oresat/oresat-c3-rf/eagle/ax5032-module-breakout/outputs/DVK2C-breakout.png

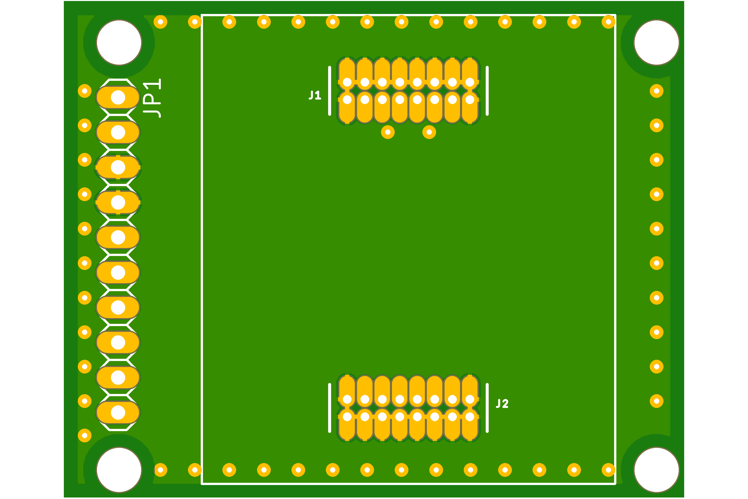
eagle/ax5032-module-breakout/outputs/DVK2C-breakout.png
