oresat/oresat-c3-rf/AxSem_Profiles/AX_C3_L_RX/TESTS/obj/Debug/TESTS/main.rst

                                      1 ;--------------------------------------------------------
                                      2 ; File Created by SDCC : free open source ANSI-C Compiler
                                      3 ; Version 3.6.0 #9615 (MINGW64)
                                      4 ;--------------------------------------------------------
                                      5 	.module main
                                      6 	.optsdcc -mmcs51 --model-small
                                      7 	
                                      8 ;--------------------------------------------------------
                                      9 ; Public variables in this module
                                     10 ;--------------------------------------------------------
                                     11 	.globl _non_fourfsk_tx1010_pattern
                                     12 	.globl _fourfsk_tx1010_pattern
                                     13 	.globl _onepattern
                                     14 	.globl _txpattern
                                     15 	.globl _main
                                     16 	.globl __sdcc_external_startup
                                     17 	.globl _set_receiveber
                                     18 	.globl _set_transmit
                                     19 	.globl _set_cw
                                     20 	.globl _lcd2_display_radio_error
                                     21 	.globl _delay_ms
                                     22 	.globl _axradio_commsleepexit
                                     23 	.globl _axradio_setup_pincfg2
                                     24 	.globl _axradio_setup_pincfg1
                                     25 	.globl _axradio_get_transmitter_pa_type
                                     26 	.globl _axradio_check_fourfsk_modulation
                                     27 	.globl _axradio_agc_thaw
                                     28 	.globl _axradio_agc_freeze
                                     29 	.globl _axradio_conv_freq_tohz
                                     30 	.globl _axradio_transmit
                                     31 	.globl _axradio_get_pllvcoi
                                     32 	.globl _axradio_get_pllrange
                                     33 	.globl _axradio_set_mode
                                     34 	.globl _axradio_cansleep
                                     35 	.globl _axradio_init
                                     36 	.globl _lcd2_writenum32
                                     37 	.globl _lcd2_writehex16
                                     38 	.globl _lcd2_writenum16
                                     39 	.globl _lcd2_writestr
                                     40 	.globl _lcd2_clear
                                     41 	.globl _lcd2_setpos
                                     42 	.globl _lcd2_portinit
                                     43 	.globl _lcd2_init
                                     44 	.globl _lcd2_txidle
                                     45 	.globl _pn15_output
                                     46 	.globl _pn15_advance
                                     47 	.globl _pn9_advance
                                     48 	.globl _wtimer_runcallbacks
                                     49 	.globl _wtimer_idle
                                     50 	.globl _wtimer_init
                                     51 	.globl _wtimer1_setconfig
                                     52 	.globl _wtimer0_setconfig
                                     53 	.globl _flash_apply_calibration
                                     54 	.globl _enter_sleep
                                     55 	.globl _hweight8
                                     56 	.globl _PORTC_7
                                     57 	.globl _PORTC_6
                                     58 	.globl _PORTC_5
                                     59 	.globl _PORTC_4
                                     60 	.globl _PORTC_3
                                     61 	.globl _PORTC_2
                                     62 	.globl _PORTC_1
                                     63 	.globl _PORTC_0
                                     64 	.globl _PORTB_7
                                     65 	.globl _PORTB_6
                                     66 	.globl _PORTB_5
                                     67 	.globl _PORTB_4
                                     68 	.globl _PORTB_3
                                     69 	.globl _PORTB_2
                                     70 	.globl _PORTB_1
                                     71 	.globl _PORTB_0
                                     72 	.globl _PORTA_7
                                     73 	.globl _PORTA_6
                                     74 	.globl _PORTA_5
                                     75 	.globl _PORTA_4
                                     76 	.globl _PORTA_3
                                     77 	.globl _PORTA_2
                                     78 	.globl _PORTA_1
                                     79 	.globl _PORTA_0
                                     80 	.globl _PINC_7
                                     81 	.globl _PINC_6
                                     82 	.globl _PINC_5
                                     83 	.globl _PINC_4
                                     84 	.globl _PINC_3
                                     85 	.globl _PINC_2
                                     86 	.globl _PINC_1
                                     87 	.globl _PINC_0
                                     88 	.globl _PINB_7
                                     89 	.globl _PINB_6
                                     90 	.globl _PINB_5
                                     91 	.globl _PINB_4
                                     92 	.globl _PINB_3
                                     93 	.globl _PINB_2
                                     94 	.globl _PINB_1
                                     95 	.globl _PINB_0
                                     96 	.globl _PINA_7
                                     97 	.globl _PINA_6
                                     98 	.globl _PINA_5
                                     99 	.globl _PINA_4
                                    100 	.globl _PINA_3
                                    101 	.globl _PINA_2
                                    102 	.globl _PINA_1
                                    103 	.globl _PINA_0
                                    104 	.globl _CY
                                    105 	.globl _AC
                                    106 	.globl _F0
                                    107 	.globl _RS1
                                    108 	.globl _RS0
                                    109 	.globl _OV
                                    110 	.globl _F1
                                    111 	.globl _P
                                    112 	.globl _IP_7
                                    113 	.globl _IP_6
                                    114 	.globl _IP_5
                                    115 	.globl _IP_4
                                    116 	.globl _IP_3
                                    117 	.globl _IP_2
                                    118 	.globl _IP_1
                                    119 	.globl _IP_0
                                    120 	.globl _EA
                                    121 	.globl _IE_7
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
                                    198 	.globl _WTCFGB
                                    199 	.globl _WTCFGA
                                    200 	.globl _WDTRESET
                                    201 	.globl _WDTCFG
                                    202 	.globl _U1STATUS
                                    203 	.globl _U1SHREG
                                    204 	.globl _U1MODE
                                    205 	.globl _U1CTRL
                                    206 	.globl _U0STATUS
                                    207 	.globl _U0SHREG
                                    208 	.globl _U0MODE
                                    209 	.globl _U0CTRL
                                    210 	.globl _T2STATUS
                                    211 	.globl _T2PERIOD
                                    212 	.globl _T2PERIOD1
                                    213 	.globl _T2PERIOD0
                                    214 	.globl _T2MODE
                                    215 	.globl _T2CNT
                                    216 	.globl _T2CNT1
                                    217 	.globl _T2CNT0
                                    218 	.globl _T2CLKSRC
                                    219 	.globl _T1STATUS
                                    220 	.globl _T1PERIOD
                                    221 	.globl _T1PERIOD1
                                    222 	.globl _T1PERIOD0
                                    223 	.globl _T1MODE
                                    224 	.globl _T1CNT
                                    225 	.globl _T1CNT1
                                    226 	.globl _T1CNT0
                                    227 	.globl _T1CLKSRC
                                    228 	.globl _T0STATUS
                                    229 	.globl _T0PERIOD
                                    230 	.globl _T0PERIOD1
                                    231 	.globl _T0PERIOD0
                                    232 	.globl _T0MODE
                                    233 	.globl _T0CNT
                                    234 	.globl _T0CNT1
                                    235 	.globl _T0CNT0
                                    236 	.globl _T0CLKSRC
                                    237 	.globl _SPSTATUS
                                    238 	.globl _SPSHREG
                                    239 	.globl _SPMODE
                                    240 	.globl _SPCLKSRC
                                    241 	.globl _RADIOSTAT
                                    242 	.globl _RADIOSTAT1
                                    243 	.globl _RADIOSTAT0
                                    244 	.globl _RADIODATA
                                    245 	.globl _RADIODATA3
                                    246 	.globl _RADIODATA2
                                    247 	.globl _RADIODATA1
                                    248 	.globl _RADIODATA0
                                    249 	.globl _RADIOADDR
                                    250 	.globl _RADIOADDR1
                                    251 	.globl _RADIOADDR0
                                    252 	.globl _RADIOACC
                                    253 	.globl _OC1STATUS
                                    254 	.globl _OC1PIN
                                    255 	.globl _OC1MODE
                                    256 	.globl _OC1COMP
                                    257 	.globl _OC1COMP1
                                    258 	.globl _OC1COMP0
                                    259 	.globl _OC0STATUS
                                    260 	.globl _OC0PIN
                                    261 	.globl _OC0MODE
                                    262 	.globl _OC0COMP
                                    263 	.globl _OC0COMP1
                                    264 	.globl _OC0COMP0
                                    265 	.globl _NVSTATUS
                                    266 	.globl _NVKEY
                                    267 	.globl _NVDATA
                                    268 	.globl _NVDATA1
                                    269 	.globl _NVDATA0
                                    270 	.globl _NVADDR
                                    271 	.globl _NVADDR1
                                    272 	.globl _NVADDR0
                                    273 	.globl _IC1STATUS
                                    274 	.globl _IC1MODE
                                    275 	.globl _IC1CAPT
                                    276 	.globl _IC1CAPT1
                                    277 	.globl _IC1CAPT0
                                    278 	.globl _IC0STATUS
                                    279 	.globl _IC0MODE
                                    280 	.globl _IC0CAPT
                                    281 	.globl _IC0CAPT1
                                    282 	.globl _IC0CAPT0
                                    283 	.globl _PORTR
                                    284 	.globl _PORTC
                                    285 	.globl _PORTB
                                    286 	.globl _PORTA
                                    287 	.globl _PINR
                                    288 	.globl _PINC
                                    289 	.globl _PINB
                                    290 	.globl _PINA
                                    291 	.globl _DIRR
                                    292 	.globl _DIRC
                                    293 	.globl _DIRB
                                    294 	.globl _DIRA
                                    295 	.globl _DBGLNKSTAT
                                    296 	.globl _DBGLNKBUF
                                    297 	.globl _CODECONFIG
                                    298 	.globl _CLKSTAT
                                    299 	.globl _CLKCON
                                    300 	.globl _ANALOGCOMP
                                    301 	.globl _ADCCONV
                                    302 	.globl _ADCCLKSRC
                                    303 	.globl _ADCCH3CONFIG
                                    304 	.globl _ADCCH2CONFIG
                                    305 	.globl _ADCCH1CONFIG
                                    306 	.globl _ADCCH0CONFIG
                                    307 	.globl __XPAGE
                                    308 	.globl _XPAGE
                                    309 	.globl _SP
                                    310 	.globl _PSW
                                    311 	.globl _PCON
                                    312 	.globl _IP
                                    313 	.globl _IE
                                    314 	.globl _EIP
                                    315 	.globl _EIE
                                    316 	.globl _E2IP
                                    317 	.globl _E2IE
                                    318 	.globl _DPS
                                    319 	.globl _DPTR1
                                    320 	.globl _DPTR0
                                    321 	.globl _DPL1
                                    322 	.globl _DPL
                                    323 	.globl _DPH1
                                    324 	.globl _DPH
                                    325 	.globl _B
                                    326 	.globl _ACC
                                    327 	.globl _txdata
                                    328 	.globl _XTALREADY
                                    329 	.globl _XTALOSC
                                    330 	.globl _XTALAMPL
                                    331 	.globl _SILICONREV
                                    332 	.globl _SCRATCH3
                                    333 	.globl _SCRATCH2
                                    334 	.globl _SCRATCH1
                                    335 	.globl _SCRATCH0
                                    336 	.globl _RADIOMUX
                                    337 	.globl _RADIOFSTATADDR
                                    338 	.globl _RADIOFSTATADDR1
                                    339 	.globl _RADIOFSTATADDR0
                                    340 	.globl _RADIOFDATAADDR
                                    341 	.globl _RADIOFDATAADDR1
                                    342 	.globl _RADIOFDATAADDR0
                                    343 	.globl _OSCRUN
                                    344 	.globl _OSCREADY
                                    345 	.globl _OSCFORCERUN
                                    346 	.globl _OSCCALIB
                                    347 	.globl _MISCCTRL
                                    348 	.globl _LPXOSCGM
                                    349 	.globl _LPOSCREF
                                    350 	.globl _LPOSCREF1
                                    351 	.globl _LPOSCREF0
                                    352 	.globl _LPOSCPER
                                    353 	.globl _LPOSCPER1
                                    354 	.globl _LPOSCPER0
                                    355 	.globl _LPOSCKFILT
                                    356 	.globl _LPOSCKFILT1
                                    357 	.globl _LPOSCKFILT0
                                    358 	.globl _LPOSCFREQ
                                    359 	.globl _LPOSCFREQ1
                                    360 	.globl _LPOSCFREQ0
                                    361 	.globl _LPOSCCONFIG
                                    362 	.globl _PINSEL
                                    363 	.globl _PINCHGC
                                    364 	.globl _PINCHGB
                                    365 	.globl _PINCHGA
                                    366 	.globl _PALTRADIO
                                    367 	.globl _PALTC
                                    368 	.globl _PALTB
                                    369 	.globl _PALTA
                                    370 	.globl _INTCHGC
                                    371 	.globl _INTCHGB
                                    372 	.globl _INTCHGA
                                    373 	.globl _EXTIRQ
                                    374 	.globl _GPIOENABLE
                                    375 	.globl _ANALOGA
                                    376 	.globl _FRCOSCREF
                                    377 	.globl _FRCOSCREF1
                                    378 	.globl _FRCOSCREF0
                                    379 	.globl _FRCOSCPER
                                    380 	.globl _FRCOSCPER1
                                    381 	.globl _FRCOSCPER0
                                    382 	.globl _FRCOSCKFILT
                                    383 	.globl _FRCOSCKFILT1
                                    384 	.globl _FRCOSCKFILT0
                                    385 	.globl _FRCOSCFREQ
                                    386 	.globl _FRCOSCFREQ1
                                    387 	.globl _FRCOSCFREQ0
                                    388 	.globl _FRCOSCCTRL
                                    389 	.globl _FRCOSCCONFIG
                                    390 	.globl _DMA1CONFIG
                                    391 	.globl _DMA1ADDR
                                    392 	.globl _DMA1ADDR1
                                    393 	.globl _DMA1ADDR0
                                    394 	.globl _DMA0CONFIG
                                    395 	.globl _DMA0ADDR
                                    396 	.globl _DMA0ADDR1
                                    397 	.globl _DMA0ADDR0
                                    398 	.globl _ADCTUNE2
                                    399 	.globl _ADCTUNE1
                                    400 	.globl _ADCTUNE0
                                    401 	.globl _ADCCH3VAL
                                    402 	.globl _ADCCH3VAL1
                                    403 	.globl _ADCCH3VAL0
                                    404 	.globl _ADCCH2VAL
                                    405 	.globl _ADCCH2VAL1
                                    406 	.globl _ADCCH2VAL0
                                    407 	.globl _ADCCH1VAL
                                    408 	.globl _ADCCH1VAL1
                                    409 	.globl _ADCCH1VAL0
                                    410 	.globl _ADCCH0VAL
                                    411 	.globl _ADCCH0VAL1
                                    412 	.globl _ADCCH0VAL0
                                    413 	.globl _acquire_agc
                                    414 	.globl _errors2
                                    415 	.globl _errors
                                    416 	.globl _bytes
                                    417 	.globl _scr
                                    418 	.globl _BER_TEST
                                    419 	.globl _coldstart
                                    420 	.globl _axradio_statuschange
                                    421 	.globl _enable_radio_interrupt_in_mcu_pin
                                    422 	.globl _disable_radio_interrupt_in_mcu_pin
                                    423 ;--------------------------------------------------------
                                    424 ; special function registers
                                    425 ;--------------------------------------------------------
                                    426 	.area RSEG    (ABS,DATA)
      000000                        427 	.org 0x0000
                           0000E0   428 G$ACC$0$0 == 0x00e0
                           0000E0   429 _ACC	=	0x00e0
                           0000F0   430 G$B$0$0 == 0x00f0
                           0000F0   431 _B	=	0x00f0
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
      000028                        994 _bytes::
      000028                        995 	.ds 4
                           00000A   996 G$errors$0$0==.
      00002C                        997 _errors::
      00002C                        998 	.ds 4
                           00000E   999 G$errors2$0$0==.
      000030                       1000 _errors2::
      000030                       1001 	.ds 4
                           000012  1002 G$acquire_agc$0$0==.
      000034                       1003 _acquire_agc::
      000034                       1004 	.ds 1
                           000013  1005 Lmain.process_ber$i$2$344==.
      000035                       1006 _process_ber_i_2_344:
      000035                       1007 	.ds 1
                           000014  1008 Lmain.process_ber$sloc0$1$0==.
      000036                       1009 _process_ber_sloc0_1_0:
      000036                       1010 	.ds 1
                           000015  1011 Lmain.process_ber$sloc1$1$0==.
      000037                       1012 _process_ber_sloc1_1_0:
      000037                       1013 	.ds 1
                           000016  1014 Lmain.si_write_reg$data$1$403==.
      000038                       1015 _si_write_reg_PARM_2:
      000038                       1016 	.ds 4
                                   1017 ;--------------------------------------------------------
                                   1018 ; overlayable items in internal ram 
                                   1019 ;--------------------------------------------------------
                                   1020 	.area	OSEG    (OVR,DATA)
                                   1021 ;--------------------------------------------------------
                                   1022 ; Stack segment in internal ram 
                                   1023 ;--------------------------------------------------------
                                   1024 	.area	SSEG
      000050                       1025 __start__stack:
      000050                       1026 	.ds	1
                                   1027 
                                   1028 ;--------------------------------------------------------
                                   1029 ; indirectly addressable internal ram data
                                   1030 ;--------------------------------------------------------
                                   1031 	.area ISEG    (DATA)
                                   1032 ;--------------------------------------------------------
                                   1033 ; absolute internal ram data
                                   1034 ;--------------------------------------------------------
                                   1035 	.area IABS    (ABS,DATA)
                                   1036 	.area IABS    (ABS,DATA)
                                   1037 ;--------------------------------------------------------
                                   1038 ; bit data
                                   1039 ;--------------------------------------------------------
                                   1040 	.area BSEG    (BIT)
                           000000  1041 Lmain._sdcc_external_startup$sloc0$1$0==.
      000001                       1042 __sdcc_external_startup_sloc0_1_0:
      000001                       1043 	.ds 1
                                   1044 ;--------------------------------------------------------
                                   1045 ; paged external ram data
                                   1046 ;--------------------------------------------------------
                                   1047 	.area PSEG    (PAG,XDATA)
                                   1048 ;--------------------------------------------------------
                                   1049 ; external ram data
                                   1050 ;--------------------------------------------------------
                                   1051 	.area XSEG    (XDATA)
                           007020  1052 G$ADCCH0VAL0$0$0 == 0x7020
                           007020  1053 _ADCCH0VAL0	=	0x7020
                           007021  1054 G$ADCCH0VAL1$0$0 == 0x7021
                           007021  1055 _ADCCH0VAL1	=	0x7021
                           007020  1056 G$ADCCH0VAL$0$0 == 0x7020
                           007020  1057 _ADCCH0VAL	=	0x7020
                           007022  1058 G$ADCCH1VAL0$0$0 == 0x7022
                           007022  1059 _ADCCH1VAL0	=	0x7022
                           007023  1060 G$ADCCH1VAL1$0$0 == 0x7023
                           007023  1061 _ADCCH1VAL1	=	0x7023
                           007022  1062 G$ADCCH1VAL$0$0 == 0x7022
                           007022  1063 _ADCCH1VAL	=	0x7022
                           007024  1064 G$ADCCH2VAL0$0$0 == 0x7024
                           007024  1065 _ADCCH2VAL0	=	0x7024
                           007025  1066 G$ADCCH2VAL1$0$0 == 0x7025
                           007025  1067 _ADCCH2VAL1	=	0x7025
                           007024  1068 G$ADCCH2VAL$0$0 == 0x7024
                           007024  1069 _ADCCH2VAL	=	0x7024
                           007026  1070 G$ADCCH3VAL0$0$0 == 0x7026
                           007026  1071 _ADCCH3VAL0	=	0x7026
                           007027  1072 G$ADCCH3VAL1$0$0 == 0x7027
                           007027  1073 _ADCCH3VAL1	=	0x7027
                           007026  1074 G$ADCCH3VAL$0$0 == 0x7026
                           007026  1075 _ADCCH3VAL	=	0x7026
                           007028  1076 G$ADCTUNE0$0$0 == 0x7028
                           007028  1077 _ADCTUNE0	=	0x7028
                           007029  1078 G$ADCTUNE1$0$0 == 0x7029
                           007029  1079 _ADCTUNE1	=	0x7029
                           00702A  1080 G$ADCTUNE2$0$0 == 0x702a
                           00702A  1081 _ADCTUNE2	=	0x702a
                           007010  1082 G$DMA0ADDR0$0$0 == 0x7010
                           007010  1083 _DMA0ADDR0	=	0x7010
                           007011  1084 G$DMA0ADDR1$0$0 == 0x7011
                           007011  1085 _DMA0ADDR1	=	0x7011
                           007010  1086 G$DMA0ADDR$0$0 == 0x7010
                           007010  1087 _DMA0ADDR	=	0x7010
                           007014  1088 G$DMA0CONFIG$0$0 == 0x7014
                           007014  1089 _DMA0CONFIG	=	0x7014
                           007012  1090 G$DMA1ADDR0$0$0 == 0x7012
                           007012  1091 _DMA1ADDR0	=	0x7012
                           007013  1092 G$DMA1ADDR1$0$0 == 0x7013
                           007013  1093 _DMA1ADDR1	=	0x7013
                           007012  1094 G$DMA1ADDR$0$0 == 0x7012
                           007012  1095 _DMA1ADDR	=	0x7012
                           007015  1096 G$DMA1CONFIG$0$0 == 0x7015
                           007015  1097 _DMA1CONFIG	=	0x7015
                           007070  1098 G$FRCOSCCONFIG$0$0 == 0x7070
                           007070  1099 _FRCOSCCONFIG	=	0x7070
                           007071  1100 G$FRCOSCCTRL$0$0 == 0x7071
                           007071  1101 _FRCOSCCTRL	=	0x7071
                           007076  1102 G$FRCOSCFREQ0$0$0 == 0x7076
                           007076  1103 _FRCOSCFREQ0	=	0x7076
                           007077  1104 G$FRCOSCFREQ1$0$0 == 0x7077
                           007077  1105 _FRCOSCFREQ1	=	0x7077
                           007076  1106 G$FRCOSCFREQ$0$0 == 0x7076
                           007076  1107 _FRCOSCFREQ	=	0x7076
                           007072  1108 G$FRCOSCKFILT0$0$0 == 0x7072
                           007072  1109 _FRCOSCKFILT0	=	0x7072
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
                           00FC00  1224 Fmain$flash_calsector$0$0 == 0xfc00
                           00FC00  1225 _flash_calsector	=	0xfc00
                           000000  1226 G$txdata$0$0==.
      00029E                       1227 _txdata::
      00029E                       1228 	.ds 8
                                   1229 ;--------------------------------------------------------
                                   1230 ; absolute external ram data
                                   1231 ;--------------------------------------------------------
                                   1232 	.area XABS    (ABS,XDATA)
                                   1233 ;--------------------------------------------------------
                                   1234 ; external initialized ram data
                                   1235 ;--------------------------------------------------------
                                   1236 	.area XISEG   (XDATA)
                                   1237 	.area HOME    (CODE)
                                   1238 	.area GSINIT0 (CODE)
                                   1239 	.area GSINIT1 (CODE)
                                   1240 	.area GSINIT2 (CODE)
                                   1241 	.area GSINIT3 (CODE)
                                   1242 	.area GSINIT4 (CODE)
                                   1243 	.area GSINIT5 (CODE)
                                   1244 	.area GSINIT  (CODE)
                                   1245 	.area GSFINAL (CODE)
                                   1246 	.area CSEG    (CODE)
                                   1247 ;--------------------------------------------------------
                                   1248 ; interrupt vector 
                                   1249 ;--------------------------------------------------------
                                   1250 	.area HOME    (CODE)
      000000                       1251 __interrupt_vect:
      000000 02 03 11         [24] 1252 	ljmp	__sdcc_gsinit_startup
      000003 32               [24] 1253 	reti
      000004                       1254 	.ds	7
      00000B 02 00 B1         [24] 1255 	ljmp	_wtimer_irq
      00000E                       1256 	.ds	5
      000013 32               [24] 1257 	reti
      000014                       1258 	.ds	7
      00001B 32               [24] 1259 	reti
      00001C                       1260 	.ds	7
      000023 02 11 BF         [24] 1261 	ljmp	_axradio_isr
      000026                       1262 	.ds	5
      00002B 32               [24] 1263 	reti
      00002C                       1264 	.ds	7
      000033 02 3C 46         [24] 1265 	ljmp	_pwrmgmt_irq
      000036                       1266 	.ds	5
      00003B 32               [24] 1267 	reti
      00003C                       1268 	.ds	7
      000043 32               [24] 1269 	reti
      000044                       1270 	.ds	7
      00004B 32               [24] 1271 	reti
      00004C                       1272 	.ds	7
      000053 02 50 1F         [24] 1273 	ljmp	_lcd2_irq
      000056                       1274 	.ds	5
      00005B 02 02 A3         [24] 1275 	ljmp	_uart0_irq
      00005E                       1276 	.ds	5
      000063 02 02 DA         [24] 1277 	ljmp	_uart1_irq
      000066                       1278 	.ds	5
      00006B 32               [24] 1279 	reti
      00006C                       1280 	.ds	7
      000073 32               [24] 1281 	reti
      000074                       1282 	.ds	7
      00007B 32               [24] 1283 	reti
      00007C                       1284 	.ds	7
      000083 32               [24] 1285 	reti
      000084                       1286 	.ds	7
      00008B 32               [24] 1287 	reti
      00008C                       1288 	.ds	7
      000093 32               [24] 1289 	reti
      000094                       1290 	.ds	7
      00009B 32               [24] 1291 	reti
      00009C                       1292 	.ds	7
      0000A3 32               [24] 1293 	reti
      0000A4                       1294 	.ds	7
      0000AB 02 02 6C         [24] 1295 	ljmp	_dbglink_irq
                                   1296 ;--------------------------------------------------------
                                   1297 ; global & static initialisations
                                   1298 ;--------------------------------------------------------
                                   1299 	.area HOME    (CODE)
                                   1300 	.area GSINIT  (CODE)
                                   1301 	.area GSFINAL (CODE)
                                   1302 	.area GSINIT  (CODE)
                                   1303 	.globl __sdcc_gsinit_startup
                                   1304 	.globl __sdcc_program_startup
                                   1305 	.globl __start__stack
                                   1306 	.globl __mcs51_genXINIT
                                   1307 	.globl __mcs51_genXRAMCLEAR
                                   1308 	.globl __mcs51_genRAMCLEAR
                           000000  1309 	C$main.c$66$1$435 ==.
                                   1310 ;	main.c:66: uint8_t __data coldstart = 1; /* caution: initialization with 1 is necessary! Variables are initialized upon _sdcc_external_startup returning 0 -> the coldstart value returned from _sdcc_external startup does not survive in the coldstart case */
      00038A 75 22 01         [24] 1311 	mov	_coldstart,#0x01
                                   1312 	.area GSFINAL (CODE)
      00038D 02 00 AE         [24] 1313 	ljmp	__sdcc_program_startup
                                   1314 ;--------------------------------------------------------
                                   1315 ; Home
                                   1316 ;--------------------------------------------------------
                                   1317 	.area HOME    (CODE)
                                   1318 	.area HOME    (CODE)
      0000AE                       1319 __sdcc_program_startup:
      0000AE 02 42 B9         [24] 1320 	ljmp	_main
                                   1321 ;	return from main will return to caller
                                   1322 ;--------------------------------------------------------
                                   1323 ; code
                                   1324 ;--------------------------------------------------------
                                   1325 	.area CSEG    (CODE)
                                   1326 ;------------------------------------------------------------
                                   1327 ;Allocation info for local variables in function 'pwrmgmt_irq'
                                   1328 ;------------------------------------------------------------
                                   1329 ;pc                        Allocated to registers r7 
                                   1330 ;------------------------------------------------------------
                           000000  1331 	Fmain$pwrmgmt_irq$0$0 ==.
                           000000  1332 	C$main.c$159$0$0 ==.
                                   1333 ;	main.c:159: static void pwrmgmt_irq(void) __interrupt(INT_POWERMGMT)
                                   1334 ;	-----------------------------------------
                                   1335 ;	 function pwrmgmt_irq
                                   1336 ;	-----------------------------------------
      003C46                       1337 _pwrmgmt_irq:
                           000007  1338 	ar7 = 0x07
                           000006  1339 	ar6 = 0x06
                           000005  1340 	ar5 = 0x05
                           000004  1341 	ar4 = 0x04
                           000003  1342 	ar3 = 0x03
                           000002  1343 	ar2 = 0x02
                           000001  1344 	ar1 = 0x01
                           000000  1345 	ar0 = 0x00
      003C46 C0 E0            [24] 1346 	push	acc
      003C48 C0 82            [24] 1347 	push	dpl
      003C4A C0 83            [24] 1348 	push	dph
      003C4C C0 07            [24] 1349 	push	ar7
      003C4E C0 D0            [24] 1350 	push	psw
      003C50 75 D0 00         [24] 1351 	mov	psw,#0x00
                           00000D  1352 	C$main.c$161$1$0 ==.
                                   1353 ;	main.c:161: uint8_t pc = PCON;
                           00000D  1354 	C$main.c$163$1$337 ==.
                                   1355 ;	main.c:163: if (!(pc & 0x80))
      003C53 E5 87            [12] 1356 	mov	a,_PCON
      003C55 FF               [12] 1357 	mov	r7,a
      003C56 20 E7 02         [24] 1358 	jb	acc.7,00102$
                           000013  1359 	C$main.c$164$1$337 ==.
                                   1360 ;	main.c:164: return;
      003C59 80 10            [24] 1361 	sjmp	00106$
      003C5B                       1362 00102$:
                           000015  1363 	C$main.c$166$1$337 ==.
                                   1364 ;	main.c:166: GPIOENABLE = 0;
      003C5B 90 70 0C         [24] 1365 	mov	dptr,#_GPIOENABLE
      003C5E E4               [12] 1366 	clr	a
      003C5F F0               [24] 1367 	movx	@dptr,a
                           00001A  1368 	C$main.c$167$1$337 ==.
                                   1369 ;	main.c:167: IE = EIE = E2IE = 0;
                                   1370 ;	1-genFromRTrack replaced	mov	_E2IE,#0x00
      003C60 F5 A0            [12] 1371 	mov	_E2IE,a
                                   1372 ;	1-genFromRTrack replaced	mov	_EIE,#0x00
      003C62 F5 98            [12] 1373 	mov	_EIE,a
                                   1374 ;	1-genFromRTrack replaced	mov	_IE,#0x00
      003C64 F5 A8            [12] 1375 	mov	_IE,a
      003C66                       1376 00104$:
                           000020  1377 	C$main.c$170$1$337 ==.
                                   1378 ;	main.c:170: PCON |= 0x01;
      003C66 43 87 01         [24] 1379 	orl	_PCON,#0x01
      003C69 80 FB            [24] 1380 	sjmp	00104$
      003C6B                       1381 00106$:
      003C6B D0 D0            [24] 1382 	pop	psw
      003C6D D0 07            [24] 1383 	pop	ar7
      003C6F D0 83            [24] 1384 	pop	dph
      003C71 D0 82            [24] 1385 	pop	dpl
      003C73 D0 E0            [24] 1386 	pop	acc
                           00002F  1387 	C$main.c$171$1$337 ==.
                           00002F  1388 	XFmain$pwrmgmt_irq$0$0 ==.
      003C75 32               [24] 1389 	reti
                                   1390 ;	eliminated unneeded push/pop b
                                   1391 ;------------------------------------------------------------
                                   1392 ;Allocation info for local variables in function 'correct_ber'
                                   1393 ;------------------------------------------------------------
                                   1394 ;x                         Allocated to registers r0 r1 r2 r3 
                                   1395 ;------------------------------------------------------------
                           000030  1396 	Fmain$correct_ber$0$0 ==.
                           000030  1397 	C$main.c$174$1$337 ==.
                                   1398 ;	main.c:174: static void correct_ber(void)
                                   1399 ;	-----------------------------------------
                                   1400 ;	 function correct_ber
                                   1401 ;	-----------------------------------------
      003C76                       1402 _correct_ber:
                           000030  1403 	C$main.c$183$1$339 ==.
                                   1404 ;	main.c:183: x *= errors;
      003C76 85 2C 82         [24] 1405 	mov	dpl,_errors
      003C79 85 2D 83         [24] 1406 	mov	dph,(_errors + 1)
      003C7C 85 2E F0         [24] 1407 	mov	b,(_errors + 2)
      003C7F E5 2F            [12] 1408 	mov	a,(_errors + 3)
      003C81 12 4C C4         [24] 1409 	lcall	___ulong2fs
      003C84 AC 82            [24] 1410 	mov	r4,dpl
      003C86 AD 83            [24] 1411 	mov	r5,dph
      003C88 AE F0            [24] 1412 	mov	r6,b
      003C8A FF               [12] 1413 	mov	r7,a
      003C8B C0 07            [24] 1414 	push	ar7
      003C8D C0 06            [24] 1415 	push	ar6
      003C8F C0 05            [24] 1416 	push	ar5
      003C91 C0 04            [24] 1417 	push	ar4
      003C93 C0 04            [24] 1418 	push	ar4
      003C95 C0 05            [24] 1419 	push	ar5
      003C97 C0 06            [24] 1420 	push	ar6
      003C99 C0 07            [24] 1421 	push	ar7
      003C9B 90 7F C3         [24] 1422 	mov	dptr,#0x7fc3
      003C9E 75 F0 3D         [24] 1423 	mov	b,#0x3d
      003CA1 74 39            [12] 1424 	mov	a,#0x39
      003CA3 12 44 DB         [24] 1425 	lcall	___fsmul
      003CA6 A8 82            [24] 1426 	mov	r0,dpl
      003CA8 A9 83            [24] 1427 	mov	r1,dph
      003CAA AA F0            [24] 1428 	mov	r2,b
      003CAC FB               [12] 1429 	mov	r3,a
      003CAD E5 81            [12] 1430 	mov	a,sp
      003CAF 24 FC            [12] 1431 	add	a,#0xfc
      003CB1 F5 81            [12] 1432 	mov	sp,a
                           00006D  1433 	C$main.c$184$1$339 ==.
                                   1434 ;	main.c:184: x *= x;
      003CB3 C0 00            [24] 1435 	push	ar0
      003CB5 C0 01            [24] 1436 	push	ar1
      003CB7 C0 02            [24] 1437 	push	ar2
      003CB9 C0 03            [24] 1438 	push	ar3
      003CBB 88 82            [24] 1439 	mov	dpl,r0
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
      003D4F F5 2F            [12] 1520 	mov	(_errors + 3),a
                           00010B  1521 	C$main.c$193$1$339 ==.
                                   1522 ;	main.c:193: }
                           00010B  1523 	C$main.c$194$1$339 ==.
                           00010B  1524 	XFmain$correct_ber$0$0 ==.
      003D51 22               [24] 1525 	ret
                                   1526 ;------------------------------------------------------------
                                   1527 ;Allocation info for local variables in function 'process_ber'
                                   1528 ;------------------------------------------------------------
                                   1529 ;st                        Allocated to registers r6 r7 
                                   1530 ;fourfsk                   Allocated to registers 
                                   1531 ;i                         Allocated with name '_process_ber_i_2_344'
                                   1532 ;p                         Allocated to registers 
                                   1533 ;databyte                  Allocated to registers 
                                   1534 ;databyte                  Allocated to registers 
                                   1535 ;databyte                  Allocated to registers 
                                   1536 ;databyte                  Allocated to registers 
                                   1537 ;databyte                  Allocated to registers 
                                   1538 ;sloc0                     Allocated with name '_process_ber_sloc0_1_0'
                                   1539 ;sloc1                     Allocated with name '_process_ber_sloc1_1_0'
                                   1540 ;------------------------------------------------------------
                           00010C  1541 	Fmain$process_ber$0$0 ==.
                           00010C  1542 	C$main.c$196$1$339 ==.
                                   1543 ;	main.c:196: static void process_ber(struct axradio_status __xdata *st)
                                   1544 ;	-----------------------------------------
                                   1545 ;	 function process_ber
                                   1546 ;	-----------------------------------------
      003D52                       1547 _process_ber:
      003D52 AE 82            [24] 1548 	mov	r6,dpl
      003D54 AF 83            [24] 1549 	mov	r7,dph
                           000110  1550 	C$main.c$198$1$343 ==.
                                   1551 ;	main.c:198: uint8_t fourfsk = axradio_check_fourfsk_modulation();
      003D56 C0 07            [24] 1552 	push	ar7
      003D58 C0 06            [24] 1553 	push	ar6
      003D5A 12 3A 50         [24] 1554 	lcall	_axradio_check_fourfsk_modulation
      003D5D D0 06            [24] 1555 	pop	ar6
      003D5F D0 07            [24] 1556 	pop	ar7
                           00011B  1557 	C$main.c$200$2$344 ==.
                                   1558 ;	main.c:200: uint8_t i = st->u.rx.pktlen;
      003D61 74 06            [12] 1559 	mov	a,#0x06
      003D63 2E               [12] 1560 	add	a,r6
      003D64 FE               [12] 1561 	mov	r6,a
      003D65 E4               [12] 1562 	clr	a
      003D66 3F               [12] 1563 	addc	a,r7
      003D67 FF               [12] 1564 	mov	r7,a
      003D68 74 18            [12] 1565 	mov	a,#0x18
      003D6A 2E               [12] 1566 	add	a,r6
      003D6B F5 82            [12] 1567 	mov	dpl,a
      003D6D E4               [12] 1568 	clr	a
      003D6E 3F               [12] 1569 	addc	a,r7
      003D6F F5 83            [12] 1570 	mov	dph,a
      003D71 E0               [24] 1571 	movx	a,@dptr
      003D72 FC               [12] 1572 	mov	r4,a
      003D73 A3               [24] 1573 	inc	dptr
      003D74 E0               [24] 1574 	movx	a,@dptr
      003D75 8C 35            [24] 1575 	mov	_process_ber_i_2_344,r4
                           000131  1576 	C$main.c$201$2$344 ==.
                                   1577 ;	main.c:201: bytes -= i;
      003D77 AA 35            [24] 1578 	mov	r2,_process_ber_i_2_344
      003D79 E4               [12] 1579 	clr	a
      003D7A FB               [12] 1580 	mov	r3,a
      003D7B FC               [12] 1581 	mov	r4,a
      003D7C FD               [12] 1582 	mov	r5,a
      003D7D E5 28            [12] 1583 	mov	a,_bytes
      003D7F C3               [12] 1584 	clr	c
      003D80 9A               [12] 1585 	subb	a,r2
      003D81 F5 28            [12] 1586 	mov	_bytes,a
      003D83 E5 29            [12] 1587 	mov	a,(_bytes + 1)
      003D85 9B               [12] 1588 	subb	a,r3
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
      003E5F F5 2D            [12] 1765 	mov	(_errors + 1),a
      003E61 E4               [12] 1766 	clr	a
      003E62 95 2E            [12] 1767 	subb	a,(_errors + 2)
      003E64 F5 2E            [12] 1768 	mov	(_errors + 2),a
      003E66 E4               [12] 1769 	clr	a
      003E67 95 2F            [12] 1770 	subb	a,(_errors + 3)
      003E69 F5 2F            [12] 1771 	mov	(_errors + 3),a
                           000225  1772 	C$main.c$304$1$343 ==.
                                   1773 ;	main.c:304: errors = errors2;
      003E6B                       1774 00136$:
                           000225  1775 	C$main.c$307$1$343 ==.
                                   1776 ;	main.c:307: correct_ber();
      003E6B 12 3C 76         [24] 1777 	lcall	_correct_ber
      003E6E                       1778 00138$:
                           000228  1779 	C$main.c$308$1$343 ==.
                           000228  1780 	XFmain$process_ber$0$0 ==.
      003E6E 22               [24] 1781 	ret
                                   1782 ;------------------------------------------------------------
                                   1783 ;Allocation info for local variables in function 'dump_pkt'
                                   1784 ;------------------------------------------------------------
                                   1785 ;st                        Allocated to registers 
                                   1786 ;------------------------------------------------------------
                           000229  1787 	Fmain$dump_pkt$0$0 ==.
                           000229  1788 	C$main.c$310$1$343 ==.
                                   1789 ;	main.c:310: static void dump_pkt(struct axradio_status __xdata *st)
                                   1790 ;	-----------------------------------------
                                   1791 ;	 function dump_pkt
                                   1792 ;	-----------------------------------------
      003E6F                       1793 _dump_pkt:
                           000229  1794 	C$main.c$336$1$343 ==.
                                   1795 ;	main.c:336: }
                           000229  1796 	C$main.c$336$1$343 ==.
                           000229  1797 	XFmain$dump_pkt$0$0 ==.
      003E6F 22               [24] 1798 	ret
                                   1799 ;------------------------------------------------------------
                                   1800 ;Allocation info for local variables in function 'display_ber'
                                   1801 ;------------------------------------------------------------
                                   1802 ;st                        Allocated to registers r6 r7 
                                   1803 ;freqoffs                  Allocated to registers r2 r3 r4 r5 
                                   1804 ;------------------------------------------------------------
                           00022A  1805 	Fmain$display_ber$0$0 ==.
                           00022A  1806 	C$main.c$338$1$343 ==.
                                   1807 ;	main.c:338: static void display_ber(struct axradio_status __xdata *st)
                                   1808 ;	-----------------------------------------
                                   1809 ;	 function display_ber
                                   1810 ;	-----------------------------------------
      003E70                       1811 _display_ber:
      003E70 AE 82            [24] 1812 	mov	r6,dpl
      003E72 AF 83            [24] 1813 	mov	r7,dph
                           00022E  1814 	C$main.c$340$1$358 ==.
                                   1815 ;	main.c:340: int32_t freqoffs = axradio_conv_freq_tohz(st->u.rx.phy.offset);
      003E74 74 06            [12] 1816 	mov	a,#0x06
      003E76 2E               [12] 1817 	add	a,r6
      003E77 FE               [12] 1818 	mov	r6,a
      003E78 E4               [12] 1819 	clr	a
      003E79 3F               [12] 1820 	addc	a,r7
      003E7A FF               [12] 1821 	mov	r7,a
      003E7B 8E 82            [24] 1822 	mov	dpl,r6
      003E7D 8F 83            [24] 1823 	mov	dph,r7
      003E7F A3               [24] 1824 	inc	dptr
      003E80 A3               [24] 1825 	inc	dptr
      003E81 E0               [24] 1826 	movx	a,@dptr
      003E82 FA               [12] 1827 	mov	r2,a
      003E83 A3               [24] 1828 	inc	dptr
      003E84 E0               [24] 1829 	movx	a,@dptr
      003E85 FB               [12] 1830 	mov	r3,a
      003E86 A3               [24] 1831 	inc	dptr
      003E87 E0               [24] 1832 	movx	a,@dptr
      003E88 FC               [12] 1833 	mov	r4,a
      003E89 A3               [24] 1834 	inc	dptr
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
      003F0A E0               [24] 1908 	movx	a,@dptr
      003F0B FE               [12] 1909 	mov	r6,a
      003F0C A3               [24] 1910 	inc	dptr
      003F0D E0               [24] 1911 	movx	a,@dptr
      003F0E FF               [12] 1912 	mov	r7,a
      003F0F 74 01            [12] 1913 	mov	a,#0x01
      003F11 C0 E0            [24] 1914 	push	acc
      003F13 74 04            [12] 1915 	mov	a,#0x04
      003F15 C0 E0            [24] 1916 	push	acc
      003F17 8E 82            [24] 1917 	mov	dpl,r6
      003F19 8F 83            [24] 1918 	mov	dph,r7
      003F1B 12 45 7E         [24] 1919 	lcall	_lcd2_writenum16
      003F1E 15 81            [12] 1920 	dec	sp
      003F20 15 81            [12] 1921 	dec	sp
                           0002DC  1922 	C$main.c$362$1$358 ==.
                           0002DC  1923 	XFmain$display_ber$0$0 ==.
      003F22 22               [24] 1924 	ret
                                   1925 ;------------------------------------------------------------
                                   1926 ;Allocation info for local variables in function 'axradio_statuschange'
                                   1927 ;------------------------------------------------------------
                                   1928 ;st                        Allocated to registers r6 r7 
                                   1929 ;fourfsk                   Allocated to registers 
                                   1930 ;i                         Allocated to registers 
                                   1931 ;i                         Allocated to registers 
                                   1932 ;i                         Allocated to registers r2 
                                   1933 ;p                         Allocated to registers r4 r5 
                                   1934 ;------------------------------------------------------------
                           0002DD  1935 	G$axradio_statuschange$0$0 ==.
                           0002DD  1936 	C$main.c$364$1$358 ==.
                                   1937 ;	main.c:364: void axradio_statuschange(struct axradio_status __xdata *st)
                                   1938 ;	-----------------------------------------
                                   1939 ;	 function axradio_statuschange
                                   1940 ;	-----------------------------------------
      003F23                       1941 _axradio_statuschange:
      003F23 AE 82            [24] 1942 	mov	r6,dpl
      003F25 AF 83            [24] 1943 	mov	r7,dph
                           0002E1  1944 	C$main.c$366$1$360 ==.
                                   1945 ;	main.c:366: uint8_t fourfsk = axradio_check_fourfsk_modulation();
      003F27 C0 07            [24] 1946 	push	ar7
      003F29 C0 06            [24] 1947 	push	ar6
      003F2B 12 3A 50         [24] 1948 	lcall	_axradio_check_fourfsk_modulation
      003F2E D0 06            [24] 1949 	pop	ar6
      003F30 D0 07            [24] 1950 	pop	ar7
                           0002EC  1951 	C$main.c$367$1$360 ==.
                                   1952 ;	main.c:367: switch (st->status)
      003F32 8E 82            [24] 1953 	mov	dpl,r6
      003F34 8F 83            [24] 1954 	mov	dph,r7
      003F36 E0               [24] 1955 	movx	a,@dptr
      003F37 FD               [12] 1956 	mov	r5,a
      003F38 60 17            [24] 1957 	jz	00130$
      003F3A BD 03 02         [24] 1958 	cjne	r5,#0x03,00187$
      003F3D 80 08            [24] 1959 	sjmp	00105$
      003F3F                       1960 00187$:
      003F3F BD 04 02         [24] 1961 	cjne	r5,#0x04,00188$
      003F42 80 08            [24] 1962 	sjmp	00112$
      003F44                       1963 00188$:
      003F44 02 3F F2         [24] 1964 	ljmp	00161$
                           000301  1965 	C$main.c$370$2$361 ==.
                                   1966 ;	main.c:370: led0_on();
      003F47                       1967 00105$:
      003F47 D2 93            [12] 1968 	setb	_PORTC_3
                           000303  1969 	C$main.c$371$2$361 ==.
                                   1970 ;	main.c:371: break;
      003F49 02 3F F2         [24] 1971 	ljmp	00161$
                           000306  1972 	C$main.c$374$2$361 ==.
                                   1973 ;	main.c:374: led0_off();
      003F4C                       1974 00112$:
      003F4C C2 93            [12] 1975 	clr	_PORTC_3
                           000308  1976 	C$main.c$375$2$361 ==.
                                   1977 ;	main.c:375: break;
      003F4E 02 3F F2         [24] 1978 	ljmp	00161$
                           00030B  1979 	C$main.c$441$2$361 ==.
                                   1980 ;	main.c:441: case AXRADIO_STAT_RECEIVE:
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
      003FD7 75 28 E2         [24] 2106 	mov	_bytes,#0xe2
      003FDA 75 29 04         [24] 2107 	mov	(_bytes + 1),#0x04
      003FDD E4               [12] 2108 	clr	a
      003FDE F5 2A            [12] 2109 	mov	(_bytes + 2),a
      003FE0 F5 2B            [12] 2110 	mov	(_bytes + 3),a
                           00039C  2111 	C$main.c$497$3$373 ==.
                                   2112 ;	main.c:497: errors = 0;
      003FE2 F5 2C            [12] 2113 	mov	_errors,a
      003FE4 F5 2D            [12] 2114 	mov	(_errors + 1),a
      003FE6 F5 2E            [12] 2115 	mov	(_errors + 2),a
      003FE8 F5 2F            [12] 2116 	mov	(_errors + 3),a
                           0003A4  2117 	C$main.c$498$3$373 ==.
                                   2118 ;	main.c:498: errors2 = 0;
      003FEA F5 30            [12] 2119 	mov	_errors2,a
      003FEC F5 31            [12] 2120 	mov	(_errors2 + 1),a
      003FEE F5 32            [12] 2121 	mov	(_errors2 + 2),a
      003FF0 F5 33            [12] 2122 	mov	(_errors2 + 3),a
                           0003AC  2123 	C$main.c$504$1$360 ==.
                                   2124 ;	main.c:504: }
      003FF2                       2125 00161$:
                           0003AC  2126 	C$main.c$505$1$360 ==.
                           0003AC  2127 	XG$axradio_statuschange$0$0 ==.
      003FF2 22               [24] 2128 	ret
                                   2129 ;------------------------------------------------------------
                                   2130 ;Allocation info for local variables in function 'set_cw'
                                   2131 ;------------------------------------------------------------
                                   2132 ;i                         Allocated to registers r6 
                                   2133 ;------------------------------------------------------------
                           0003AD  2134 	G$set_cw$0$0 ==.
                           0003AD  2135 	C$main.c$507$1$360 ==.
                                   2136 ;	main.c:507: void set_cw(void)
                                   2137 ;	-----------------------------------------
                                   2138 ;	 function set_cw
                                   2139 ;	-----------------------------------------
      003FF3                       2140 _set_cw:
                           0003AD  2141 	C$main.c$509$1$384 ==.
                                   2142 ;	main.c:509: uint8_t i = axradio_set_mode(AXRADIO_MODE_CW_TRANSMIT);
      003FF3 75 82 03         [24] 2143 	mov	dpl,#0x03
      003FF6 12 2E 99         [24] 2144 	lcall	_axradio_set_mode
                           0003B3  2145 	C$main.c$511$1$384 ==.
                                   2146 ;	main.c:511: if (i != AXRADIO_ERR_NOERROR)
      003FF9 E5 82            [12] 2147 	mov	a,dpl
      003FFB FF               [12] 2148 	mov	r7,a
      003FFC FE               [12] 2149 	mov	r6,a
      003FFD 60 0A            [24] 2150 	jz	00103$
                           0003B9  2151 	C$main.c$513$2$385 ==.
                                   2152 ;	main.c:513: display_radio_error(i);
      003FFF 8E 82            [24] 2153 	mov	dpl,r6
      004001 12 3A 6F         [24] 2154 	lcall	_lcd2_display_radio_error
      004004                       2155 00109$:
                           0003BE  2156 	C$main.c$519$2$385 ==.
                                   2157 ;	main.c:519: enter_sleep();
      004004 12 58 00         [24] 2158 	lcall	_enter_sleep
      004007 80 FB            [24] 2159 	sjmp	00109$
      004009                       2160 00103$:
                           0003C3  2161 	C$main.c$522$1$384 ==.
                                   2162 ;	main.c:522: display_clear(0x00, 16);
      004009 74 10            [12] 2163 	mov	a,#0x10
      00400B C0 E0            [24] 2164 	push	acc
      00400D 75 82 00         [24] 2165 	mov	dpl,#0x00
      004010 12 55 56         [24] 2166 	lcall	_lcd2_clear
      004013 15 81            [12] 2167 	dec	sp
                           0003CF  2168 	C$main.c$523$1$384 ==.
                                   2169 ;	main.c:523: display_clear(0x40, 16);
      004015 74 10            [12] 2170 	mov	a,#0x10
      004017 C0 E0            [24] 2171 	push	acc
      004019 75 82 40         [24] 2172 	mov	dpl,#0x40
      00401C 12 55 56         [24] 2173 	lcall	_lcd2_clear
      00401F 15 81            [12] 2174 	dec	sp
                           0003DB  2175 	C$main.c$524$1$384 ==.
                                   2176 ;	main.c:524: display_setpos(0x00);
      004021 75 82 00         [24] 2177 	mov	dpl,#0x00
      004024 12 43 A8         [24] 2178 	lcall	_lcd2_setpos
                           0003E1  2179 	C$main.c$525$1$384 ==.
                                   2180 ;	main.c:525: display_writestr("TX CW, PA ");
      004027 90 5C DD         [24] 2181 	mov	dptr,#___str_2
      00402A 75 F0 80         [24] 2182 	mov	b,#0x80
      00402D 12 54 D0         [24] 2183 	lcall	_lcd2_writestr
                           0003EA  2184 	C$main.c$527$1$384 ==.
                                   2185 ;	main.c:527: if(axradio_get_transmitter_pa_type() == AXRADIO_DIFFERENTIAL_PA)
      004030 12 3A 64         [24] 2186 	lcall	_axradio_get_transmitter_pa_type
      004033 AF 82            [24] 2187 	mov	r7,dpl
      004035 BF 01 0B         [24] 2188 	cjne	r7,#0x01,00107$
                           0003F2  2189 	C$main.c$528$1$384 ==.
                                   2190 ;	main.c:528: display_writestr( "DI ");
      004038 90 5C E8         [24] 2191 	mov	dptr,#___str_3
      00403B 75 F0 80         [24] 2192 	mov	b,#0x80
      00403E 12 54 D0         [24] 2193 	lcall	_lcd2_writestr
      004041 80 11            [24] 2194 	sjmp	00111$
      004043                       2195 00107$:
                           0003FD  2196 	C$main.c$529$1$384 ==.
                                   2197 ;	main.c:529: else if(axradio_get_transmitter_pa_type() == AXRADIO_SINGLE_ENDED_PA)
      004043 12 3A 64         [24] 2198 	lcall	_axradio_get_transmitter_pa_type
      004046 AF 82            [24] 2199 	mov	r7,dpl
      004048 BF 02 09         [24] 2200 	cjne	r7,#0x02,00111$
                           000405  2201 	C$main.c$530$1$384 ==.
                                   2202 ;	main.c:530: display_writestr( "SE ");
      00404B 90 5C EC         [24] 2203 	mov	dptr,#___str_4
      00404E 75 F0 80         [24] 2204 	mov	b,#0x80
      004051 12 54 D0         [24] 2205 	lcall	_lcd2_writestr
      004054                       2206 00111$:
                           00040E  2207 	C$main.c$531$1$384 ==.
                           00040E  2208 	XG$set_cw$0$0 ==.
      004054 22               [24] 2209 	ret
                                   2210 ;------------------------------------------------------------
                                   2211 ;Allocation info for local variables in function 'set_transmit'
                                   2212 ;------------------------------------------------------------
                                   2213 ;i                         Allocated to registers r6 
                                   2214 ;------------------------------------------------------------
                           00040F  2215 	G$set_transmit$0$0 ==.
                           00040F  2216 	C$main.c$533$1$384 ==.
                                   2217 ;	main.c:533: void set_transmit(void)
                                   2218 ;	-----------------------------------------
                                   2219 ;	 function set_transmit
                                   2220 ;	-----------------------------------------
      004055                       2221 _set_transmit:
                           00040F  2222 	C$main.c$579$1$387 ==.
                                   2223 ;	main.c:579: i = axradio_set_mode(i);
      004055 75 82 18         [24] 2224 	mov	dpl,#0x18
      004058 12 2E 99         [24] 2225 	lcall	_axradio_set_mode
                           000415  2226 	C$main.c$581$1$387 ==.
                                   2227 ;	main.c:581: if (i != AXRADIO_ERR_NOERROR)
      00405B E5 82            [12] 2228 	mov	a,dpl
      00405D FF               [12] 2229 	mov	r7,a
      00405E FE               [12] 2230 	mov	r6,a
      00405F 60 0A            [24] 2231 	jz	00109$
                           00041B  2232 	C$main.c$583$2$389 ==.
                                   2233 ;	main.c:583: display_radio_error(i);
      004061 8E 82            [24] 2234 	mov	dpl,r6
      004063 12 3A 6F         [24] 2235 	lcall	_lcd2_display_radio_error
      004066                       2236 00121$:
                           000420  2237 	C$main.c$589$2$389 ==.
                                   2238 ;	main.c:589: enter_sleep();
      004066 12 58 00         [24] 2239 	lcall	_enter_sleep
      004069 80 FB            [24] 2240 	sjmp	00121$
      00406B                       2241 00109$:
                           000425  2242 	C$main.c$592$1$387 ==.
                                   2243 ;	main.c:592: scr.w = ~0U;
      00406B 75 24 FF         [24] 2244 	mov	(_scr + 0),#0xff
      00406E 75 25 FF         [24] 2245 	mov	(_scr + 1),#0xff
                           00042B  2246 	C$main.c$593$1$387 ==.
                                   2247 ;	main.c:593: display_clear(0x00, 16);
      004071 74 10            [12] 2248 	mov	a,#0x10
      004073 C0 E0            [24] 2249 	push	acc
      004075 75 82 00         [24] 2250 	mov	dpl,#0x00
      004078 12 55 56         [24] 2251 	lcall	_lcd2_clear
      00407B 15 81            [12] 2252 	dec	sp
                           000437  2253 	C$main.c$594$1$387 ==.
                                   2254 ;	main.c:594: display_clear(0x40, 16);
      00407D 74 10            [12] 2255 	mov	a,#0x10
      00407F C0 E0            [24] 2256 	push	acc
      004081 75 82 40         [24] 2257 	mov	dpl,#0x40
      004084 12 55 56         [24] 2258 	lcall	_lcd2_clear
      004087 15 81            [12] 2259 	dec	sp
                           000443  2260 	C$main.c$595$1$387 ==.
                                   2261 ;	main.c:595: display_setpos(0x00);
      004089 75 82 00         [24] 2262 	mov	dpl,#0x00
      00408C 12 43 A8         [24] 2263 	lcall	_lcd2_setpos
                           000449  2264 	C$main.c$616$2$390 ==.
                                   2265 ;	main.c:616: display_writestr("TX PAT, PA ");
      00408F 90 5D 22         [24] 2266 	mov	dptr,#___str_9
      004092 75 F0 80         [24] 2267 	mov	b,#0x80
      004095 12 54 D0         [24] 2268 	lcall	_lcd2_writestr
                           000452  2269 	C$main.c$620$1$387 ==.
                                   2270 ;	main.c:620: if(axradio_get_transmitter_pa_type() == AXRADIO_DIFFERENTIAL_PA)
      004098 12 3A 64         [24] 2271 	lcall	_axradio_get_transmitter_pa_type
      00409B AF 82            [24] 2272 	mov	r7,dpl
      00409D BF 01 0B         [24] 2273 	cjne	r7,#0x01,00119$
                           00045A  2274 	C$main.c$621$1$387 ==.
                                   2275 ;	main.c:621: display_writestr( "DI ");
      0040A0 90 5C E8         [24] 2276 	mov	dptr,#___str_3
      0040A3 75 F0 80         [24] 2277 	mov	b,#0x80
      0040A6 12 54 D0         [24] 2278 	lcall	_lcd2_writestr
      0040A9 80 11            [24] 2279 	sjmp	00123$
      0040AB                       2280 00119$:
                           000465  2281 	C$main.c$622$1$387 ==.
                                   2282 ;	main.c:622: else if(axradio_get_transmitter_pa_type() == AXRADIO_SINGLE_ENDED_PA)
      0040AB 12 3A 64         [24] 2283 	lcall	_axradio_get_transmitter_pa_type
      0040AE AF 82            [24] 2284 	mov	r7,dpl
      0040B0 BF 02 09         [24] 2285 	cjne	r7,#0x02,00123$
                           00046D  2286 	C$main.c$623$1$387 ==.
                                   2287 ;	main.c:623: display_writestr( "SE ");
      0040B3 90 5C EC         [24] 2288 	mov	dptr,#___str_4
      0040B6 75 F0 80         [24] 2289 	mov	b,#0x80
      0040B9 12 54 D0         [24] 2290 	lcall	_lcd2_writestr
      0040BC                       2291 00123$:
                           000476  2292 	C$main.c$624$1$387 ==.
                           000476  2293 	XG$set_transmit$0$0 ==.
      0040BC 22               [24] 2294 	ret
                                   2295 ;------------------------------------------------------------
                                   2296 ;Allocation info for local variables in function 'set_receiveber'
                                   2297 ;------------------------------------------------------------
                                   2298 ;i                         Allocated to registers r6 
                                   2299 ;------------------------------------------------------------
                           000477  2300 	G$set_receiveber$0$0 ==.
                           000477  2301 	C$main.c$626$1$387 ==.
                                   2302 ;	main.c:626: void set_receiveber(void)
                                   2303 ;	-----------------------------------------
                                   2304 ;	 function set_receiveber
                                   2305 ;	-----------------------------------------
      0040BD                       2306 _set_receiveber:
                           000477  2307 	C$main.c$669$1$392 ==.
                                   2308 ;	main.c:669: i = axradio_set_mode(i);
      0040BD 75 82 2A         [24] 2309 	mov	dpl,#0x2a
      0040C0 12 2E 99         [24] 2310 	lcall	_axradio_set_mode
                           00047D  2311 	C$main.c$671$1$392 ==.
                                   2312 ;	main.c:671: if (i != AXRADIO_ERR_NOERROR)
      0040C3 E5 82            [12] 2313 	mov	a,dpl
      0040C5 FF               [12] 2314 	mov	r7,a
      0040C6 FE               [12] 2315 	mov	r6,a
      0040C7 60 0A            [24] 2316 	jz	00109$
                           000483  2317 	C$main.c$673$2$394 ==.
                                   2318 ;	main.c:673: display_radio_error(i);
      0040C9 8E 82            [24] 2319 	mov	dpl,r6
      0040CB 12 3A 6F         [24] 2320 	lcall	_lcd2_display_radio_error
      0040CE                       2321 00110$:
                           000488  2322 	C$main.c$679$2$394 ==.
                                   2323 ;	main.c:679: enter_sleep();
      0040CE 12 58 00         [24] 2324 	lcall	_enter_sleep
      0040D1 80 FB            [24] 2325 	sjmp	00110$
      0040D3                       2326 00109$:
                           00048D  2327 	C$main.c$682$1$392 ==.
                                   2328 ;	main.c:682: display_clear(0x00, 16);
      0040D3 74 10            [12] 2329 	mov	a,#0x10
      0040D5 C0 E0            [24] 2330 	push	acc
      0040D7 75 82 00         [24] 2331 	mov	dpl,#0x00
      0040DA 12 55 56         [24] 2332 	lcall	_lcd2_clear
      0040DD 15 81            [12] 2333 	dec	sp
                           000499  2334 	C$main.c$683$1$392 ==.
                                   2335 ;	main.c:683: display_clear(0x40, 16);
      0040DF 74 10            [12] 2336 	mov	a,#0x10
      0040E1 C0 E0            [24] 2337 	push	acc
      0040E3 75 82 40         [24] 2338 	mov	dpl,#0x40
      0040E6 12 55 56         [24] 2339 	lcall	_lcd2_clear
      0040E9 15 81            [12] 2340 	dec	sp
                           0004A5  2341 	C$main.c$684$1$392 ==.
                                   2342 ;	main.c:684: display_setpos(0x00);
      0040EB 75 82 00         [24] 2343 	mov	dpl,#0x00
      0040EE 12 43 A8         [24] 2344 	lcall	_lcd2_setpos
                           0004AB  2345 	C$main.c$685$1$392 ==.
                                   2346 ;	main.c:685: display_writestr("RX");
      0040F1 90 5D 2E         [24] 2347 	mov	dptr,#___str_10
      0040F4 75 F0 80         [24] 2348 	mov	b,#0x80
      0040F7 12 54 D0         [24] 2349 	lcall	_lcd2_writestr
                           0004B4  2350 	C$main.c$687$1$392 ==.
                                   2351 ;	main.c:687: display_setpos(0x40);
      0040FA 75 82 40         [24] 2352 	mov	dpl,#0x40
      0040FD 12 43 A8         [24] 2353 	lcall	_lcd2_setpos
                           0004BA  2354 	C$main.c$688$1$392 ==.
                                   2355 ;	main.c:688: display_writestr("BER=?");
      004100 90 5D 31         [24] 2356 	mov	dptr,#___str_11
      004103 75 F0 80         [24] 2357 	mov	b,#0x80
      004106 12 54 D0         [24] 2358 	lcall	_lcd2_writestr
                           0004C3  2359 	C$main.c$690$1$392 ==.
                                   2360 ;	main.c:690: display_setpos(0x0A);
      004109 75 82 0A         [24] 2361 	mov	dpl,#0x0a
      00410C 12 43 A8         [24] 2362 	lcall	_lcd2_setpos
                           0004C9  2363 	C$main.c$691$1$392 ==.
                                   2364 ;	main.c:691: display_writestr("R:");
      00410F 90 5D 37         [24] 2365 	mov	dptr,#___str_12
      004112 75 F0 80         [24] 2366 	mov	b,#0x80
      004115 12 54 D0         [24] 2367 	lcall	_lcd2_writestr
                           0004D2  2368 	C$main.c$693$1$392 ==.
                                   2369 ;	main.c:693: bytes = NUMBYTES;
      004118 75 28 E2         [24] 2370 	mov	_bytes,#0xe2
      00411B 75 29 04         [24] 2371 	mov	(_bytes + 1),#0x04
      00411E E4               [12] 2372 	clr	a
      00411F F5 2A            [12] 2373 	mov	(_bytes + 2),a
      004121 F5 2B            [12] 2374 	mov	(_bytes + 3),a
                           0004DD  2375 	C$main.c$694$1$392 ==.
                                   2376 ;	main.c:694: errors = 0;
      004123 F5 2C            [12] 2377 	mov	_errors,a
      004125 F5 2D            [12] 2378 	mov	(_errors + 1),a
      004127 F5 2E            [12] 2379 	mov	(_errors + 2),a
      004129 F5 2F            [12] 2380 	mov	(_errors + 3),a
                           0004E5  2381 	C$main.c$695$1$392 ==.
                                   2382 ;	main.c:695: errors2 = 0;
      00412B F5 30            [12] 2383 	mov	_errors2,a
      00412D F5 31            [12] 2384 	mov	(_errors2 + 1),a
      00412F F5 32            [12] 2385 	mov	(_errors2 + 2),a
      004131 F5 33            [12] 2386 	mov	(_errors2 + 3),a
                           0004ED  2387 	C$main.c$696$1$392 ==.
                                   2388 ;	main.c:696: acquire_agc = 1;
      004133 75 34 01         [24] 2389 	mov	_acquire_agc,#0x01
                           0004F0  2390 	C$main.c$697$1$392 ==.
                           0004F0  2391 	XG$set_receiveber$0$0 ==.
      004136 22               [24] 2392 	ret
                                   2393 ;------------------------------------------------------------
                                   2394 ;Allocation info for local variables in function 'enable_radio_interrupt_in_mcu_pin'
                                   2395 ;------------------------------------------------------------
                           0004F1  2396 	G$enable_radio_interrupt_in_mcu_pin$0$0 ==.
                           0004F1  2397 	C$main.c$699$1$392 ==.
                                   2398 ;	main.c:699: void enable_radio_interrupt_in_mcu_pin(void)
                                   2399 ;	-----------------------------------------
                                   2400 ;	 function enable_radio_interrupt_in_mcu_pin
                                   2401 ;	-----------------------------------------
      004137                       2402 _enable_radio_interrupt_in_mcu_pin:
                           0004F1  2403 	C$main.c$701$1$396 ==.
                                   2404 ;	main.c:701: IE_4 = 1;
      004137 D2 AC            [12] 2405 	setb	_IE_4
                           0004F3  2406 	C$main.c$702$1$396 ==.
                           0004F3  2407 	XG$enable_radio_interrupt_in_mcu_pin$0$0 ==.
      004139 22               [24] 2408 	ret
                                   2409 ;------------------------------------------------------------
                                   2410 ;Allocation info for local variables in function 'disable_radio_interrupt_in_mcu_pin'
                                   2411 ;------------------------------------------------------------
                           0004F4  2412 	G$disable_radio_interrupt_in_mcu_pin$0$0 ==.
                           0004F4  2413 	C$main.c$704$1$396 ==.
                                   2414 ;	main.c:704: void disable_radio_interrupt_in_mcu_pin(void)
                                   2415 ;	-----------------------------------------
                                   2416 ;	 function disable_radio_interrupt_in_mcu_pin
                                   2417 ;	-----------------------------------------
      00413A                       2418 _disable_radio_interrupt_in_mcu_pin:
                           0004F4  2419 	C$main.c$706$1$398 ==.
                                   2420 ;	main.c:706: IE_4 = 0;
      00413A C2 AC            [12] 2421 	clr	_IE_4
                           0004F6  2422 	C$main.c$707$1$398 ==.
                           0004F6  2423 	XG$disable_radio_interrupt_in_mcu_pin$0$0 ==.
      00413C 22               [24] 2424 	ret
                                   2425 ;------------------------------------------------------------
                                   2426 ;Allocation info for local variables in function '_sdcc_external_startup'
                                   2427 ;------------------------------------------------------------
                                   2428 ;c                         Allocated to registers 
                                   2429 ;p                         Allocated to registers 
                                   2430 ;c                         Allocated to registers 
                                   2431 ;p                         Allocated to registers 
                                   2432 ;------------------------------------------------------------
                           0004F7  2433 	G$_sdcc_external_startup$0$0 ==.
                           0004F7  2434 	C$main.c$710$1$398 ==.
                                   2435 ;	main.c:710: uint8_t _sdcc_external_startup(void)
                                   2436 ;	-----------------------------------------
                                   2437 ;	 function _sdcc_external_startup
                                   2438 ;	-----------------------------------------
      00413D                       2439 __sdcc_external_startup:
                           0004F7  2440 	C$main.c$712$2$401 ==.
                                   2441 ;	main.c:712: wtimer0_setclksrc(WTIMER0_CLKSRC, WTIMER0_PRESCALER);
      00413D 75 82 09         [24] 2442 	mov	dpl,#0x09
      004140 12 48 73         [24] 2443 	lcall	_wtimer0_setconfig
                           0004FD  2444 	C$main.c$713$2$402 ==.
                                   2445 ;	main.c:713: wtimer1_setclksrc(CLKSRC_FRCOSC, 7);
      004143 75 82 38         [24] 2446 	mov	dpl,#0x38
      004146 12 48 C0         [24] 2447 	lcall	_wtimer1_setconfig
                           000503  2448 	C$main.c$715$1$400 ==.
                                   2449 ;	main.c:715: coldstart = !(PCON & 0x40);
      004149 E5 87            [12] 2450 	mov	a,_PCON
      00414B A2 E6            [12] 2451 	mov	c,acc[6]
      00414D B3               [12] 2452 	cpl	c
      00414E 92 01            [24] 2453 	mov	__sdcc_external_startup_sloc0_1_0,c
      004150 E4               [12] 2454 	clr	a
      004151 33               [12] 2455 	rlc	a
      004152 F5 22            [12] 2456 	mov	_coldstart,a
                           00050E  2457 	C$main.c$716$1$400 ==.
                                   2458 ;	main.c:716: ANALOGA = 0x18; /* PA[3,4] LPXOSC, other PA are used as digital pins */
      004154 90 70 07         [24] 2459 	mov	dptr,#_ANALOGA
      004157 74 18            [12] 2460 	mov	a,#0x18
      004159 F0               [24] 2461 	movx	@dptr,a
                           000514  2462 	C$main.c$717$1$400 ==.
                                   2463 ;	main.c:717: PORTA = 0xC0 | (PINA & 0x25); 	/* pull-up for PA[6,7] which are not bonded, no pull up for PA[3,4] (LPXOSC). Output 0 in PA[0,1,2,5] to prevent current consumption in all DIP switch states */
      00415A 74 25            [12] 2464 	mov	a,#0x25
      00415C 55 C8            [12] 2465 	anl	a,_PINA
      00415E 44 C0            [12] 2466 	orl	a,#0xc0
      004160 F5 80            [12] 2467 	mov	_PORTA,a
                           00051C  2468 	C$main.c$719$1$400 ==.
                                   2469 ;	main.c:719: PORTB = 0xFE; /*PB[0,1]  (LCD RS, LCD RST) are overwritten by lcd2_portinit(), enable pull-ups for PB[2..7]  (PB[2,3] for buttons, PB[4..7] unused) */
      004162 75 88 FE         [24] 2470 	mov	_PORTB,#0xfe
                           00051F  2471 	C$main.c$720$1$400 ==.
                                   2472 ;	main.c:720: PORTC = 0xF3 | (PINC & 0x08); 	/* set PC0 = 1 (LCD SEL), PC1 = 1 (LCD SCK), PC2 = 0 (LCD MOSI), PC3 =0 (LED), enable pull-ups for PC[4..7] which are not bonded Mind: PORTC[0:1] is set to 0x3 by lcd2_portinit() */
      004165 74 08            [12] 2473 	mov	a,#0x08
      004167 55 F8            [12] 2474 	anl	a,_PINC
      004169 44 F3            [12] 2475 	orl	a,#0xf3
      00416B F5 90            [12] 2476 	mov	_PORTC,a
                           000527  2477 	C$main.c$722$1$400 ==.
                                   2478 ;	main.c:722: PORTR = 0xCB; /* overwritten by ax5044_45_reset, ax5044_45_comminit() */
      00416D 75 8C CB         [24] 2479 	mov	_PORTR,#0xcb
                           00052A  2480 	C$main.c$724$1$400 ==.
                                   2481 ;	main.c:724: DIRA = 0x27; /* output 0 on PA[0,1,2,5] to prevent current consumption in all DIP switch states. Other PA are inputs, PA[3,4] (LPXOSC) must have disabled digital output drivers */
      004170 75 89 27         [24] 2482 	mov	_DIRA,#0x27
                           00052D  2483 	C$main.c$725$1$400 ==.
                                   2484 ;	main.c:725: DIRB = 0x03; /* PB[0,1] are outputs (LCD RS, LCD RST), PB[2..7] are inputs (PB[2,3] for buttons,  PB[4..7]  unused) */
      004173 75 8A 03         [24] 2485 	mov	_DIRB,#0x03
                           000530  2486 	C$main.c$726$1$400 ==.
                                   2487 ;	main.c:726: DIRC = 0x0F; /* PC[0..3] are outputs (LCD SEL, LCD,SCK, LCD MOSI, LED), PC[4..7] are inputs (not bonded). */
      004176 75 8B 0F         [24] 2488 	mov	_DIRC,#0x0f
                           000533  2489 	C$main.c$727$1$400 ==.
                                   2490 ;	main.c:727: DIRR = 0x15; /* overwritten by ax5044_45_reset, ax5044_45_comminit() */
      004179 75 8E 15         [24] 2491 	mov	_DIRR,#0x15
                           000536  2492 	C$main.c$729$1$400 ==.
                                   2493 ;	main.c:729: axradio_setup_pincfg1();
      00417C 12 06 BC         [24] 2494 	lcall	_axradio_setup_pincfg1
                           000539  2495 	C$main.c$730$1$400 ==.
                                   2496 ;	main.c:730: DPS = 0;
      00417F 75 86 00         [24] 2497 	mov	_DPS,#0x00
                           00053C  2498 	C$main.c$731$1$400 ==.
                                   2499 ;	main.c:731: IE = 0x40;
      004182 75 A8 40         [24] 2500 	mov	_IE,#0x40
                           00053F  2501 	C$main.c$732$1$400 ==.
                                   2502 ;	main.c:732: EIE = 0x00;
      004185 75 98 00         [24] 2503 	mov	_EIE,#0x00
                           000542  2504 	C$main.c$733$1$400 ==.
                                   2505 ;	main.c:733: E2IE = 0x00;
      004188 75 A0 00         [24] 2506 	mov	_E2IE,#0x00
                           000545  2507 	C$main.c$734$1$400 ==.
                                   2508 ;	main.c:734: display_portinit();
      00418B 12 51 07         [24] 2509 	lcall	_lcd2_portinit
                           000548  2510 	C$main.c$735$1$400 ==.
                                   2511 ;	main.c:735: GPIOENABLE = 1; /* unfreeze GPIO */
      00418E 90 70 0C         [24] 2512 	mov	dptr,#_GPIOENABLE
      004191 74 01            [12] 2513 	mov	a,#0x01
      004193 F0               [24] 2514 	movx	@dptr,a
                           00054E  2515 	C$main.c$736$1$400 ==.
                                   2516 ;	main.c:736: return !coldstart; /* coldstart -> return 0 -> var initialization; start from sleep -> return 1 -> no var initialization */
      004194 E5 22            [12] 2517 	mov	a,_coldstart
      004196 B4 01 00         [24] 2518 	cjne	a,#0x01,00109$
      004199                       2519 00109$:
      004199 92 01            [24] 2520 	mov  __sdcc_external_startup_sloc0_1_0,c
      00419B E4               [12] 2521 	clr	a
      00419C 33               [12] 2522 	rlc	a
      00419D F5 82            [12] 2523 	mov	dpl,a
                           000559  2524 	C$main.c$737$1$400 ==.
                           000559  2525 	XG$_sdcc_external_startup$0$0 ==.
      00419F 22               [24] 2526 	ret
                                   2527 ;------------------------------------------------------------
                                   2528 ;Allocation info for local variables in function 'si_write_reg'
                                   2529 ;------------------------------------------------------------
                                   2530 ;data                      Allocated with name '_si_write_reg_PARM_2'
                                   2531 ;address                   Allocated to registers r7 
                                   2532 ;i                         Allocated to registers r6 r7 
                                   2533 ;sdata                     Allocated to registers 
                                   2534 ;mask                      Allocated to registers 
                                   2535 ;------------------------------------------------------------
                           00055A  2536 	Fmain$si_write_reg$0$0 ==.
                           00055A  2537 	C$main.c$741$1$400 ==.
                                   2538 ;	main.c:741: static void si_write_reg(uint8_t address, uint32_t data)
                                   2539 ;	-----------------------------------------
                                   2540 ;	 function si_write_reg
                                   2541 ;	-----------------------------------------
      0041A0                       2542 _si_write_reg:
      0041A0 AF 82            [24] 2543 	mov	r7,dpl
                           00055C  2544 	C$main.c$747$1$404 ==.
                                   2545 ;	main.c:747: data = (data << 14) | (address << 10);
      0041A2 AD 39            [24] 2546 	mov	r5,(_si_write_reg_PARM_2 + 1)
      0041A4 E5 3A            [12] 2547 	mov	a,(_si_write_reg_PARM_2 + 2)
      0041A6 54 03            [12] 2548 	anl	a,#0x03
      0041A8 A2 E0            [12] 2549 	mov	c,acc.0
      0041AA CD               [12] 2550 	xch	a,r5
      0041AB 13               [12] 2551 	rrc	a
      0041AC CD               [12] 2552 	xch	a,r5
      0041AD 13               [12] 2553 	rrc	a
      0041AE A2 E0            [12] 2554 	mov	c,acc.0
      0041B0 CD               [12] 2555 	xch	a,r5
      0041B1 13               [12] 2556 	rrc	a
      0041B2 CD               [12] 2557 	xch	a,r5
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
                           000605  2679 	C$main.c$776$1$404 ==.
                           000605  2680 	XFmain$si_write_reg$0$0 ==.
      00424B 22               [24] 2681 	ret
                                   2682 ;------------------------------------------------------------
                                   2683 ;Allocation info for local variables in function 'synth_init'
                                   2684 ;------------------------------------------------------------
                                   2685 ;freq                      Allocated to registers 
                                   2686 ;phase                     Allocated to registers 
                                   2687 ;pllref                    Allocated to registers 
                                   2688 ;ndiv                      Allocated to registers 
                                   2689 ;rdiv                      Allocated to registers 
                                   2690 ;------------------------------------------------------------
                           000606  2691 	Fmain$synth_init$0$0 ==.
                           000606  2692 	C$main.c$780$1$404 ==.
                                   2693 ;	main.c:780: static void synth_init(void)
                                   2694 ;	-----------------------------------------
                                   2695 ;	 function synth_init
                                   2696 ;	-----------------------------------------
      00424C                       2697 _synth_init:
                           000606  2698 	C$main.c$794$3$423 ==.
                                   2699 ;	main.c:794: led2_on(); //palSetLine(LINE_SI_SENB);
      00424C D2 82            [12] 2700 	setb	_PORTA_2
                           000608  2701 	C$main.c$795$3$425 ==.
                                   2702 ;	main.c:795: led3_on(); //palSetLine(LINE_SI_SDATA);
      00424E D2 85            [12] 2703 	setb	_PORTA_5
                           00060A  2704 	C$main.c$796$3$427 ==.
                                   2705 ;	main.c:796: led1_on(); //palSetLine(LINE_SI_SCLK);
      004250 D2 80            [12] 2706 	setb	_PORTA_0
                           00060C  2707 	C$main.c$797$1$421 ==.
                                   2708 ;	main.c:797: si_write_reg(SI41XX_REG_MAIN_CONFIG, 0b000011000000000100);
      004252 75 38 04         [24] 2709 	mov	_si_write_reg_PARM_2,#0x04
      004255 75 39 30         [24] 2710 	mov	(_si_write_reg_PARM_2 + 1),#0x30
      004258 E4               [12] 2711 	clr	a
      004259 F5 3A            [12] 2712 	mov	(_si_write_reg_PARM_2 + 2),a
      00425B F5 3B            [12] 2713 	mov	(_si_write_reg_PARM_2 + 3),a
      00425D 75 82 00         [24] 2714 	mov	dpl,#0x00
      004260 12 41 A0         [24] 2715 	lcall	_si_write_reg
                           00061D  2716 	C$main.c$798$1$421 ==.
                                   2717 ;	main.c:798: si_write_reg(SI41XX_REG_PHASE_GAIN,  0b000000000000000000);
      004263 E4               [12] 2718 	clr	a
      004264 F5 38            [12] 2719 	mov	_si_write_reg_PARM_2,a
      004266 F5 39            [12] 2720 	mov	(_si_write_reg_PARM_2 + 1),a
      004268 F5 3A            [12] 2721 	mov	(_si_write_reg_PARM_2 + 2),a
      00426A F5 3B            [12] 2722 	mov	(_si_write_reg_PARM_2 + 3),a
      00426C 75 82 01         [24] 2723 	mov	dpl,#0x01
      00426F 12 41 A0         [24] 2724 	lcall	_si_write_reg
                           00062C  2725 	C$main.c$799$1$421 ==.
                                   2726 ;	main.c:799: si_write_reg(SI41XX_REG_PWRDOWN,     0b000000000000000000);
      004272 E4               [12] 2727 	clr	a
      004273 F5 38            [12] 2728 	mov	_si_write_reg_PARM_2,a
      004275 F5 39            [12] 2729 	mov	(_si_write_reg_PARM_2 + 1),a
      004277 F5 3A            [12] 2730 	mov	(_si_write_reg_PARM_2 + 2),a
      004279 F5 3B            [12] 2731 	mov	(_si_write_reg_PARM_2 + 3),a
      00427B 75 82 02         [24] 2732 	mov	dpl,#0x02
      00427E 12 41 A0         [24] 2733 	lcall	_si_write_reg
                           00063B  2734 	C$main.c$800$1$421 ==.
                                   2735 ;	main.c:800: si_write_reg(SI41XX_REG_IF_NDIV, ndiv);
      004281 75 38 50         [24] 2736 	mov	_si_write_reg_PARM_2,#0x50
      004284 75 39 06         [24] 2737 	mov	(_si_write_reg_PARM_2 + 1),#0x06
      004287 E4               [12] 2738 	clr	a
      004288 F5 3A            [12] 2739 	mov	(_si_write_reg_PARM_2 + 2),a
      00428A F5 3B            [12] 2740 	mov	(_si_write_reg_PARM_2 + 3),a
      00428C 75 82 05         [24] 2741 	mov	dpl,#0x05
      00428F 12 41 A0         [24] 2742 	lcall	_si_write_reg
                           00064C  2743 	C$main.c$801$1$421 ==.
                                   2744 ;	main.c:801: si_write_reg(SI41XX_REG_IF_RDIV, rdiv);
      004292 75 38 20         [24] 2745 	mov	_si_write_reg_PARM_2,#0x20
      004295 E4               [12] 2746 	clr	a
      004296 F5 39            [12] 2747 	mov	(_si_write_reg_PARM_2 + 1),a
      004298 F5 3A            [12] 2748 	mov	(_si_write_reg_PARM_2 + 2),a
      00429A F5 3B            [12] 2749 	mov	(_si_write_reg_PARM_2 + 3),a
      00429C 75 82 08         [24] 2750 	mov	dpl,#0x08
      00429F 12 41 A0         [24] 2751 	lcall	_si_write_reg
                           00065C  2752 	C$main.c$802$1$421 ==.
                                   2753 ;	main.c:802: si_write_reg(SI41XX_REG_PWRDOWN,     0b000000000000000010);
      0042A2 75 38 02         [24] 2754 	mov	_si_write_reg_PARM_2,#0x02
      0042A5 E4               [12] 2755 	clr	a
      0042A6 F5 39            [12] 2756 	mov	(_si_write_reg_PARM_2 + 1),a
      0042A8 F5 3A            [12] 2757 	mov	(_si_write_reg_PARM_2 + 2),a
      0042AA F5 3B            [12] 2758 	mov	(_si_write_reg_PARM_2 + 3),a
      0042AC 75 82 02         [24] 2759 	mov	dpl,#0x02
      0042AF 12 41 A0         [24] 2760 	lcall	_si_write_reg
                           00066C  2761 	C$main.c$803$3$429 ==.
                                   2762 ;	main.c:803: led2_on(); //palSetLine(LINE_SI_SENB);
      0042B2 D2 82            [12] 2763 	setb	_PORTA_2
                           00066E  2764 	C$main.c$804$3$431 ==.
                                   2765 ;	main.c:804: led3_on(); //palSetLine(LINE_SI_SDATA);
      0042B4 D2 85            [12] 2766 	setb	_PORTA_5
                           000670  2767 	C$main.c$805$3$433 ==.
                                   2768 ;	main.c:805: led1_on(); //palSetLine(LINE_SI_SCLK);
      0042B6 D2 80            [12] 2769 	setb	_PORTA_0
                           000672  2770 	C$main.c$807$1$421 ==.
                           000672  2771 	XFmain$synth_init$0$0 ==.
      0042B8 22               [24] 2772 	ret
                                   2773 ;------------------------------------------------------------
                                   2774 ;Allocation info for local variables in function 'main'
                                   2775 ;------------------------------------------------------------
                                   2776 ;i                         Allocated to registers r6 
                                   2777 ;crit                      Allocated with name '_main_crit_1_435'
                                   2778 ;x                         Allocated to registers r7 
                                   2779 ;flg                       Allocated to registers r7 
                                   2780 ;flg                       Allocated to registers r7 
                                   2781 ;------------------------------------------------------------
                           000673  2782 	G$main$0$0 ==.
                           000673  2783 	C$main.c$810$1$421 ==.
                                   2784 ;	main.c:810: int main(void)
                                   2785 ;	-----------------------------------------
                                   2786 ;	 function main
                                   2787 ;	-----------------------------------------
      0042B9                       2788 _main:
                           000673  2789 	C$main.c$817$1$435 ==.
                                   2790 ;	main.c:817: __endasm;
                           000000  2791 	G$_start__stack$0$0	= __start__stack
                                   2792 	.globl	G$_start__stack$0$0
                           000673  2793 	C$libmftypes.h$368$4$457 ==.
                                   2794 ;	C:/Program Files (x86)/ON Semiconductor/AXSDB/libmf/include/libmftypes.h:368: EA = 1;
      0042B9 D2 AF            [12] 2795 	setb	_EA
                           000675  2796 	C$main.c$822$1$435 ==.
                                   2797 ;	main.c:822: flash_apply_calibration();
      0042BB 12 51 2D         [24] 2798 	lcall	_flash_apply_calibration
                           000678  2799 	C$main.c$823$1$435 ==.
                                   2800 ;	main.c:823: CLKCON = 0x00;
      0042BE 75 C6 00         [24] 2801 	mov	_CLKCON,#0x00
                           00067B  2802 	C$main.c$824$1$435 ==.
                                   2803 ;	main.c:824: wtimer_init();
      0042C1 12 49 6F         [24] 2804 	lcall	_wtimer_init
                           00067E  2805 	C$main.c$826$1$435 ==.
                                   2806 ;	main.c:826: if (coldstart)
      0042C4 E5 22            [12] 2807 	mov	a,_coldstart
      0042C6 70 03            [24] 2808 	jnz	00194$
      0042C8 02 43 4D         [24] 2809 	ljmp	00132$
      0042CB                       2810 00194$:
                           000685  2811 	C$main.c$828$4$438 ==.
                                   2812 ;	main.c:828: led0_off();
      0042CB C2 93            [12] 2813 	clr	_PORTC_3
                           000687  2814 	C$main.c$829$4$440 ==.
                                   2815 ;	main.c:829: led1_off();
      0042CD C2 80            [12] 2816 	clr	_PORTA_0
                           000689  2817 	C$main.c$830$4$442 ==.
                                   2818 ;	main.c:830: led2_off();
      0042CF C2 82            [12] 2819 	clr	_PORTA_2
                           00068B  2820 	C$main.c$831$4$444 ==.
                                   2821 ;	main.c:831: led3_off();
      0042D1 C2 85            [12] 2822 	clr	_PORTA_5
                           00068D  2823 	C$main.c$833$2$436 ==.
                                   2824 ;	main.c:833: display_init();
      0042D3 12 50 A1         [24] 2825 	lcall	_lcd2_init
                           000690  2826 	C$main.c$834$2$436 ==.
                                   2827 ;	main.c:834: display_setpos(0);
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
      005D30 00                    3091 	.db 0x00
                           000082  3092 Fmain$__str_11$0$0 == .
      005D31                       3093 ___str_11:
      005D31 42 45 52 3D 3F        3094 	.ascii "BER=?"
      005D36 00                    3095 	.db 0x00
                           000088  3096 Fmain$__str_12$0$0 == .
      005D37                       3097 ___str_12:
      005D37 52 3A                 3098 	.ascii "R:"
      005D39 00                    3099 	.db 0x00
                           00008B  3100 Fmain$__str_13$0$0 == .
      005D3A                       3101 ___str_13:
      005D3A 52 4E 47 3D           3102 	.ascii "RNG="
      005D3E 00                    3103 	.db 0x00
                           000090  3104 Fmain$__str_14$0$0 == .
      005D3F                       3105 ___str_14:
      005D3F 20 56 43 4F 49 3D     3106 	.ascii " VCOI="
      005D45 00                    3107 	.db 0x00
                                   3108 	.area XINIT   (CODE)
                                   3109 	.area CABS    (ABS,CODE)
