oresat/oresat-c3-rf/AxSem_Profiles/AX_Radio_Board_TX/TESTS/obj/Debug/TESTS/main.rst

                                      1 ;--------------------------------------------------------
                                      2 ; File Created by SDCC : free open source ANSI-C Compiler
                                      3 ; Version 3.6.0 #9615 (MINGW64)
                                      4 ;--------------------------------------------------------
                                      5 	.module main
                                      6 	.optsdcc -mmcs51 --model-small
                                      7 	
                                      8 ;--------------------------------------------------------
                                      9 ; Public variables in this module
                                     10 ;--------------------------------------------------------
                                     11 	.globl _non_fourfsk_tx1010_pattern
                                     12 	.globl _fourfsk_tx1010_pattern
                                     13 	.globl _onepattern
                                     14 	.globl _txpattern
                                     15 	.globl _main
                                     16 	.globl __sdcc_external_startup
                                     17 	.globl _set_receiveber
                                     18 	.globl _set_transmit
                                     19 	.globl _set_cw
                                     20 	.globl _lcd2_display_radio_error
                                     21 	.globl _delay_ms
                                     22 	.globl _axradio_commsleepexit
                                     23 	.globl _axradio_setup_pincfg2
                                     24 	.globl _axradio_setup_pincfg1
                                     25 	.globl _axradio_get_transmitter_pa_type
                                     26 	.globl _axradio_check_fourfsk_modulation
                                     27 	.globl _axradio_agc_thaw
                                     28 	.globl _axradio_agc_freeze
                                     29 	.globl _axradio_conv_freq_tohz
                                     30 	.globl _axradio_transmit
                                     31 	.globl _axradio_get_pllvcoi
                                     32 	.globl _axradio_get_pllrange
                                     33 	.globl _axradio_set_mode
                                     34 	.globl _axradio_cansleep
                                     35 	.globl _axradio_init
                                     36 	.globl _lcd2_writenum32
                                     37 	.globl _lcd2_writehex16
                                     38 	.globl _lcd2_writenum16
                                     39 	.globl _lcd2_writestr
                                     40 	.globl _lcd2_clear
                                     41 	.globl _lcd2_setpos
                                     42 	.globl _lcd2_portinit
                                     43 	.globl _lcd2_init
                                     44 	.globl _lcd2_txidle
                                     45 	.globl _pn15_output
                                     46 	.globl _pn15_advance
                                     47 	.globl _pn9_advance
                                     48 	.globl _wtimer_runcallbacks
                                     49 	.globl _wtimer_idle
                                     50 	.globl _wtimer_init
                                     51 	.globl _wtimer1_setconfig
                                     52 	.globl _wtimer0_setconfig
                                     53 	.globl _flash_apply_calibration
                                     54 	.globl _enter_sleep
                                     55 	.globl _hweight8
                                     56 	.globl _PORTC_7
                                     57 	.globl _PORTC_6
                                     58 	.globl _PORTC_5
                                     59 	.globl _PORTC_4
                                     60 	.globl _PORTC_3
                                     61 	.globl _PORTC_2
                                     62 	.globl _PORTC_1
                                     63 	.globl _PORTC_0
                                     64 	.globl _PORTB_7
                                     65 	.globl _PORTB_6
                                     66 	.globl _PORTB_5
                                     67 	.globl _PORTB_4
                                     68 	.globl _PORTB_3
                                     69 	.globl _PORTB_2
                                     70 	.globl _PORTB_1
                                     71 	.globl _PORTB_0
                                     72 	.globl _PORTA_7
                                     73 	.globl _PORTA_6
                                     74 	.globl _PORTA_5
                                     75 	.globl _PORTA_4
                                     76 	.globl _PORTA_3
                                     77 	.globl _PORTA_2
                                     78 	.globl _PORTA_1
                                     79 	.globl _PORTA_0
                                     80 	.globl _PINC_7
                                     81 	.globl _PINC_6
                                     82 	.globl _PINC_5
                                     83 	.globl _PINC_4
                                     84 	.globl _PINC_3
                                     85 	.globl _PINC_2
                                     86 	.globl _PINC_1
                                     87 	.globl _PINC_0
                                     88 	.globl _PINB_7
                                     89 	.globl _PINB_6
                                     90 	.globl _PINB_5
                                     91 	.globl _PINB_4
                                     92 	.globl _PINB_3
                                     93 	.globl _PINB_2
                                     94 	.globl _PINB_1
                                     95 	.globl _PINB_0
                                     96 	.globl _PINA_7
                                     97 	.globl _PINA_6
                                     98 	.globl _PINA_5
                                     99 	.globl _PINA_4
                                    100 	.globl _PINA_3
                                    101 	.globl _PINA_2
                                    102 	.globl _PINA_1
                                    103 	.globl _PINA_0
                                    104 	.globl _CY
                                    105 	.globl _AC
                                    106 	.globl _F0
                                    107 	.globl _RS1
                                    108 	.globl _RS0
                                    109 	.globl _OV
                                    110 	.globl _F1
                                    111 	.globl _P
                                    112 	.globl _IP_7
                                    113 	.globl _IP_6
                                    114 	.globl _IP_5
                                    115 	.globl _IP_4
                                    116 	.globl _IP_3
                                    117 	.globl _IP_2
                                    118 	.globl _IP_1
                                    119 	.globl _IP_0
                                    120 	.globl _EA
                                    121 	.globl _IE_7
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
                                    198 	.globl _WTCFGB
                                    199 	.globl _WTCFGA
                                    200 	.globl _WDTRESET
                                    201 	.globl _WDTCFG
                                    202 	.globl _U1STATUS
                                    203 	.globl _U1SHREG
                                    204 	.globl _U1MODE
                                    205 	.globl _U1CTRL
                                    206 	.globl _U0STATUS
                                    207 	.globl _U0SHREG
                                    208 	.globl _U0MODE
                                    209 	.globl _U0CTRL
                                    210 	.globl _T2STATUS
                                    211 	.globl _T2PERIOD
                                    212 	.globl _T2PERIOD1
                                    213 	.globl _T2PERIOD0
                                    214 	.globl _T2MODE
                                    215 	.globl _T2CNT
                                    216 	.globl _T2CNT1
                                    217 	.globl _T2CNT0
                                    218 	.globl _T2CLKSRC
                                    219 	.globl _T1STATUS
                                    220 	.globl _T1PERIOD
                                    221 	.globl _T1PERIOD1
                                    222 	.globl _T1PERIOD0
                                    223 	.globl _T1MODE
                                    224 	.globl _T1CNT
                                    225 	.globl _T1CNT1
                                    226 	.globl _T1CNT0
                                    227 	.globl _T1CLKSRC
                                    228 	.globl _T0STATUS
                                    229 	.globl _T0PERIOD
                                    230 	.globl _T0PERIOD1
                                    231 	.globl _T0PERIOD0
                                    232 	.globl _T0MODE
                                    233 	.globl _T0CNT
                                    234 	.globl _T0CNT1
                                    235 	.globl _T0CNT0
                                    236 	.globl _T0CLKSRC
                                    237 	.globl _SPSTATUS
                                    238 	.globl _SPSHREG
                                    239 	.globl _SPMODE
                                    240 	.globl _SPCLKSRC
                                    241 	.globl _RADIOSTAT
                                    242 	.globl _RADIOSTAT1
                                    243 	.globl _RADIOSTAT0
                                    244 	.globl _RADIODATA
                                    245 	.globl _RADIODATA3
                                    246 	.globl _RADIODATA2
                                    247 	.globl _RADIODATA1
                                    248 	.globl _RADIODATA0
                                    249 	.globl _RADIOADDR
                                    250 	.globl _RADIOADDR1
                                    251 	.globl _RADIOADDR0
                                    252 	.globl _RADIOACC
                                    253 	.globl _OC1STATUS
                                    254 	.globl _OC1PIN
                                    255 	.globl _OC1MODE
                                    256 	.globl _OC1COMP
                                    257 	.globl _OC1COMP1
                                    258 	.globl _OC1COMP0
                                    259 	.globl _OC0STATUS
                                    260 	.globl _OC0PIN
                                    261 	.globl _OC0MODE
                                    262 	.globl _OC0COMP
                                    263 	.globl _OC0COMP1
                                    264 	.globl _OC0COMP0
                                    265 	.globl _NVSTATUS
                                    266 	.globl _NVKEY
                                    267 	.globl _NVDATA
                                    268 	.globl _NVDATA1
                                    269 	.globl _NVDATA0
                                    270 	.globl _NVADDR
                                    271 	.globl _NVADDR1
                                    272 	.globl _NVADDR0
                                    273 	.globl _IC1STATUS
                                    274 	.globl _IC1MODE
                                    275 	.globl _IC1CAPT
                                    276 	.globl _IC1CAPT1
                                    277 	.globl _IC1CAPT0
                                    278 	.globl _IC0STATUS
                                    279 	.globl _IC0MODE
                                    280 	.globl _IC0CAPT
                                    281 	.globl _IC0CAPT1
                                    282 	.globl _IC0CAPT0
                                    283 	.globl _PORTR
                                    284 	.globl _PORTC
                                    285 	.globl _PORTB
                                    286 	.globl _PORTA
                                    287 	.globl _PINR
                                    288 	.globl _PINC
                                    289 	.globl _PINB
                                    290 	.globl _PINA
                                    291 	.globl _DIRR
                                    292 	.globl _DIRC
                                    293 	.globl _DIRB
                                    294 	.globl _DIRA
                                    295 	.globl _DBGLNKSTAT
                                    296 	.globl _DBGLNKBUF
                                    297 	.globl _CODECONFIG
                                    298 	.globl _CLKSTAT
                                    299 	.globl _CLKCON
                                    300 	.globl _ANALOGCOMP
                                    301 	.globl _ADCCONV
                                    302 	.globl _ADCCLKSRC
                                    303 	.globl _ADCCH3CONFIG
                                    304 	.globl _ADCCH2CONFIG
                                    305 	.globl _ADCCH1CONFIG
                                    306 	.globl _ADCCH0CONFIG
                                    307 	.globl __XPAGE
                                    308 	.globl _XPAGE
                                    309 	.globl _SP
                                    310 	.globl _PSW
                                    311 	.globl _PCON
                                    312 	.globl _IP
                                    313 	.globl _IE
                                    314 	.globl _EIP
                                    315 	.globl _EIE
                                    316 	.globl _E2IP
                                    317 	.globl _E2IE
                                    318 	.globl _DPS
                                    319 	.globl _DPTR1
                                    320 	.globl _DPTR0
                                    321 	.globl _DPL1
                                    322 	.globl _DPL
                                    323 	.globl _DPH1
                                    324 	.globl _DPH
                                    325 	.globl _B
                                    326 	.globl _ACC
                                    327 	.globl _txdata
                                    328 	.globl _XTALREADY
                                    329 	.globl _XTALOSC
                                    330 	.globl _XTALAMPL
                                    331 	.globl _SILICONREV
                                    332 	.globl _SCRATCH3
                                    333 	.globl _SCRATCH2
                                    334 	.globl _SCRATCH1
                                    335 	.globl _SCRATCH0
                                    336 	.globl _RADIOMUX
                                    337 	.globl _RADIOFSTATADDR
                                    338 	.globl _RADIOFSTATADDR1
                                    339 	.globl _RADIOFSTATADDR0
                                    340 	.globl _RADIOFDATAADDR
                                    341 	.globl _RADIOFDATAADDR1
                                    342 	.globl _RADIOFDATAADDR0
                                    343 	.globl _OSCRUN
                                    344 	.globl _OSCREADY
                                    345 	.globl _OSCFORCERUN
                                    346 	.globl _OSCCALIB
                                    347 	.globl _MISCCTRL
                                    348 	.globl _LPXOSCGM
                                    349 	.globl _LPOSCREF
                                    350 	.globl _LPOSCREF1
                                    351 	.globl _LPOSCREF0
                                    352 	.globl _LPOSCPER
                                    353 	.globl _LPOSCPER1
                                    354 	.globl _LPOSCPER0
                                    355 	.globl _LPOSCKFILT
                                    356 	.globl _LPOSCKFILT1
                                    357 	.globl _LPOSCKFILT0
                                    358 	.globl _LPOSCFREQ
                                    359 	.globl _LPOSCFREQ1
                                    360 	.globl _LPOSCFREQ0
                                    361 	.globl _LPOSCCONFIG
                                    362 	.globl _PINSEL
                                    363 	.globl _PINCHGC
                                    364 	.globl _PINCHGB
                                    365 	.globl _PINCHGA
                                    366 	.globl _PALTRADIO
                                    367 	.globl _PALTC
                                    368 	.globl _PALTB
                                    369 	.globl _PALTA
                                    370 	.globl _INTCHGC
                                    371 	.globl _INTCHGB
                                    372 	.globl _INTCHGA
                                    373 	.globl _EXTIRQ
                                    374 	.globl _GPIOENABLE
                                    375 	.globl _ANALOGA
                                    376 	.globl _FRCOSCREF
                                    377 	.globl _FRCOSCREF1
                                    378 	.globl _FRCOSCREF0
                                    379 	.globl _FRCOSCPER
                                    380 	.globl _FRCOSCPER1
                                    381 	.globl _FRCOSCPER0
                                    382 	.globl _FRCOSCKFILT
                                    383 	.globl _FRCOSCKFILT1
                                    384 	.globl _FRCOSCKFILT0
                                    385 	.globl _FRCOSCFREQ
                                    386 	.globl _FRCOSCFREQ1
                                    387 	.globl _FRCOSCFREQ0
                                    388 	.globl _FRCOSCCTRL
                                    389 	.globl _FRCOSCCONFIG
                                    390 	.globl _DMA1CONFIG
                                    391 	.globl _DMA1ADDR
                                    392 	.globl _DMA1ADDR1
                                    393 	.globl _DMA1ADDR0
                                    394 	.globl _DMA0CONFIG
                                    395 	.globl _DMA0ADDR
                                    396 	.globl _DMA0ADDR1
                                    397 	.globl _DMA0ADDR0
                                    398 	.globl _ADCTUNE2
                                    399 	.globl _ADCTUNE1
                                    400 	.globl _ADCTUNE0
                                    401 	.globl _ADCCH3VAL
                                    402 	.globl _ADCCH3VAL1
                                    403 	.globl _ADCCH3VAL0
                                    404 	.globl _ADCCH2VAL
                                    405 	.globl _ADCCH2VAL1
                                    406 	.globl _ADCCH2VAL0
                                    407 	.globl _ADCCH1VAL
                                    408 	.globl _ADCCH1VAL1
                                    409 	.globl _ADCCH1VAL0
                                    410 	.globl _ADCCH0VAL
                                    411 	.globl _ADCCH0VAL1
                                    412 	.globl _ADCCH0VAL0
                                    413 	.globl _acquire_agc
                                    414 	.globl _errors2
                                    415 	.globl _errors
                                    416 	.globl _bytes
                                    417 	.globl _scr
                                    418 	.globl _BER_TEST
                                    419 	.globl _coldstart
                                    420 	.globl _axradio_statuschange
                                    421 	.globl _enable_radio_interrupt_in_mcu_pin
                                    422 	.globl _disable_radio_interrupt_in_mcu_pin
                                    423 ;--------------------------------------------------------
                                    424 ; special function registers
                                    425 ;--------------------------------------------------------
                                    426 	.area RSEG    (ABS,DATA)
      000000                        427 	.org 0x0000
                           0000E0   428 G$ACC$0$0 == 0x00e0
                           0000E0   429 _ACC	=	0x00e0
                           0000F0   430 G$B$0$0 == 0x00f0
                           0000F0   431 _B	=	0x00f0
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
      000028                        994 _bytes::
      000028                        995 	.ds 4
                           00000A   996 G$errors$0$0==.
      00002C                        997 _errors::
      00002C                        998 	.ds 4
                           00000E   999 G$errors2$0$0==.
      000030                       1000 _errors2::
      000030                       1001 	.ds 4
                           000012  1002 G$acquire_agc$0$0==.
      000034                       1003 _acquire_agc::
      000034                       1004 	.ds 1
                           000013  1005 Lmain.process_ber$databyte$6$349==.
      000035                       1006 _process_ber_databyte_6_349:
      000035                       1007 	.ds 1
                           000014  1008 Lmain.process_ber$sloc0$1$0==.
      000036                       1009 _process_ber_sloc0_1_0:
      000036                       1010 	.ds 1
                           000015  1011 Lmain.process_ber$sloc1$1$0==.
      000037                       1012 _process_ber_sloc1_1_0:
      000037                       1013 	.ds 2
                           000017  1014 Lmain.si_write_reg$data$1$403==.
      000039                       1015 _si_write_reg_PARM_2:
      000039                       1016 	.ds 4
                                   1017 ;--------------------------------------------------------
                                   1018 ; overlayable items in internal ram 
                                   1019 ;--------------------------------------------------------
                                   1020 	.area	OSEG    (OVR,DATA)
                                   1021 	.area	OSEG    (OVR,DATA)
                                   1022 ;--------------------------------------------------------
                                   1023 ; Stack segment in internal ram 
                                   1024 ;--------------------------------------------------------
                                   1025 	.area	SSEG
      000051                       1026 __start__stack:
      000051                       1027 	.ds	1
                                   1028 
                                   1029 ;--------------------------------------------------------
                                   1030 ; indirectly addressable internal ram data
                                   1031 ;--------------------------------------------------------
                                   1032 	.area ISEG    (DATA)
                                   1033 ;--------------------------------------------------------
                                   1034 ; absolute internal ram data
                                   1035 ;--------------------------------------------------------
                                   1036 	.area IABS    (ABS,DATA)
                                   1037 	.area IABS    (ABS,DATA)
                                   1038 ;--------------------------------------------------------
                                   1039 ; bit data
                                   1040 ;--------------------------------------------------------
                                   1041 	.area BSEG    (BIT)
                           000000  1042 Lmain._sdcc_external_startup$sloc0$1$0==.
      000001                       1043 __sdcc_external_startup_sloc0_1_0:
      000001                       1044 	.ds 1
                                   1045 ;--------------------------------------------------------
                                   1046 ; paged external ram data
                                   1047 ;--------------------------------------------------------
                                   1048 	.area PSEG    (PAG,XDATA)
                                   1049 ;--------------------------------------------------------
                                   1050 ; external ram data
                                   1051 ;--------------------------------------------------------
                                   1052 	.area XSEG    (XDATA)
                           007020  1053 G$ADCCH0VAL0$0$0 == 0x7020
                           007020  1054 _ADCCH0VAL0	=	0x7020
                           007021  1055 G$ADCCH0VAL1$0$0 == 0x7021
                           007021  1056 _ADCCH0VAL1	=	0x7021
                           007020  1057 G$ADCCH0VAL$0$0 == 0x7020
                           007020  1058 _ADCCH0VAL	=	0x7020
                           007022  1059 G$ADCCH1VAL0$0$0 == 0x7022
                           007022  1060 _ADCCH1VAL0	=	0x7022
                           007023  1061 G$ADCCH1VAL1$0$0 == 0x7023
                           007023  1062 _ADCCH1VAL1	=	0x7023
                           007022  1063 G$ADCCH1VAL$0$0 == 0x7022
                           007022  1064 _ADCCH1VAL	=	0x7022
                           007024  1065 G$ADCCH2VAL0$0$0 == 0x7024
                           007024  1066 _ADCCH2VAL0	=	0x7024
                           007025  1067 G$ADCCH2VAL1$0$0 == 0x7025
                           007025  1068 _ADCCH2VAL1	=	0x7025
                           007024  1069 G$ADCCH2VAL$0$0 == 0x7024
                           007024  1070 _ADCCH2VAL	=	0x7024
                           007026  1071 G$ADCCH3VAL0$0$0 == 0x7026
                           007026  1072 _ADCCH3VAL0	=	0x7026
                           007027  1073 G$ADCCH3VAL1$0$0 == 0x7027
                           007027  1074 _ADCCH3VAL1	=	0x7027
                           007026  1075 G$ADCCH3VAL$0$0 == 0x7026
                           007026  1076 _ADCCH3VAL	=	0x7026
                           007028  1077 G$ADCTUNE0$0$0 == 0x7028
                           007028  1078 _ADCTUNE0	=	0x7028
                           007029  1079 G$ADCTUNE1$0$0 == 0x7029
                           007029  1080 _ADCTUNE1	=	0x7029
                           00702A  1081 G$ADCTUNE2$0$0 == 0x702a
                           00702A  1082 _ADCTUNE2	=	0x702a
                           007010  1083 G$DMA0ADDR0$0$0 == 0x7010
                           007010  1084 _DMA0ADDR0	=	0x7010
                           007011  1085 G$DMA0ADDR1$0$0 == 0x7011
                           007011  1086 _DMA0ADDR1	=	0x7011
                           007010  1087 G$DMA0ADDR$0$0 == 0x7010
                           007010  1088 _DMA0ADDR	=	0x7010
                           007014  1089 G$DMA0CONFIG$0$0 == 0x7014
                           007014  1090 _DMA0CONFIG	=	0x7014
                           007012  1091 G$DMA1ADDR0$0$0 == 0x7012
                           007012  1092 _DMA1ADDR0	=	0x7012
                           007013  1093 G$DMA1ADDR1$0$0 == 0x7013
                           007013  1094 _DMA1ADDR1	=	0x7013
                           007012  1095 G$DMA1ADDR$0$0 == 0x7012
                           007012  1096 _DMA1ADDR	=	0x7012
                           007015  1097 G$DMA1CONFIG$0$0 == 0x7015
                           007015  1098 _DMA1CONFIG	=	0x7015
                           007070  1099 G$FRCOSCCONFIG$0$0 == 0x7070
                           007070  1100 _FRCOSCCONFIG	=	0x7070
                           007071  1101 G$FRCOSCCTRL$0$0 == 0x7071
                           007071  1102 _FRCOSCCTRL	=	0x7071
                           007076  1103 G$FRCOSCFREQ0$0$0 == 0x7076
                           007076  1104 _FRCOSCFREQ0	=	0x7076
                           007077  1105 G$FRCOSCFREQ1$0$0 == 0x7077
                           007077  1106 _FRCOSCFREQ1	=	0x7077
                           007076  1107 G$FRCOSCFREQ$0$0 == 0x7076
                           007076  1108 _FRCOSCFREQ	=	0x7076
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
                           00FC06  1223 Fmain$flash_deviceid$0$0 == 0xfc06
                           00FC06  1224 _flash_deviceid	=	0xfc06
                           00FC00  1225 Fmain$flash_calsector$0$0 == 0xfc00
                           00FC00  1226 _flash_calsector	=	0xfc00
                           000000  1227 G$txdata$0$0==.
      00029E                       1228 _txdata::
      00029E                       1229 	.ds 8
                                   1230 ;--------------------------------------------------------
                                   1231 ; absolute external ram data
                                   1232 ;--------------------------------------------------------
                                   1233 	.area XABS    (ABS,XDATA)
                                   1234 ;--------------------------------------------------------
                                   1235 ; external initialized ram data
                                   1236 ;--------------------------------------------------------
                                   1237 	.area XISEG   (XDATA)
                                   1238 	.area HOME    (CODE)
                                   1239 	.area GSINIT0 (CODE)
                                   1240 	.area GSINIT1 (CODE)
                                   1241 	.area GSINIT2 (CODE)
                                   1242 	.area GSINIT3 (CODE)
                                   1243 	.area GSINIT4 (CODE)
                                   1244 	.area GSINIT5 (CODE)
                                   1245 	.area GSINIT  (CODE)
                                   1246 	.area GSFINAL (CODE)
                                   1247 	.area CSEG    (CODE)
                                   1248 ;--------------------------------------------------------
                                   1249 ; interrupt vector 
                                   1250 ;--------------------------------------------------------
                                   1251 	.area HOME    (CODE)
      000000                       1252 __interrupt_vect:
      000000 02 03 11         [24] 1253 	ljmp	__sdcc_gsinit_startup
      000003 32               [24] 1254 	reti
      000004                       1255 	.ds	7
      00000B 02 00 B1         [24] 1256 	ljmp	_wtimer_irq
      00000E                       1257 	.ds	5
      000013 32               [24] 1258 	reti
      000014                       1259 	.ds	7
      00001B 32               [24] 1260 	reti
      00001C                       1261 	.ds	7
      000023 02 11 B2         [24] 1262 	ljmp	_axradio_isr
      000026                       1263 	.ds	5
      00002B 32               [24] 1264 	reti
      00002C                       1265 	.ds	7
      000033 02 3C 39         [24] 1266 	ljmp	_pwrmgmt_irq
      000036                       1267 	.ds	5
      00003B 32               [24] 1268 	reti
      00003C                       1269 	.ds	7
      000043 32               [24] 1270 	reti
      000044                       1271 	.ds	7
      00004B 32               [24] 1272 	reti
      00004C                       1273 	.ds	7
      000053 02 4D DE         [24] 1274 	ljmp	_lcd2_irq
      000056                       1275 	.ds	5
      00005B 02 02 A3         [24] 1276 	ljmp	_uart0_irq
      00005E                       1277 	.ds	5
      000063 02 02 DA         [24] 1278 	ljmp	_uart1_irq
      000066                       1279 	.ds	5
      00006B 32               [24] 1280 	reti
      00006C                       1281 	.ds	7
      000073 32               [24] 1282 	reti
      000074                       1283 	.ds	7
      00007B 32               [24] 1284 	reti
      00007C                       1285 	.ds	7
      000083 32               [24] 1286 	reti
      000084                       1287 	.ds	7
      00008B 32               [24] 1288 	reti
      00008C                       1289 	.ds	7
      000093 32               [24] 1290 	reti
      000094                       1291 	.ds	7
      00009B 32               [24] 1292 	reti
      00009C                       1293 	.ds	7
      0000A3 32               [24] 1294 	reti
      0000A4                       1295 	.ds	7
      0000AB 02 02 6C         [24] 1296 	ljmp	_dbglink_irq
                                   1297 ;--------------------------------------------------------
                                   1298 ; global & static initialisations
                                   1299 ;--------------------------------------------------------
                                   1300 	.area HOME    (CODE)
                                   1301 	.area GSINIT  (CODE)
                                   1302 	.area GSFINAL (CODE)
                                   1303 	.area GSINIT  (CODE)
                                   1304 	.globl __sdcc_gsinit_startup
                                   1305 	.globl __sdcc_program_startup
                                   1306 	.globl __start__stack
                                   1307 	.globl __mcs51_genXINIT
                                   1308 	.globl __mcs51_genXRAMCLEAR
                                   1309 	.globl __mcs51_genRAMCLEAR
                           000000  1310 	C$main.c$66$1$435 ==.
                                   1311 ;	main.c:66: uint8_t __data coldstart = 1; /* caution: initialization with 1 is necessary! Variables are initialized upon _sdcc_external_startup returning 0 -> the coldstart value returned from _sdcc_external startup does not survive in the coldstart case */
      00038A 75 22 01         [24] 1312 	mov	_coldstart,#0x01
                                   1313 	.area GSFINAL (CODE)
      00038D 02 00 AE         [24] 1314 	ljmp	__sdcc_program_startup
                                   1315 ;--------------------------------------------------------
                                   1316 ; Home
                                   1317 ;--------------------------------------------------------
                                   1318 	.area HOME    (CODE)
                                   1319 	.area HOME    (CODE)
      0000AE                       1320 __sdcc_program_startup:
      0000AE 02 41 C8         [24] 1321 	ljmp	_main
                                   1322 ;	return from main will return to caller
                                   1323 ;--------------------------------------------------------
                                   1324 ; code
                                   1325 ;--------------------------------------------------------
                                   1326 	.area CSEG    (CODE)
                                   1327 ;------------------------------------------------------------
                                   1328 ;Allocation info for local variables in function 'pwrmgmt_irq'
                                   1329 ;------------------------------------------------------------
                                   1330 ;pc                        Allocated to registers r7 
                                   1331 ;------------------------------------------------------------
                           000000  1332 	Fmain$pwrmgmt_irq$0$0 ==.
                           000000  1333 	C$main.c$159$0$0 ==.
                                   1334 ;	main.c:159: static void pwrmgmt_irq(void) __interrupt(INT_POWERMGMT)
                                   1335 ;	-----------------------------------------
                                   1336 ;	 function pwrmgmt_irq
                                   1337 ;	-----------------------------------------
      003C39                       1338 _pwrmgmt_irq:
                           000007  1339 	ar7 = 0x07
                           000006  1340 	ar6 = 0x06
                           000005  1341 	ar5 = 0x05
                           000004  1342 	ar4 = 0x04
                           000003  1343 	ar3 = 0x03
                           000002  1344 	ar2 = 0x02
                           000001  1345 	ar1 = 0x01
                           000000  1346 	ar0 = 0x00
      003C39 C0 E0            [24] 1347 	push	acc
      003C3B C0 82            [24] 1348 	push	dpl
      003C3D C0 83            [24] 1349 	push	dph
      003C3F C0 07            [24] 1350 	push	ar7
      003C41 C0 D0            [24] 1351 	push	psw
      003C43 75 D0 00         [24] 1352 	mov	psw,#0x00
                           00000D  1353 	C$main.c$161$1$0 ==.
                                   1354 ;	main.c:161: uint8_t pc = PCON;
                           00000D  1355 	C$main.c$163$1$337 ==.
                                   1356 ;	main.c:163: if (!(pc & 0x80))
      003C46 E5 87            [12] 1357 	mov	a,_PCON
      003C48 FF               [12] 1358 	mov	r7,a
      003C49 20 E7 02         [24] 1359 	jb	acc.7,00102$
                           000013  1360 	C$main.c$164$1$337 ==.
                                   1361 ;	main.c:164: return;
      003C4C 80 10            [24] 1362 	sjmp	00106$
      003C4E                       1363 00102$:
                           000015  1364 	C$main.c$166$1$337 ==.
                                   1365 ;	main.c:166: GPIOENABLE = 0;
      003C4E 90 70 0C         [24] 1366 	mov	dptr,#_GPIOENABLE
      003C51 E4               [12] 1367 	clr	a
      003C52 F0               [24] 1368 	movx	@dptr,a
                           00001A  1369 	C$main.c$167$1$337 ==.
                                   1370 ;	main.c:167: IE = EIE = E2IE = 0;
                                   1371 ;	1-genFromRTrack replaced	mov	_E2IE,#0x00
      003C53 F5 A0            [12] 1372 	mov	_E2IE,a
                                   1373 ;	1-genFromRTrack replaced	mov	_EIE,#0x00
      003C55 F5 98            [12] 1374 	mov	_EIE,a
                                   1375 ;	1-genFromRTrack replaced	mov	_IE,#0x00
      003C57 F5 A8            [12] 1376 	mov	_IE,a
      003C59                       1377 00104$:
                           000020  1378 	C$main.c$170$1$337 ==.
                                   1379 ;	main.c:170: PCON |= 0x01;
      003C59 43 87 01         [24] 1380 	orl	_PCON,#0x01
      003C5C 80 FB            [24] 1381 	sjmp	00104$
      003C5E                       1382 00106$:
      003C5E D0 D0            [24] 1383 	pop	psw
      003C60 D0 07            [24] 1384 	pop	ar7
      003C62 D0 83            [24] 1385 	pop	dph
      003C64 D0 82            [24] 1386 	pop	dpl
      003C66 D0 E0            [24] 1387 	pop	acc
                           00002F  1388 	C$main.c$171$1$337 ==.
                           00002F  1389 	XFmain$pwrmgmt_irq$0$0 ==.
      003C68 32               [24] 1390 	reti
                                   1391 ;	eliminated unneeded push/pop b
                                   1392 ;------------------------------------------------------------
                                   1393 ;Allocation info for local variables in function 'correct_ber'
                                   1394 ;------------------------------------------------------------
                                   1395 ;x                         Allocated to registers 
                                   1396 ;------------------------------------------------------------
                           000030  1397 	Fmain$correct_ber$0$0 ==.
                           000030  1398 	C$main.c$174$1$337 ==.
                                   1399 ;	main.c:174: static void correct_ber(void)
                                   1400 ;	-----------------------------------------
                                   1401 ;	 function correct_ber
                                   1402 ;	-----------------------------------------
      003C69                       1403 _correct_ber:
                           000030  1404 	C$main.c$193$1$339 ==.
                                   1405 ;	main.c:193: }
                           000030  1406 	C$main.c$194$1$339 ==.
                           000030  1407 	XFmain$correct_ber$0$0 ==.
      003C69 22               [24] 1408 	ret
                                   1409 ;------------------------------------------------------------
                                   1410 ;Allocation info for local variables in function 'process_ber'
                                   1411 ;------------------------------------------------------------
                                   1412 ;st                        Allocated to registers r6 r7 
                                   1413 ;fourfsk                   Allocated to registers r5 
                                   1414 ;i                         Allocated to registers r3 
                                   1415 ;p                         Allocated to registers r6 r7 
                                   1416 ;databyte                  Allocated with name '_process_ber_databyte_6_349'
                                   1417 ;databyte                  Allocated to registers r4 
                                   1418 ;databyte                  Allocated to registers 
                                   1419 ;databyte                  Allocated to registers 
                                   1420 ;databyte                  Allocated to registers 
                                   1421 ;sloc0                     Allocated with name '_process_ber_sloc0_1_0'
                                   1422 ;sloc1                     Allocated with name '_process_ber_sloc1_1_0'
                                   1423 ;------------------------------------------------------------
                           000031  1424 	Fmain$process_ber$0$0 ==.
                           000031  1425 	C$main.c$196$1$339 ==.
                                   1426 ;	main.c:196: static void process_ber(struct axradio_status __xdata *st)
                                   1427 ;	-----------------------------------------
                                   1428 ;	 function process_ber
                                   1429 ;	-----------------------------------------
      003C6A                       1430 _process_ber:
      003C6A AE 82            [24] 1431 	mov	r6,dpl
      003C6C AF 83            [24] 1432 	mov	r7,dph
                           000035  1433 	C$main.c$198$1$343 ==.
                                   1434 ;	main.c:198: uint8_t fourfsk = axradio_check_fourfsk_modulation();
      003C6E C0 07            [24] 1435 	push	ar7
      003C70 C0 06            [24] 1436 	push	ar6
      003C72 12 3A 43         [24] 1437 	lcall	_axradio_check_fourfsk_modulation
      003C75 AD 82            [24] 1438 	mov	r5,dpl
      003C77 D0 06            [24] 1439 	pop	ar6
      003C79 D0 07            [24] 1440 	pop	ar7
                           000042  1441 	C$main.c$200$2$344 ==.
                                   1442 ;	main.c:200: uint8_t i = st->u.rx.pktlen;
      003C7B 74 06            [12] 1443 	mov	a,#0x06
      003C7D 2E               [12] 1444 	add	a,r6
      003C7E FE               [12] 1445 	mov	r6,a
      003C7F E4               [12] 1446 	clr	a
      003C80 3F               [12] 1447 	addc	a,r7
      003C81 FF               [12] 1448 	mov	r7,a
      003C82 74 18            [12] 1449 	mov	a,#0x18
      003C84 2E               [12] 1450 	add	a,r6
      003C85 F5 82            [12] 1451 	mov	dpl,a
      003C87 E4               [12] 1452 	clr	a
      003C88 3F               [12] 1453 	addc	a,r7
      003C89 F5 83            [12] 1454 	mov	dph,a
      003C8B E0               [24] 1455 	movx	a,@dptr
      003C8C FB               [12] 1456 	mov	r3,a
      003C8D A3               [24] 1457 	inc	dptr
      003C8E E0               [24] 1458 	movx	a,@dptr
                           000056  1459 	C$main.c$201$2$344 ==.
                                   1460 ;	main.c:201: bytes -= i;
      003C8F 8B 00            [24] 1461 	mov	ar0,r3
      003C91 E4               [12] 1462 	clr	a
      003C92 F9               [12] 1463 	mov	r1,a
      003C93 FA               [12] 1464 	mov	r2,a
      003C94 FC               [12] 1465 	mov	r4,a
      003C95 E5 28            [12] 1466 	mov	a,_bytes
      003C97 C3               [12] 1467 	clr	c
      003C98 98               [12] 1468 	subb	a,r0
      003C99 F5 28            [12] 1469 	mov	_bytes,a
      003C9B E5 29            [12] 1470 	mov	a,(_bytes + 1)
      003C9D 99               [12] 1471 	subb	a,r1
      003C9E F5 29            [12] 1472 	mov	(_bytes + 1),a
      003CA0 E5 2A            [12] 1473 	mov	a,(_bytes + 2)
      003CA2 9A               [12] 1474 	subb	a,r2
      003CA3 F5 2A            [12] 1475 	mov	(_bytes + 2),a
      003CA5 E5 2B            [12] 1476 	mov	a,(_bytes + 3)
      003CA7 9C               [12] 1477 	subb	a,r4
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
                                   1640 ;	main.c:287: }
      003D75                       1641 00126$:
                           00013C  1642 	C$main.c$291$1$343 ==.
                                   1643 ;	main.c:291: if (!acquire_agc)
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
