oresat/oresat-c3-rf/measurements/microstrips/2019-10-19_E5071C-ENA/TDR_THRU.PNG

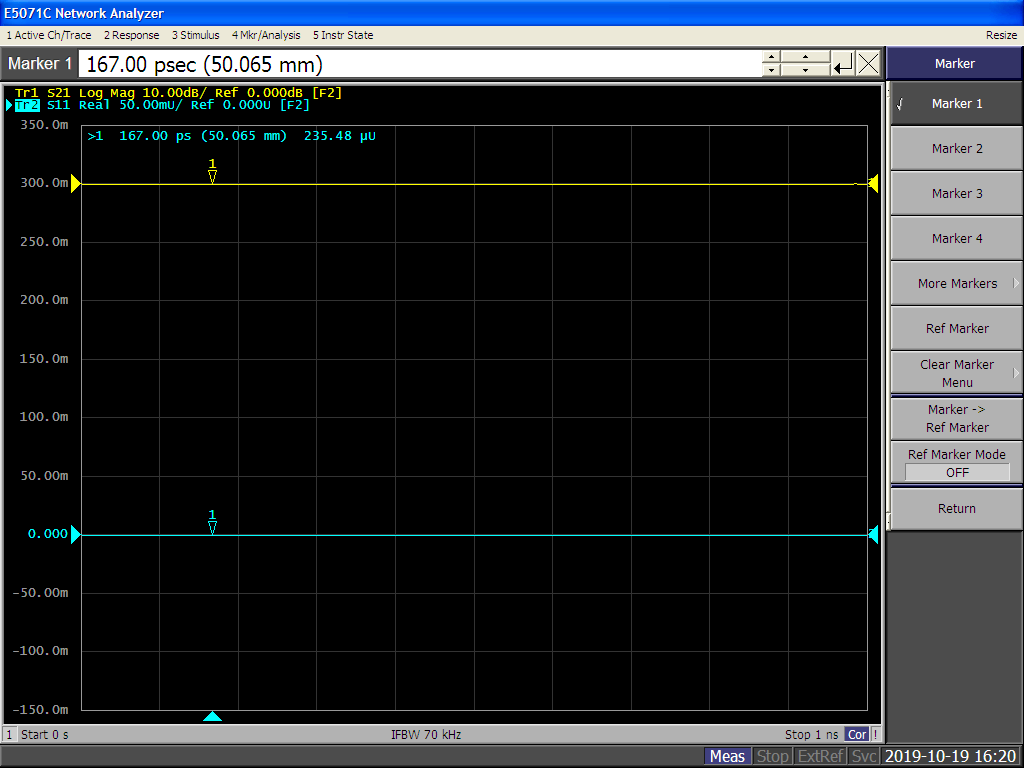
measurements/microstrips/2019-10-19_E5071C-ENA/TDR_THRU.PNG
