oresat/oresat-c3-rf/AxSem_Profiles/AX_C3_L_RX/MASTER/obj/Debug/COMMON/display_com0.rst

                                      1 ;--------------------------------------------------------
                                      2 ; File Created by SDCC : free open source ANSI-C Compiler
                                      3 ; Version 3.6.0 #9615 (MINGW64)
                                      4 ;--------------------------------------------------------
                                      5 	.module display_com0
                                      6 	.optsdcc -mmcs51 --model-small
                                      7 	
                                      8 ;--------------------------------------------------------
                                      9 ; Public variables in this module
                                     10 ;--------------------------------------------------------
                                     11 	.globl _PORTC_7
                                     12 	.globl _PORTC_6
                                     13 	.globl _PORTC_5
                                     14 	.globl _PORTC_4
                                     15 	.globl _PORTC_3
                                     16 	.globl _PORTC_2
                                     17 	.globl _PORTC_1
                                     18 	.globl _PORTC_0
                                     19 	.globl _PORTB_7
                                     20 	.globl _PORTB_6
                                     21 	.globl _PORTB_5
                                     22 	.globl _PORTB_4
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
                                    152 	.globl _WTCNTA0
                                    153 	.globl _WTCFGB
                                    154 	.globl _WTCFGA
                                    155 	.globl _WDTRESET
                                    156 	.globl _WDTCFG
                                    157 	.globl _U1STATUS
                                    158 	.globl _U1SHREG
                                    159 	.globl _U1MODE
                                    160 	.globl _U1CTRL
                                    161 	.globl _U0STATUS
                                    162 	.globl _U0SHREG
                                    163 	.globl _U0MODE
                                    164 	.globl _U0CTRL
                                    165 	.globl _T2STATUS
                                    166 	.globl _T2PERIOD
                                    167 	.globl _T2PERIOD1
                                    168 	.globl _T2PERIOD0
                                    169 	.globl _T2MODE
                                    170 	.globl _T2CNT
                                    171 	.globl _T2CNT1
                                    172 	.globl _T2CNT0
                                    173 	.globl _T2CLKSRC
                                    174 	.globl _T1STATUS
                                    175 	.globl _T1PERIOD
                                    176 	.globl _T1PERIOD1
                                    177 	.globl _T1PERIOD0
                                    178 	.globl _T1MODE
                                    179 	.globl _T1CNT
                                    180 	.globl _T1CNT1
                                    181 	.globl _T1CNT0
                                    182 	.globl _T1CLKSRC
                                    183 	.globl _T0STATUS
                                    184 	.globl _T0PERIOD
                                    185 	.globl _T0PERIOD1
                                    186 	.globl _T0PERIOD0
                                    187 	.globl _T0MODE
                                    188 	.globl _T0CNT
                                    189 	.globl _T0CNT1
                                    190 	.globl _T0CNT0
                                    191 	.globl _T0CLKSRC
                                    192 	.globl _SPSTATUS
                                    193 	.globl _SPSHREG
                                    194 	.globl _SPMODE
                                    195 	.globl _SPCLKSRC
                                    196 	.globl _RADIOSTAT
                                    197 	.globl _RADIOSTAT1
                                    198 	.globl _RADIOSTAT0
                                    199 	.globl _RADIODATA
                                    200 	.globl _RADIODATA3
                                    201 	.globl _RADIODATA2
                                    202 	.globl _RADIODATA1
                                    203 	.globl _RADIODATA0
                                    204 	.globl _RADIOADDR
                                    205 	.globl _RADIOADDR1
                                    206 	.globl _RADIOADDR0
                                    207 	.globl _RADIOACC
                                    208 	.globl _OC1STATUS
                                    209 	.globl _OC1PIN
                                    210 	.globl _OC1MODE
                                    211 	.globl _OC1COMP
                                    212 	.globl _OC1COMP1
                                    213 	.globl _OC1COMP0
                                    214 	.globl _OC0STATUS
                                    215 	.globl _OC0PIN
                                    216 	.globl _OC0MODE
                                    217 	.globl _OC0COMP
                                    218 	.globl _OC0COMP1
                                    219 	.globl _OC0COMP0
                                    220 	.globl _NVSTATUS
                                    221 	.globl _NVKEY
                                    222 	.globl _NVDATA
                                    223 	.globl _NVDATA1
                                    224 	.globl _NVDATA0
                                    225 	.globl _NVADDR
                                    226 	.globl _NVADDR1
                                    227 	.globl _NVADDR0
                                    228 	.globl _IC1STATUS
                                    229 	.globl _IC1MODE
                                    230 	.globl _IC1CAPT
                                    231 	.globl _IC1CAPT1
                                    232 	.globl _IC1CAPT0
                                    233 	.globl _IC0STATUS
                                    234 	.globl _IC0MODE
                                    235 	.globl _IC0CAPT
                                    236 	.globl _IC0CAPT1
                                    237 	.globl _IC0CAPT0
                                    238 	.globl _PORTR
                                    239 	.globl _PORTC
                                    240 	.globl _PORTB
                                    241 	.globl _PORTA
                                    242 	.globl _PINR
                                    243 	.globl _PINC
                                    244 	.globl _PINB
                                    245 	.globl _PINA
                                    246 	.globl _DIRR
                                    247 	.globl _DIRC
                                    248 	.globl _DIRB
                                    249 	.globl _DIRA
                                    250 	.globl _DBGLNKSTAT
                                    251 	.globl _DBGLNKBUF
                                    252 	.globl _CODECONFIG
                                    253 	.globl _CLKSTAT
                                    254 	.globl _CLKCON
                                    255 	.globl _ANALOGCOMP
                                    256 	.globl _ADCCONV
                                    257 	.globl _ADCCLKSRC
                                    258 	.globl _ADCCH3CONFIG
                                    259 	.globl _ADCCH2CONFIG
                                    260 	.globl _ADCCH1CONFIG
                                    261 	.globl _ADCCH0CONFIG
                                    262 	.globl __XPAGE
                                    263 	.globl _XPAGE
                                    264 	.globl _SP
                                    265 	.globl _PSW
                                    266 	.globl _PCON
                                    267 	.globl _IP
                                    268 	.globl _IE
                                    269 	.globl _EIP
                                    270 	.globl _EIE
                                    271 	.globl _E2IP
                                    272 	.globl _E2IE
                                    273 	.globl _DPS
                                    274 	.globl _DPTR1
                                    275 	.globl _DPTR0
                                    276 	.globl _DPL1
                                    277 	.globl _DPL
                                    278 	.globl _DPH1
                                    279 	.globl _DPH
                                    280 	.globl _B
                                    281 	.globl _ACC
                                    282 	.globl _XTALREADY
                                    283 	.globl _XTALOSC
                                    284 	.globl _XTALAMPL
                                    285 	.globl _SILICONREV
                                    286 	.globl _SCRATCH3
                                    287 	.globl _SCRATCH2
                                    288 	.globl _SCRATCH1
                                    289 	.globl _SCRATCH0
                                    290 	.globl _RADIOMUX
                                    291 	.globl _RADIOFSTATADDR
                                    292 	.globl _RADIOFSTATADDR1
                                    293 	.globl _RADIOFSTATADDR0
                                    294 	.globl _RADIOFDATAADDR
                                    295 	.globl _RADIOFDATAADDR1
                                    296 	.globl _RADIOFDATAADDR0
                                    297 	.globl _OSCRUN
                                    298 	.globl _OSCREADY
                                    299 	.globl _OSCFORCERUN
                                    300 	.globl _OSCCALIB
                                    301 	.globl _MISCCTRL
                                    302 	.globl _LPXOSCGM
                                    303 	.globl _LPOSCREF
                                    304 	.globl _LPOSCREF1
                                    305 	.globl _LPOSCREF0
                                    306 	.globl _LPOSCPER
                                    307 	.globl _LPOSCPER1
                                    308 	.globl _LPOSCPER0
                                    309 	.globl _LPOSCKFILT
                                    310 	.globl _LPOSCKFILT1
                                    311 	.globl _LPOSCKFILT0
                                    312 	.globl _LPOSCFREQ
                                    313 	.globl _LPOSCFREQ1
                                    314 	.globl _LPOSCFREQ0
                                    315 	.globl _LPOSCCONFIG
                                    316 	.globl _PINSEL
                                    317 	.globl _PINCHGC
                                    318 	.globl _PINCHGB
                                    319 	.globl _PINCHGA
                                    320 	.globl _PALTRADIO
                                    321 	.globl _PALTC
                                    322 	.globl _PALTB
                                    323 	.globl _PALTA
                                    324 	.globl _INTCHGC
                                    325 	.globl _INTCHGB
                                    326 	.globl _INTCHGA
                                    327 	.globl _EXTIRQ
                                    328 	.globl _GPIOENABLE
                                    329 	.globl _ANALOGA
                                    330 	.globl _FRCOSCREF
                                    331 	.globl _FRCOSCREF1
                                    332 	.globl _FRCOSCREF0
                                    333 	.globl _FRCOSCPER
                                    334 	.globl _FRCOSCPER1
                                    335 	.globl _FRCOSCPER0
                                    336 	.globl _FRCOSCKFILT
                                    337 	.globl _FRCOSCKFILT1
                                    338 	.globl _FRCOSCKFILT0
                                    339 	.globl _FRCOSCFREQ
                                    340 	.globl _FRCOSCFREQ1
                                    341 	.globl _FRCOSCFREQ0
                                    342 	.globl _FRCOSCCTRL
                                    343 	.globl _FRCOSCCONFIG
                                    344 	.globl _DMA1CONFIG
                                    345 	.globl _DMA1ADDR
                                    346 	.globl _DMA1ADDR1
                                    347 	.globl _DMA1ADDR0
                                    348 	.globl _DMA0CONFIG
                                    349 	.globl _DMA0ADDR
                                    350 	.globl _DMA0ADDR1
                                    351 	.globl _DMA0ADDR0
                                    352 	.globl _ADCTUNE2
                                    353 	.globl _ADCTUNE1
                                    354 	.globl _ADCTUNE0
                                    355 	.globl _ADCCH3VAL
                                    356 	.globl _ADCCH3VAL1
                                    357 	.globl _ADCCH3VAL0
                                    358 	.globl _ADCCH2VAL
                                    359 	.globl _ADCCH2VAL1
                                    360 	.globl _ADCCH2VAL0
                                    361 	.globl _ADCCH1VAL
                                    362 	.globl _ADCCH1VAL1
                                    363 	.globl _ADCCH1VAL0
                                    364 	.globl _ADCCH0VAL
                                    365 	.globl _ADCCH0VAL1
                                    366 	.globl _ADCCH0VAL0
                                    367 ;--------------------------------------------------------
                                    368 ; special function registers
                                    369 ;--------------------------------------------------------
                                    370 	.area RSEG    (ABS,DATA)
      000000                        371 	.org 0x0000
                           0000E0   372 G$ACC$0$0 == 0x00e0
                           0000E0   373 _ACC	=	0x00e0
                           0000F0   374 G$B$0$0 == 0x00f0
                           0000F0   375 _B	=	0x00f0
                           000083   376 G$DPH$0$0 == 0x0083
                           000083   377 _DPH	=	0x0083
                           000085   378 G$DPH1$0$0 == 0x0085
                           000085   379 _DPH1	=	0x0085
                           000082   380 G$DPL$0$0 == 0x0082
                           000082   381 _DPL	=	0x0082
                           000084   382 G$DPL1$0$0 == 0x0084
                           000084   383 _DPL1	=	0x0084
                           008382   384 G$DPTR0$0$0 == 0x8382
                           008382   385 _DPTR0	=	0x8382
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
                           00008E   899 G$PORTB_6$0$0 == 0x008e
                           00008E   900 _PORTB_6	=	0x008e
                           00008F   901 G$PORTB_7$0$0 == 0x008f
                           00008F   902 _PORTB_7	=	0x008f
                           000090   903 G$PORTC_0$0$0 == 0x0090
                           000090   904 _PORTC_0	=	0x0090
                           000091   905 G$PORTC_1$0$0 == 0x0091
                           000091   906 _PORTC_1	=	0x0091
                           000092   907 G$PORTC_2$0$0 == 0x0092
                           000092   908 _PORTC_2	=	0x0092
                           000093   909 G$PORTC_3$0$0 == 0x0093
                           000093   910 _PORTC_3	=	0x0093
                           000094   911 G$PORTC_4$0$0 == 0x0094
                           000094   912 _PORTC_4	=	0x0094
                           000095   913 G$PORTC_5$0$0 == 0x0095
                           000095   914 _PORTC_5	=	0x0095
                           000096   915 G$PORTC_6$0$0 == 0x0096
                           000096   916 _PORTC_6	=	0x0096
                           000097   917 G$PORTC_7$0$0 == 0x0097
                           000097   918 _PORTC_7	=	0x0097
                                    919 ;--------------------------------------------------------
                                    920 ; overlayable register banks
                                    921 ;--------------------------------------------------------
                                    922 	.area REG_BANK_0	(REL,OVR,DATA)
      000000                        923 	.ds 8
                                    924 ;--------------------------------------------------------
                                    925 ; internal ram data
                                    926 ;--------------------------------------------------------
                                    927 	.area DSEG    (DATA)
                                    928 ;--------------------------------------------------------
                                    929 ; overlayable items in internal ram 
                                    930 ;--------------------------------------------------------
                                    931 ;--------------------------------------------------------
                                    932 ; indirectly addressable internal ram data
                                    933 ;--------------------------------------------------------
                                    934 	.area ISEG    (DATA)
                                    935 ;--------------------------------------------------------
                                    936 ; absolute internal ram data
                                    937 ;--------------------------------------------------------
                                    938 	.area IABS    (ABS,DATA)
                                    939 	.area IABS    (ABS,DATA)
                                    940 ;--------------------------------------------------------
                                    941 ; bit data
                                    942 ;--------------------------------------------------------
                                    943 	.area BSEG    (BIT)
                                    944 ;--------------------------------------------------------
                                    945 ; paged external ram data
                                    946 ;--------------------------------------------------------
                                    947 	.area PSEG    (PAG,XDATA)
                                    948 ;--------------------------------------------------------
                                    949 ; external ram data
                                    950 ;--------------------------------------------------------
                                    951 	.area XSEG    (XDATA)
                           007020   952 G$ADCCH0VAL0$0$0 == 0x7020
                           007020   953 _ADCCH0VAL0	=	0x7020
                           007021   954 G$ADCCH0VAL1$0$0 == 0x7021
                           007021   955 _ADCCH0VAL1	=	0x7021
                           007020   956 G$ADCCH0VAL$0$0 == 0x7020
                           007020   957 _ADCCH0VAL	=	0x7020
                           007022   958 G$ADCCH1VAL0$0$0 == 0x7022
                           007022   959 _ADCCH1VAL0	=	0x7022
                           007023   960 G$ADCCH1VAL1$0$0 == 0x7023
                           007023   961 _ADCCH1VAL1	=	0x7023
                           007022   962 G$ADCCH1VAL$0$0 == 0x7022
                           007022   963 _ADCCH1VAL	=	0x7022
                           007024   964 G$ADCCH2VAL0$0$0 == 0x7024
                           007024   965 _ADCCH2VAL0	=	0x7024
                           007025   966 G$ADCCH2VAL1$0$0 == 0x7025
                           007025   967 _ADCCH2VAL1	=	0x7025
                           007024   968 G$ADCCH2VAL$0$0 == 0x7024
                           007024   969 _ADCCH2VAL	=	0x7024
                           007026   970 G$ADCCH3VAL0$0$0 == 0x7026
                           007026   971 _ADCCH3VAL0	=	0x7026
                           007027   972 G$ADCCH3VAL1$0$0 == 0x7027
                           007027   973 _ADCCH3VAL1	=	0x7027
                           007026   974 G$ADCCH3VAL$0$0 == 0x7026
                           007026   975 _ADCCH3VAL	=	0x7026
                           007028   976 G$ADCTUNE0$0$0 == 0x7028
                           007028   977 _ADCTUNE0	=	0x7028
                           007029   978 G$ADCTUNE1$0$0 == 0x7029
                           007029   979 _ADCTUNE1	=	0x7029
                           00702A   980 G$ADCTUNE2$0$0 == 0x702a
                           00702A   981 _ADCTUNE2	=	0x702a
                           007010   982 G$DMA0ADDR0$0$0 == 0x7010
                           007010   983 _DMA0ADDR0	=	0x7010
                           007011   984 G$DMA0ADDR1$0$0 == 0x7011
                           007011   985 _DMA0ADDR1	=	0x7011
                           007010   986 G$DMA0ADDR$0$0 == 0x7010
                           007010   987 _DMA0ADDR	=	0x7010
                           007014   988 G$DMA0CONFIG$0$0 == 0x7014
                           007014   989 _DMA0CONFIG	=	0x7014
                           007012   990 G$DMA1ADDR0$0$0 == 0x7012
                           007012   991 _DMA1ADDR0	=	0x7012
                           007013   992 G$DMA1ADDR1$0$0 == 0x7013
                           007013   993 _DMA1ADDR1	=	0x7013
                           007012   994 G$DMA1ADDR$0$0 == 0x7012
                           007012   995 _DMA1ADDR	=	0x7012
                           007015   996 G$DMA1CONFIG$0$0 == 0x7015
                           007015   997 _DMA1CONFIG	=	0x7015
                           007070   998 G$FRCOSCCONFIG$0$0 == 0x7070
                           007070   999 _FRCOSCCONFIG	=	0x7070
                           007071  1000 G$FRCOSCCTRL$0$0 == 0x7071
                           007071  1001 _FRCOSCCTRL	=	0x7071
                           007076  1002 G$FRCOSCFREQ0$0$0 == 0x7076
                           007076  1003 _FRCOSCFREQ0	=	0x7076
                           007077  1004 G$FRCOSCFREQ1$0$0 == 0x7077
                           007077  1005 _FRCOSCFREQ1	=	0x7077
                           007076  1006 G$FRCOSCFREQ$0$0 == 0x7076
                           007076  1007 _FRCOSCFREQ	=	0x7076
                           007072  1008 G$FRCOSCKFILT0$0$0 == 0x7072
                           007072  1009 _FRCOSCKFILT0	=	0x7072
                           007073  1010 G$FRCOSCKFILT1$0$0 == 0x7073
                           007073  1011 _FRCOSCKFILT1	=	0x7073
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
                           00FC00  1125 _flash_calsector	=	0xfc00
                                   1126 ;--------------------------------------------------------
                                   1127 ; absolute external ram data
                                   1128 ;--------------------------------------------------------
                                   1129 	.area XABS    (ABS,XDATA)
                                   1130 ;--------------------------------------------------------
                                   1131 ; external initialized ram data
                                   1132 ;--------------------------------------------------------
                                   1133 	.area XISEG   (XDATA)
                                   1134 	.area HOME    (CODE)
                                   1135 	.area GSINIT0 (CODE)
                                   1136 	.area GSINIT1 (CODE)
                                   1137 	.area GSINIT2 (CODE)
                                   1138 	.area GSINIT3 (CODE)
                                   1139 	.area GSINIT4 (CODE)
                                   1140 	.area GSINIT5 (CODE)
                                   1141 	.area GSINIT  (CODE)
                                   1142 	.area GSFINAL (CODE)
                                   1143 	.area CSEG    (CODE)
                                   1144 ;--------------------------------------------------------
                                   1145 ; global & static initialisations
                                   1146 ;--------------------------------------------------------
                                   1147 	.area HOME    (CODE)
                                   1148 	.area GSINIT  (CODE)
                                   1149 	.area GSFINAL (CODE)
                                   1150 	.area GSINIT  (CODE)
                                   1151 ;--------------------------------------------------------
                                   1152 ; Home
                                   1153 ;--------------------------------------------------------
                                   1154 	.area HOME    (CODE)
                                   1155 	.area HOME    (CODE)
                                   1156 ;--------------------------------------------------------
                                   1157 ; code
                                   1158 ;--------------------------------------------------------
                                   1159 	.area CSEG    (CODE)
                                   1160 	.area CSEG    (CODE)
                                   1161 	.area CONST   (CODE)
                                   1162 	.area XINIT   (CODE)
                                   1163 	.area CABS    (ABS,CODE)
