oresat/oresat-c3-rf/AxSem_Profiles/AX_C3_L_RX/MASTER/obj/Debug/COMMON/easyax5043.rst

                                      1 ;--------------------------------------------------------
                                      2 ; File Created by SDCC : free open source ANSI-C Compiler
                                      3 ; Version 3.6.0 #9615 (MINGW64)
                                      4 ;--------------------------------------------------------
                                      5 	.module easyax5043
                                      6 	.optsdcc -mmcs51 --model-small
                                      7 	
                                      8 ;--------------------------------------------------------
                                      9 ; Public variables in this module
                                     10 ;--------------------------------------------------------
                                     11 	.globl _axradio_wait_n_lposccycles
                                     12 	.globl _ax5043_init_registers_rx
                                     13 	.globl _ax5043_init_registers_tx
                                     14 	.globl _memset
                                     15 	.globl _memcpy
                                     16 	.globl _wtimer_remove_callback
                                     17 	.globl _wtimer_add_callback
                                     18 	.globl _wtimer_remove
                                     19 	.globl _wtimer1_addrelative
                                     20 	.globl _wtimer0_addrelative
                                     21 	.globl _wtimer0_addabsolute
                                     22 	.globl _wtimer0_curtime
                                     23 	.globl _wtimer_runcallbacks
                                     24 	.globl _wtimer_idle
                                     25 	.globl _ax5043_writefifo
                                     26 	.globl _ax5043_readfifo
                                     27 	.globl _ax5043_wakeup_deepsleep
                                     28 	.globl _ax5043_enter_deepsleep
                                     29 	.globl _ax5043_reset
                                     30 	.globl _ax5043_commsleepexit
                                     31 	.globl _radio_read24
                                     32 	.globl _radio_read16
                                     33 	.globl _pn9_buffer
                                     34 	.globl _pn9_advance_byte
                                     35 	.globl _pn9_advance_bits
                                     36 	.globl _disable_radio_interrupt_in_mcu_pin
                                     37 	.globl _enable_radio_interrupt_in_mcu_pin
                                     38 	.globl _axradio_framing_append_crc
                                     39 	.globl _axradio_framing_check_crc
                                     40 	.globl _ax5043_set_registers_rxcont_singleparamset
                                     41 	.globl _ax5043_set_registers_rxcont
                                     42 	.globl _ax5043_set_registers_rxwor
                                     43 	.globl _ax5043_set_registers_rx
                                     44 	.globl _ax5043_set_registers_tx
                                     45 	.globl _ax5043_set_registers
                                     46 	.globl _axradio_conv_freq_fromreg
                                     47 	.globl _axradio_statuschange
                                     48 	.globl _axradio_conv_timeinterval_totimer0
                                     49 	.globl _enter_standby
                                     50 	.globl _checksignedlimit32
                                     51 	.globl _checksignedlimit16
                                     52 	.globl _signedlimit16
                                     53 	.globl _signextend24
                                     54 	.globl _signextend20
                                     55 	.globl _signextend16
                                     56 	.globl _PORTC_7
                                     57 	.globl _PORTC_6
                                     58 	.globl _PORTC_5
                                     59 	.globl _PORTC_4
                                     60 	.globl _PORTC_3
                                     61 	.globl _PORTC_2
                                     62 	.globl _PORTC_1
                                     63 	.globl _PORTC_0
                                     64 	.globl _PORTB_7
                                     65 	.globl _PORTB_6
                                     66 	.globl _PORTB_5
                                     67 	.globl _PORTB_4
                                     68 	.globl _PORTB_3
                                     69 	.globl _PORTB_2
                                     70 	.globl _PORTB_1
                                     71 	.globl _PORTB_0
                                     72 	.globl _PORTA_7
                                     73 	.globl _PORTA_6
                                     74 	.globl _PORTA_5
                                     75 	.globl _PORTA_4
                                     76 	.globl _PORTA_3
                                     77 	.globl _PORTA_2
                                     78 	.globl _PORTA_1
                                     79 	.globl _PORTA_0
                                     80 	.globl _PINC_7
                                     81 	.globl _PINC_6
                                     82 	.globl _PINC_5
                                     83 	.globl _PINC_4
                                     84 	.globl _PINC_3
                                     85 	.globl _PINC_2
                                     86 	.globl _PINC_1
                                     87 	.globl _PINC_0
                                     88 	.globl _PINB_7
                                     89 	.globl _PINB_6
                                     90 	.globl _PINB_5
                                     91 	.globl _PINB_4
                                     92 	.globl _PINB_3
                                     93 	.globl _PINB_2
                                     94 	.globl _PINB_1
                                     95 	.globl _PINB_0
                                     96 	.globl _PINA_7
                                     97 	.globl _PINA_6
                                     98 	.globl _PINA_5
                                     99 	.globl _PINA_4
                                    100 	.globl _PINA_3
                                    101 	.globl _PINA_2
                                    102 	.globl _PINA_1
                                    103 	.globl _PINA_0
                                    104 	.globl _CY
                                    105 	.globl _AC
                                    106 	.globl _F0
                                    107 	.globl _RS1
                                    108 	.globl _RS0
                                    109 	.globl _OV
                                    110 	.globl _F1
                                    111 	.globl _P
                                    112 	.globl _IP_7
                                    113 	.globl _IP_6
                                    114 	.globl _IP_5
                                    115 	.globl _IP_4
                                    116 	.globl _IP_3
                                    117 	.globl _IP_2
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
                                    194 	.globl _WTCNTB0
                                    195 	.globl _WTCNTA
                                    196 	.globl _WTCNTA1
                                    197 	.globl _WTCNTA0
                                    198 	.globl _WTCFGB
                                    199 	.globl _WTCFGA
                                    200 	.globl _WDTRESET
                                    201 	.globl _WDTCFG
                                    202 	.globl _U1STATUS
                                    203 	.globl _U1SHREG
                                    204 	.globl _U1MODE
                                    205 	.globl _U1CTRL
                                    206 	.globl _U0STATUS
                                    207 	.globl _U0SHREG
                                    208 	.globl _U0MODE
                                    209 	.globl _U0CTRL
                                    210 	.globl _T2STATUS
                                    211 	.globl _T2PERIOD
                                    212 	.globl _T2PERIOD1
                                    213 	.globl _T2PERIOD0
                                    214 	.globl _T2MODE
                                    215 	.globl _T2CNT
                                    216 	.globl _T2CNT1
                                    217 	.globl _T2CNT0
                                    218 	.globl _T2CLKSRC
                                    219 	.globl _T1STATUS
                                    220 	.globl _T1PERIOD
                                    221 	.globl _T1PERIOD1
                                    222 	.globl _T1PERIOD0
                                    223 	.globl _T1MODE
                                    224 	.globl _T1CNT
                                    225 	.globl _T1CNT1
                                    226 	.globl _T1CNT0
                                    227 	.globl _T1CLKSRC
                                    228 	.globl _T0STATUS
                                    229 	.globl _T0PERIOD
                                    230 	.globl _T0PERIOD1
                                    231 	.globl _T0PERIOD0
                                    232 	.globl _T0MODE
                                    233 	.globl _T0CNT
                                    234 	.globl _T0CNT1
                                    235 	.globl _T0CNT0
                                    236 	.globl _T0CLKSRC
                                    237 	.globl _SPSTATUS
                                    238 	.globl _SPSHREG
                                    239 	.globl _SPMODE
                                    240 	.globl _SPCLKSRC
                                    241 	.globl _RADIOSTAT
                                    242 	.globl _RADIOSTAT1
                                    243 	.globl _RADIOSTAT0
                                    244 	.globl _RADIODATA
                                    245 	.globl _RADIODATA3
                                    246 	.globl _RADIODATA2
                                    247 	.globl _RADIODATA1
                                    248 	.globl _RADIODATA0
                                    249 	.globl _RADIOADDR
                                    250 	.globl _RADIOADDR1
                                    251 	.globl _RADIOADDR0
                                    252 	.globl _RADIOACC
                                    253 	.globl _OC1STATUS
                                    254 	.globl _OC1PIN
                                    255 	.globl _OC1MODE
                                    256 	.globl _OC1COMP
                                    257 	.globl _OC1COMP1
                                    258 	.globl _OC1COMP0
                                    259 	.globl _OC0STATUS
                                    260 	.globl _OC0PIN
                                    261 	.globl _OC0MODE
                                    262 	.globl _OC0COMP
                                    263 	.globl _OC0COMP1
                                    264 	.globl _OC0COMP0
                                    265 	.globl _NVSTATUS
                                    266 	.globl _NVKEY
                                    267 	.globl _NVDATA
                                    268 	.globl _NVDATA1
                                    269 	.globl _NVDATA0
                                    270 	.globl _NVADDR
                                    271 	.globl _NVADDR1
                                    272 	.globl _NVADDR0
                                    273 	.globl _IC1STATUS
                                    274 	.globl _IC1MODE
                                    275 	.globl _IC1CAPT
                                    276 	.globl _IC1CAPT1
                                    277 	.globl _IC1CAPT0
                                    278 	.globl _IC0STATUS
                                    279 	.globl _IC0MODE
                                    280 	.globl _IC0CAPT
                                    281 	.globl _IC0CAPT1
                                    282 	.globl _IC0CAPT0
                                    283 	.globl _PORTR
                                    284 	.globl _PORTC
                                    285 	.globl _PORTB
                                    286 	.globl _PORTA
                                    287 	.globl _PINR
                                    288 	.globl _PINC
                                    289 	.globl _PINB
                                    290 	.globl _PINA
                                    291 	.globl _DIRR
                                    292 	.globl _DIRC
                                    293 	.globl _DIRB
                                    294 	.globl _DIRA
                                    295 	.globl _DBGLNKSTAT
                                    296 	.globl _DBGLNKBUF
                                    297 	.globl _CODECONFIG
                                    298 	.globl _CLKSTAT
                                    299 	.globl _CLKCON
                                    300 	.globl _ANALOGCOMP
                                    301 	.globl _ADCCONV
                                    302 	.globl _ADCCLKSRC
                                    303 	.globl _ADCCH3CONFIG
                                    304 	.globl _ADCCH2CONFIG
                                    305 	.globl _ADCCH1CONFIG
                                    306 	.globl _ADCCH0CONFIG
                                    307 	.globl __XPAGE
                                    308 	.globl _XPAGE
                                    309 	.globl _SP
                                    310 	.globl _PSW
                                    311 	.globl _PCON
                                    312 	.globl _IP
                                    313 	.globl _IE
                                    314 	.globl _EIP
                                    315 	.globl _EIE
                                    316 	.globl _E2IP
                                    317 	.globl _E2IE
                                    318 	.globl _DPS
                                    319 	.globl _DPTR1
                                    320 	.globl _DPTR0
                                    321 	.globl _DPL1
                                    322 	.globl _DPL
                                    323 	.globl _DPH1
                                    324 	.globl _DPH
                                    325 	.globl _B
                                    326 	.globl _ACC
                                    327 	.globl _radio_not_found_lcd_display
                                    328 	.globl _radio_lcd_display
                                    329 	.globl _f33_saved
                                    330 	.globl _f32_saved
                                    331 	.globl _f31_saved
                                    332 	.globl _f30_saved
                                    333 	.globl _axradio_timer
                                    334 	.globl _axradio_cb_transmitdata
                                    335 	.globl _axradio_cb_transmitend
                                    336 	.globl _axradio_cb_transmitstart
                                    337 	.globl _axradio_cb_channelstate
                                    338 	.globl _axradio_cb_receivesfd
                                    339 	.globl _axradio_cb_receive
                                    340 	.globl _axradio_rxbuffer
                                    341 	.globl _axradio_txbuffer
                                    342 	.globl _axradio_default_remoteaddr
                                    343 	.globl _axradio_localaddr
                                    344 	.globl _axradio_timeanchor
                                    345 	.globl _axradio_sync_periodcorr
                                    346 	.globl _axradio_sync_time
                                    347 	.globl _axradio_ack_seqnr
                                    348 	.globl _axradio_ack_count
                                    349 	.globl _axradio_curfreqoffset
                                    350 	.globl _axradio_curchannel
                                    351 	.globl _axradio_txbuffer_cnt
                                    352 	.globl _axradio_txbuffer_len
                                    353 	.globl _axradio_syncstate
                                    354 	.globl _AX5043_TIMEGAIN3NB
                                    355 	.globl _AX5043_TIMEGAIN2NB
                                    356 	.globl _AX5043_TIMEGAIN1NB
                                    357 	.globl _AX5043_TIMEGAIN0NB
                                    358 	.globl _AX5043_RXPARAMSETSNB
                                    359 	.globl _AX5043_RXPARAMCURSETNB
                                    360 	.globl _AX5043_PKTMAXLENNB
                                    361 	.globl _AX5043_PKTLENOFFSETNB
                                    362 	.globl _AX5043_PKTLENCFGNB
                                    363 	.globl _AX5043_PKTADDRMASK3NB
                                    364 	.globl _AX5043_PKTADDRMASK2NB
                                    365 	.globl _AX5043_PKTADDRMASK1NB
                                    366 	.globl _AX5043_PKTADDRMASK0NB
                                    367 	.globl _AX5043_PKTADDRCFGNB
                                    368 	.globl _AX5043_PKTADDR3NB
                                    369 	.globl _AX5043_PKTADDR2NB
                                    370 	.globl _AX5043_PKTADDR1NB
                                    371 	.globl _AX5043_PKTADDR0NB
                                    372 	.globl _AX5043_PHASEGAIN3NB
                                    373 	.globl _AX5043_PHASEGAIN2NB
                                    374 	.globl _AX5043_PHASEGAIN1NB
                                    375 	.globl _AX5043_PHASEGAIN0NB
                                    376 	.globl _AX5043_FREQUENCYLEAKNB
                                    377 	.globl _AX5043_FREQUENCYGAIND3NB
                                    378 	.globl _AX5043_FREQUENCYGAIND2NB
                                    379 	.globl _AX5043_FREQUENCYGAIND1NB
                                    380 	.globl _AX5043_FREQUENCYGAIND0NB
                                    381 	.globl _AX5043_FREQUENCYGAINC3NB
                                    382 	.globl _AX5043_FREQUENCYGAINC2NB
                                    383 	.globl _AX5043_FREQUENCYGAINC1NB
                                    384 	.globl _AX5043_FREQUENCYGAINC0NB
                                    385 	.globl _AX5043_FREQUENCYGAINB3NB
                                    386 	.globl _AX5043_FREQUENCYGAINB2NB
                                    387 	.globl _AX5043_FREQUENCYGAINB1NB
                                    388 	.globl _AX5043_FREQUENCYGAINB0NB
                                    389 	.globl _AX5043_FREQUENCYGAINA3NB
                                    390 	.globl _AX5043_FREQUENCYGAINA2NB
                                    391 	.globl _AX5043_FREQUENCYGAINA1NB
                                    392 	.globl _AX5043_FREQUENCYGAINA0NB
                                    393 	.globl _AX5043_FREQDEV13NB
                                    394 	.globl _AX5043_FREQDEV12NB
                                    395 	.globl _AX5043_FREQDEV11NB
                                    396 	.globl _AX5043_FREQDEV10NB
                                    397 	.globl _AX5043_FREQDEV03NB
                                    398 	.globl _AX5043_FREQDEV02NB
                                    399 	.globl _AX5043_FREQDEV01NB
                                    400 	.globl _AX5043_FREQDEV00NB
                                    401 	.globl _AX5043_FOURFSK3NB
                                    402 	.globl _AX5043_FOURFSK2NB
                                    403 	.globl _AX5043_FOURFSK1NB
                                    404 	.globl _AX5043_FOURFSK0NB
                                    405 	.globl _AX5043_DRGAIN3NB
                                    406 	.globl _AX5043_DRGAIN2NB
                                    407 	.globl _AX5043_DRGAIN1NB
                                    408 	.globl _AX5043_DRGAIN0NB
                                    409 	.globl _AX5043_BBOFFSRES3NB
                                    410 	.globl _AX5043_BBOFFSRES2NB
                                    411 	.globl _AX5043_BBOFFSRES1NB
                                    412 	.globl _AX5043_BBOFFSRES0NB
                                    413 	.globl _AX5043_AMPLITUDEGAIN3NB
                                    414 	.globl _AX5043_AMPLITUDEGAIN2NB
                                    415 	.globl _AX5043_AMPLITUDEGAIN1NB
                                    416 	.globl _AX5043_AMPLITUDEGAIN0NB
                                    417 	.globl _AX5043_AGCTARGET3NB
                                    418 	.globl _AX5043_AGCTARGET2NB
                                    419 	.globl _AX5043_AGCTARGET1NB
                                    420 	.globl _AX5043_AGCTARGET0NB
                                    421 	.globl _AX5043_AGCMINMAX3NB
                                    422 	.globl _AX5043_AGCMINMAX2NB
                                    423 	.globl _AX5043_AGCMINMAX1NB
                                    424 	.globl _AX5043_AGCMINMAX0NB
                                    425 	.globl _AX5043_AGCGAIN3NB
                                    426 	.globl _AX5043_AGCGAIN2NB
                                    427 	.globl _AX5043_AGCGAIN1NB
                                    428 	.globl _AX5043_AGCGAIN0NB
                                    429 	.globl _AX5043_AGCAHYST3NB
                                    430 	.globl _AX5043_AGCAHYST2NB
                                    431 	.globl _AX5043_AGCAHYST1NB
                                    432 	.globl _AX5043_AGCAHYST0NB
                                    433 	.globl _AX5043_0xF44NB
                                    434 	.globl _AX5043_0xF35NB
                                    435 	.globl _AX5043_0xF34NB
                                    436 	.globl _AX5043_0xF33NB
                                    437 	.globl _AX5043_0xF32NB
                                    438 	.globl _AX5043_0xF31NB
                                    439 	.globl _AX5043_0xF30NB
                                    440 	.globl _AX5043_0xF26NB
                                    441 	.globl _AX5043_0xF23NB
                                    442 	.globl _AX5043_0xF22NB
                                    443 	.globl _AX5043_0xF21NB
                                    444 	.globl _AX5043_0xF1CNB
                                    445 	.globl _AX5043_0xF18NB
                                    446 	.globl _AX5043_0xF0CNB
                                    447 	.globl _AX5043_0xF00NB
                                    448 	.globl _AX5043_XTALSTATUSNB
                                    449 	.globl _AX5043_XTALOSCNB
                                    450 	.globl _AX5043_XTALCAPNB
                                    451 	.globl _AX5043_XTALAMPLNB
                                    452 	.globl _AX5043_WAKEUPXOEARLYNB
                                    453 	.globl _AX5043_WAKEUPTIMER1NB
                                    454 	.globl _AX5043_WAKEUPTIMER0NB
                                    455 	.globl _AX5043_WAKEUPFREQ1NB
                                    456 	.globl _AX5043_WAKEUPFREQ0NB
                                    457 	.globl _AX5043_WAKEUP1NB
                                    458 	.globl _AX5043_WAKEUP0NB
                                    459 	.globl _AX5043_TXRATE2NB
                                    460 	.globl _AX5043_TXRATE1NB
                                    461 	.globl _AX5043_TXRATE0NB
                                    462 	.globl _AX5043_TXPWRCOEFFE1NB
                                    463 	.globl _AX5043_TXPWRCOEFFE0NB
                                    464 	.globl _AX5043_TXPWRCOEFFD1NB
                                    465 	.globl _AX5043_TXPWRCOEFFD0NB
                                    466 	.globl _AX5043_TXPWRCOEFFC1NB
                                    467 	.globl _AX5043_TXPWRCOEFFC0NB
                                    468 	.globl _AX5043_TXPWRCOEFFB1NB
                                    469 	.globl _AX5043_TXPWRCOEFFB0NB
                                    470 	.globl _AX5043_TXPWRCOEFFA1NB
                                    471 	.globl _AX5043_TXPWRCOEFFA0NB
                                    472 	.globl _AX5043_TRKRFFREQ2NB
                                    473 	.globl _AX5043_TRKRFFREQ1NB
                                    474 	.globl _AX5043_TRKRFFREQ0NB
                                    475 	.globl _AX5043_TRKPHASE1NB
                                    476 	.globl _AX5043_TRKPHASE0NB
                                    477 	.globl _AX5043_TRKFSKDEMOD1NB
                                    478 	.globl _AX5043_TRKFSKDEMOD0NB
                                    479 	.globl _AX5043_TRKFREQ1NB
                                    480 	.globl _AX5043_TRKFREQ0NB
                                    481 	.globl _AX5043_TRKDATARATE2NB
                                    482 	.globl _AX5043_TRKDATARATE1NB
                                    483 	.globl _AX5043_TRKDATARATE0NB
                                    484 	.globl _AX5043_TRKAMPLITUDE1NB
                                    485 	.globl _AX5043_TRKAMPLITUDE0NB
                                    486 	.globl _AX5043_TRKAFSKDEMOD1NB
                                    487 	.globl _AX5043_TRKAFSKDEMOD0NB
                                    488 	.globl _AX5043_TMGTXSETTLENB
                                    489 	.globl _AX5043_TMGTXBOOSTNB
                                    490 	.globl _AX5043_TMGRXSETTLENB
                                    491 	.globl _AX5043_TMGRXRSSINB
                                    492 	.globl _AX5043_TMGRXPREAMBLE3NB
                                    493 	.globl _AX5043_TMGRXPREAMBLE2NB
                                    494 	.globl _AX5043_TMGRXPREAMBLE1NB
                                    495 	.globl _AX5043_TMGRXOFFSACQNB
                                    496 	.globl _AX5043_TMGRXCOARSEAGCNB
                                    497 	.globl _AX5043_TMGRXBOOSTNB
                                    498 	.globl _AX5043_TMGRXAGCNB
                                    499 	.globl _AX5043_TIMER2NB
                                    500 	.globl _AX5043_TIMER1NB
                                    501 	.globl _AX5043_TIMER0NB
                                    502 	.globl _AX5043_SILICONREVISIONNB
                                    503 	.globl _AX5043_SCRATCHNB
                                    504 	.globl _AX5043_RXDATARATE2NB
                                    505 	.globl _AX5043_RXDATARATE1NB
                                    506 	.globl _AX5043_RXDATARATE0NB
                                    507 	.globl _AX5043_RSSIREFERENCENB
                                    508 	.globl _AX5043_RSSIABSTHRNB
                                    509 	.globl _AX5043_RSSINB
                                    510 	.globl _AX5043_REFNB
                                    511 	.globl _AX5043_RADIOSTATENB
                                    512 	.globl _AX5043_RADIOEVENTREQ1NB
                                    513 	.globl _AX5043_RADIOEVENTREQ0NB
                                    514 	.globl _AX5043_RADIOEVENTMASK1NB
                                    515 	.globl _AX5043_RADIOEVENTMASK0NB
                                    516 	.globl _AX5043_PWRMODENB
                                    517 	.globl _AX5043_PWRAMPNB
                                    518 	.globl _AX5043_POWSTICKYSTATNB
                                    519 	.globl _AX5043_POWSTATNB
                                    520 	.globl _AX5043_POWIRQMASKNB
                                    521 	.globl _AX5043_POWCTRL1NB
                                    522 	.globl _AX5043_PLLVCOIRNB
                                    523 	.globl _AX5043_PLLVCOINB
                                    524 	.globl _AX5043_PLLVCODIVNB
                                    525 	.globl _AX5043_PLLRNGCLKNB
                                    526 	.globl _AX5043_PLLRANGINGBNB
                                    527 	.globl _AX5043_PLLRANGINGANB
                                    528 	.globl _AX5043_PLLLOOPBOOSTNB
                                    529 	.globl _AX5043_PLLLOOPNB
                                    530 	.globl _AX5043_PLLLOCKDETNB
                                    531 	.globl _AX5043_PLLCPIBOOSTNB
                                    532 	.globl _AX5043_PLLCPINB
                                    533 	.globl _AX5043_PKTSTOREFLAGSNB
                                    534 	.globl _AX5043_PKTMISCFLAGSNB
                                    535 	.globl _AX5043_PKTCHUNKSIZENB
                                    536 	.globl _AX5043_PKTACCEPTFLAGSNB
                                    537 	.globl _AX5043_PINSTATENB
                                    538 	.globl _AX5043_PINFUNCSYSCLKNB
                                    539 	.globl _AX5043_PINFUNCPWRAMPNB
                                    540 	.globl _AX5043_PINFUNCIRQNB
                                    541 	.globl _AX5043_PINFUNCDCLKNB
                                    542 	.globl _AX5043_PINFUNCDATANB
                                    543 	.globl _AX5043_PINFUNCANTSELNB
                                    544 	.globl _AX5043_MODULATIONNB
                                    545 	.globl _AX5043_MODCFGPNB
                                    546 	.globl _AX5043_MODCFGFNB
                                    547 	.globl _AX5043_MODCFGANB
                                    548 	.globl _AX5043_MAXRFOFFSET2NB
                                    549 	.globl _AX5043_MAXRFOFFSET1NB
                                    550 	.globl _AX5043_MAXRFOFFSET0NB
                                    551 	.globl _AX5043_MAXDROFFSET2NB
                                    552 	.globl _AX5043_MAXDROFFSET1NB
                                    553 	.globl _AX5043_MAXDROFFSET0NB
                                    554 	.globl _AX5043_MATCH1PAT1NB
                                    555 	.globl _AX5043_MATCH1PAT0NB
                                    556 	.globl _AX5043_MATCH1MINNB
                                    557 	.globl _AX5043_MATCH1MAXNB
                                    558 	.globl _AX5043_MATCH1LENNB
                                    559 	.globl _AX5043_MATCH0PAT3NB
                                    560 	.globl _AX5043_MATCH0PAT2NB
                                    561 	.globl _AX5043_MATCH0PAT1NB
                                    562 	.globl _AX5043_MATCH0PAT0NB
                                    563 	.globl _AX5043_MATCH0MINNB
                                    564 	.globl _AX5043_MATCH0MAXNB
                                    565 	.globl _AX5043_MATCH0LENNB
                                    566 	.globl _AX5043_LPOSCSTATUSNB
                                    567 	.globl _AX5043_LPOSCREF1NB
                                    568 	.globl _AX5043_LPOSCREF0NB
                                    569 	.globl _AX5043_LPOSCPER1NB
                                    570 	.globl _AX5043_LPOSCPER0NB
                                    571 	.globl _AX5043_LPOSCKFILT1NB
                                    572 	.globl _AX5043_LPOSCKFILT0NB
                                    573 	.globl _AX5043_LPOSCFREQ1NB
                                    574 	.globl _AX5043_LPOSCFREQ0NB
                                    575 	.globl _AX5043_LPOSCCONFIGNB
                                    576 	.globl _AX5043_IRQREQUEST1NB
                                    577 	.globl _AX5043_IRQREQUEST0NB
                                    578 	.globl _AX5043_IRQMASK1NB
                                    579 	.globl _AX5043_IRQMASK0NB
                                    580 	.globl _AX5043_IRQINVERSION1NB
                                    581 	.globl _AX5043_IRQINVERSION0NB
                                    582 	.globl _AX5043_IFFREQ1NB
                                    583 	.globl _AX5043_IFFREQ0NB
                                    584 	.globl _AX5043_GPADCPERIODNB
                                    585 	.globl _AX5043_GPADCCTRLNB
                                    586 	.globl _AX5043_GPADC13VALUE1NB
                                    587 	.globl _AX5043_GPADC13VALUE0NB
                                    588 	.globl _AX5043_FSKDMIN1NB
                                    589 	.globl _AX5043_FSKDMIN0NB
                                    590 	.globl _AX5043_FSKDMAX1NB
                                    591 	.globl _AX5043_FSKDMAX0NB
                                    592 	.globl _AX5043_FSKDEV2NB
                                    593 	.globl _AX5043_FSKDEV1NB
                                    594 	.globl _AX5043_FSKDEV0NB
                                    595 	.globl _AX5043_FREQB3NB
                                    596 	.globl _AX5043_FREQB2NB
                                    597 	.globl _AX5043_FREQB1NB
                                    598 	.globl _AX5043_FREQB0NB
                                    599 	.globl _AX5043_FREQA3NB
                                    600 	.globl _AX5043_FREQA2NB
                                    601 	.globl _AX5043_FREQA1NB
                                    602 	.globl _AX5043_FREQA0NB
                                    603 	.globl _AX5043_FRAMINGNB
                                    604 	.globl _AX5043_FIFOTHRESH1NB
                                    605 	.globl _AX5043_FIFOTHRESH0NB
                                    606 	.globl _AX5043_FIFOSTATNB
                                    607 	.globl _AX5043_FIFOFREE1NB
                                    608 	.globl _AX5043_FIFOFREE0NB
                                    609 	.globl _AX5043_FIFODATANB
                                    610 	.globl _AX5043_FIFOCOUNT1NB
                                    611 	.globl _AX5043_FIFOCOUNT0NB
                                    612 	.globl _AX5043_FECSYNCNB
                                    613 	.globl _AX5043_FECSTATUSNB
                                    614 	.globl _AX5043_FECNB
                                    615 	.globl _AX5043_ENCODINGNB
                                    616 	.globl _AX5043_DIVERSITYNB
                                    617 	.globl _AX5043_DECIMATIONNB
                                    618 	.globl _AX5043_DACVALUE1NB
                                    619 	.globl _AX5043_DACVALUE0NB
                                    620 	.globl _AX5043_DACCONFIGNB
                                    621 	.globl _AX5043_CRCINIT3NB
                                    622 	.globl _AX5043_CRCINIT2NB
                                    623 	.globl _AX5043_CRCINIT1NB
                                    624 	.globl _AX5043_CRCINIT0NB
                                    625 	.globl _AX5043_BGNDRSSITHRNB
                                    626 	.globl _AX5043_BGNDRSSIGAINNB
                                    627 	.globl _AX5043_BGNDRSSINB
                                    628 	.globl _AX5043_BBTUNENB
                                    629 	.globl _AX5043_BBOFFSCAPNB
                                    630 	.globl _AX5043_AMPLFILTERNB
                                    631 	.globl _AX5043_AGCCOUNTERNB
                                    632 	.globl _AX5043_AFSKSPACE1NB
                                    633 	.globl _AX5043_AFSKSPACE0NB
                                    634 	.globl _AX5043_AFSKMARK1NB
                                    635 	.globl _AX5043_AFSKMARK0NB
                                    636 	.globl _AX5043_AFSKCTRLNB
                                    637 	.globl _AX5043_TIMEGAIN3
                                    638 	.globl _AX5043_TIMEGAIN2
                                    639 	.globl _AX5043_TIMEGAIN1
                                    640 	.globl _AX5043_TIMEGAIN0
                                    641 	.globl _AX5043_RXPARAMSETS
                                    642 	.globl _AX5043_RXPARAMCURSET
                                    643 	.globl _AX5043_PKTMAXLEN
                                    644 	.globl _AX5043_PKTLENOFFSET
                                    645 	.globl _AX5043_PKTLENCFG
                                    646 	.globl _AX5043_PKTADDRMASK3
                                    647 	.globl _AX5043_PKTADDRMASK2
                                    648 	.globl _AX5043_PKTADDRMASK1
                                    649 	.globl _AX5043_PKTADDRMASK0
                                    650 	.globl _AX5043_PKTADDRCFG
                                    651 	.globl _AX5043_PKTADDR3
                                    652 	.globl _AX5043_PKTADDR2
                                    653 	.globl _AX5043_PKTADDR1
                                    654 	.globl _AX5043_PKTADDR0
                                    655 	.globl _AX5043_PHASEGAIN3
                                    656 	.globl _AX5043_PHASEGAIN2
                                    657 	.globl _AX5043_PHASEGAIN1
                                    658 	.globl _AX5043_PHASEGAIN0
                                    659 	.globl _AX5043_FREQUENCYLEAK
                                    660 	.globl _AX5043_FREQUENCYGAIND3
                                    661 	.globl _AX5043_FREQUENCYGAIND2
                                    662 	.globl _AX5043_FREQUENCYGAIND1
                                    663 	.globl _AX5043_FREQUENCYGAIND0
                                    664 	.globl _AX5043_FREQUENCYGAINC3
                                    665 	.globl _AX5043_FREQUENCYGAINC2
                                    666 	.globl _AX5043_FREQUENCYGAINC1
                                    667 	.globl _AX5043_FREQUENCYGAINC0
                                    668 	.globl _AX5043_FREQUENCYGAINB3
                                    669 	.globl _AX5043_FREQUENCYGAINB2
                                    670 	.globl _AX5043_FREQUENCYGAINB1
                                    671 	.globl _AX5043_FREQUENCYGAINB0
                                    672 	.globl _AX5043_FREQUENCYGAINA3
                                    673 	.globl _AX5043_FREQUENCYGAINA2
                                    674 	.globl _AX5043_FREQUENCYGAINA1
                                    675 	.globl _AX5043_FREQUENCYGAINA0
                                    676 	.globl _AX5043_FREQDEV13
                                    677 	.globl _AX5043_FREQDEV12
                                    678 	.globl _AX5043_FREQDEV11
                                    679 	.globl _AX5043_FREQDEV10
                                    680 	.globl _AX5043_FREQDEV03
                                    681 	.globl _AX5043_FREQDEV02
                                    682 	.globl _AX5043_FREQDEV01
                                    683 	.globl _AX5043_FREQDEV00
                                    684 	.globl _AX5043_FOURFSK3
                                    685 	.globl _AX5043_FOURFSK2
                                    686 	.globl _AX5043_FOURFSK1
                                    687 	.globl _AX5043_FOURFSK0
                                    688 	.globl _AX5043_DRGAIN3
                                    689 	.globl _AX5043_DRGAIN2
                                    690 	.globl _AX5043_DRGAIN1
                                    691 	.globl _AX5043_DRGAIN0
                                    692 	.globl _AX5043_BBOFFSRES3
                                    693 	.globl _AX5043_BBOFFSRES2
                                    694 	.globl _AX5043_BBOFFSRES1
                                    695 	.globl _AX5043_BBOFFSRES0
                                    696 	.globl _AX5043_AMPLITUDEGAIN3
                                    697 	.globl _AX5043_AMPLITUDEGAIN2
                                    698 	.globl _AX5043_AMPLITUDEGAIN1
                                    699 	.globl _AX5043_AMPLITUDEGAIN0
                                    700 	.globl _AX5043_AGCTARGET3
                                    701 	.globl _AX5043_AGCTARGET2
                                    702 	.globl _AX5043_AGCTARGET1
                                    703 	.globl _AX5043_AGCTARGET0
                                    704 	.globl _AX5043_AGCMINMAX3
                                    705 	.globl _AX5043_AGCMINMAX2
                                    706 	.globl _AX5043_AGCMINMAX1
                                    707 	.globl _AX5043_AGCMINMAX0
                                    708 	.globl _AX5043_AGCGAIN3
                                    709 	.globl _AX5043_AGCGAIN2
                                    710 	.globl _AX5043_AGCGAIN1
                                    711 	.globl _AX5043_AGCGAIN0
                                    712 	.globl _AX5043_AGCAHYST3
                                    713 	.globl _AX5043_AGCAHYST2
                                    714 	.globl _AX5043_AGCAHYST1
                                    715 	.globl _AX5043_AGCAHYST0
                                    716 	.globl _AX5043_0xF44
                                    717 	.globl _AX5043_0xF35
                                    718 	.globl _AX5043_0xF34
                                    719 	.globl _AX5043_0xF33
                                    720 	.globl _AX5043_0xF32
                                    721 	.globl _AX5043_0xF31
                                    722 	.globl _AX5043_0xF30
                                    723 	.globl _AX5043_0xF26
                                    724 	.globl _AX5043_0xF23
                                    725 	.globl _AX5043_0xF22
                                    726 	.globl _AX5043_0xF21
                                    727 	.globl _AX5043_0xF1C
                                    728 	.globl _AX5043_0xF18
                                    729 	.globl _AX5043_0xF0C
                                    730 	.globl _AX5043_0xF00
                                    731 	.globl _AX5043_XTALSTATUS
                                    732 	.globl _AX5043_XTALOSC
                                    733 	.globl _AX5043_XTALCAP
                                    734 	.globl _AX5043_XTALAMPL
                                    735 	.globl _AX5043_WAKEUPXOEARLY
                                    736 	.globl _AX5043_WAKEUPTIMER1
                                    737 	.globl _AX5043_WAKEUPTIMER0
                                    738 	.globl _AX5043_WAKEUPFREQ1
                                    739 	.globl _AX5043_WAKEUPFREQ0
                                    740 	.globl _AX5043_WAKEUP1
                                    741 	.globl _AX5043_WAKEUP0
                                    742 	.globl _AX5043_TXRATE2
                                    743 	.globl _AX5043_TXRATE1
                                    744 	.globl _AX5043_TXRATE0
                                    745 	.globl _AX5043_TXPWRCOEFFE1
                                    746 	.globl _AX5043_TXPWRCOEFFE0
                                    747 	.globl _AX5043_TXPWRCOEFFD1
                                    748 	.globl _AX5043_TXPWRCOEFFD0
                                    749 	.globl _AX5043_TXPWRCOEFFC1
                                    750 	.globl _AX5043_TXPWRCOEFFC0
                                    751 	.globl _AX5043_TXPWRCOEFFB1
                                    752 	.globl _AX5043_TXPWRCOEFFB0
                                    753 	.globl _AX5043_TXPWRCOEFFA1
                                    754 	.globl _AX5043_TXPWRCOEFFA0
                                    755 	.globl _AX5043_TRKRFFREQ2
                                    756 	.globl _AX5043_TRKRFFREQ1
                                    757 	.globl _AX5043_TRKRFFREQ0
                                    758 	.globl _AX5043_TRKPHASE1
                                    759 	.globl _AX5043_TRKPHASE0
                                    760 	.globl _AX5043_TRKFSKDEMOD1
                                    761 	.globl _AX5043_TRKFSKDEMOD0
                                    762 	.globl _AX5043_TRKFREQ1
                                    763 	.globl _AX5043_TRKFREQ0
                                    764 	.globl _AX5043_TRKDATARATE2
                                    765 	.globl _AX5043_TRKDATARATE1
                                    766 	.globl _AX5043_TRKDATARATE0
                                    767 	.globl _AX5043_TRKAMPLITUDE1
                                    768 	.globl _AX5043_TRKAMPLITUDE0
                                    769 	.globl _AX5043_TRKAFSKDEMOD1
                                    770 	.globl _AX5043_TRKAFSKDEMOD0
                                    771 	.globl _AX5043_TMGTXSETTLE
                                    772 	.globl _AX5043_TMGTXBOOST
                                    773 	.globl _AX5043_TMGRXSETTLE
                                    774 	.globl _AX5043_TMGRXRSSI
                                    775 	.globl _AX5043_TMGRXPREAMBLE3
                                    776 	.globl _AX5043_TMGRXPREAMBLE2
                                    777 	.globl _AX5043_TMGRXPREAMBLE1
                                    778 	.globl _AX5043_TMGRXOFFSACQ
                                    779 	.globl _AX5043_TMGRXCOARSEAGC
                                    780 	.globl _AX5043_TMGRXBOOST
                                    781 	.globl _AX5043_TMGRXAGC
                                    782 	.globl _AX5043_TIMER2
                                    783 	.globl _AX5043_TIMER1
                                    784 	.globl _AX5043_TIMER0
                                    785 	.globl _AX5043_SILICONREVISION
                                    786 	.globl _AX5043_SCRATCH
                                    787 	.globl _AX5043_RXDATARATE2
                                    788 	.globl _AX5043_RXDATARATE1
                                    789 	.globl _AX5043_RXDATARATE0
                                    790 	.globl _AX5043_RSSIREFERENCE
                                    791 	.globl _AX5043_RSSIABSTHR
                                    792 	.globl _AX5043_RSSI
                                    793 	.globl _AX5043_REF
                                    794 	.globl _AX5043_RADIOSTATE
                                    795 	.globl _AX5043_RADIOEVENTREQ1
                                    796 	.globl _AX5043_RADIOEVENTREQ0
                                    797 	.globl _AX5043_RADIOEVENTMASK1
                                    798 	.globl _AX5043_RADIOEVENTMASK0
                                    799 	.globl _AX5043_PWRMODE
                                    800 	.globl _AX5043_PWRAMP
                                    801 	.globl _AX5043_POWSTICKYSTAT
                                    802 	.globl _AX5043_POWSTAT
                                    803 	.globl _AX5043_POWIRQMASK
                                    804 	.globl _AX5043_POWCTRL1
                                    805 	.globl _AX5043_PLLVCOIR
                                    806 	.globl _AX5043_PLLVCOI
                                    807 	.globl _AX5043_PLLVCODIV
                                    808 	.globl _AX5043_PLLRNGCLK
                                    809 	.globl _AX5043_PLLRANGINGB
                                    810 	.globl _AX5043_PLLRANGINGA
                                    811 	.globl _AX5043_PLLLOOPBOOST
                                    812 	.globl _AX5043_PLLLOOP
                                    813 	.globl _AX5043_PLLLOCKDET
                                    814 	.globl _AX5043_PLLCPIBOOST
                                    815 	.globl _AX5043_PLLCPI
                                    816 	.globl _AX5043_PKTSTOREFLAGS
                                    817 	.globl _AX5043_PKTMISCFLAGS
                                    818 	.globl _AX5043_PKTCHUNKSIZE
                                    819 	.globl _AX5043_PKTACCEPTFLAGS
                                    820 	.globl _AX5043_PINSTATE
                                    821 	.globl _AX5043_PINFUNCSYSCLK
                                    822 	.globl _AX5043_PINFUNCPWRAMP
                                    823 	.globl _AX5043_PINFUNCIRQ
                                    824 	.globl _AX5043_PINFUNCDCLK
                                    825 	.globl _AX5043_PINFUNCDATA
                                    826 	.globl _AX5043_PINFUNCANTSEL
                                    827 	.globl _AX5043_MODULATION
                                    828 	.globl _AX5043_MODCFGP
                                    829 	.globl _AX5043_MODCFGF
                                    830 	.globl _AX5043_MODCFGA
                                    831 	.globl _AX5043_MAXRFOFFSET2
                                    832 	.globl _AX5043_MAXRFOFFSET1
                                    833 	.globl _AX5043_MAXRFOFFSET0
                                    834 	.globl _AX5043_MAXDROFFSET2
                                    835 	.globl _AX5043_MAXDROFFSET1
                                    836 	.globl _AX5043_MAXDROFFSET0
                                    837 	.globl _AX5043_MATCH1PAT1
                                    838 	.globl _AX5043_MATCH1PAT0
                                    839 	.globl _AX5043_MATCH1MIN
                                    840 	.globl _AX5043_MATCH1MAX
                                    841 	.globl _AX5043_MATCH1LEN
                                    842 	.globl _AX5043_MATCH0PAT3
                                    843 	.globl _AX5043_MATCH0PAT2
                                    844 	.globl _AX5043_MATCH0PAT1
                                    845 	.globl _AX5043_MATCH0PAT0
                                    846 	.globl _AX5043_MATCH0MIN
                                    847 	.globl _AX5043_MATCH0MAX
                                    848 	.globl _AX5043_MATCH0LEN
                                    849 	.globl _AX5043_LPOSCSTATUS
                                    850 	.globl _AX5043_LPOSCREF1
                                    851 	.globl _AX5043_LPOSCREF0
                                    852 	.globl _AX5043_LPOSCPER1
                                    853 	.globl _AX5043_LPOSCPER0
                                    854 	.globl _AX5043_LPOSCKFILT1
                                    855 	.globl _AX5043_LPOSCKFILT0
                                    856 	.globl _AX5043_LPOSCFREQ1
                                    857 	.globl _AX5043_LPOSCFREQ0
                                    858 	.globl _AX5043_LPOSCCONFIG
                                    859 	.globl _AX5043_IRQREQUEST1
                                    860 	.globl _AX5043_IRQREQUEST0
                                    861 	.globl _AX5043_IRQMASK1
                                    862 	.globl _AX5043_IRQMASK0
                                    863 	.globl _AX5043_IRQINVERSION1
                                    864 	.globl _AX5043_IRQINVERSION0
                                    865 	.globl _AX5043_IFFREQ1
                                    866 	.globl _AX5043_IFFREQ0
                                    867 	.globl _AX5043_GPADCPERIOD
                                    868 	.globl _AX5043_GPADCCTRL
                                    869 	.globl _AX5043_GPADC13VALUE1
                                    870 	.globl _AX5043_GPADC13VALUE0
                                    871 	.globl _AX5043_FSKDMIN1
                                    872 	.globl _AX5043_FSKDMIN0
                                    873 	.globl _AX5043_FSKDMAX1
                                    874 	.globl _AX5043_FSKDMAX0
                                    875 	.globl _AX5043_FSKDEV2
                                    876 	.globl _AX5043_FSKDEV1
                                    877 	.globl _AX5043_FSKDEV0
                                    878 	.globl _AX5043_FREQB3
                                    879 	.globl _AX5043_FREQB2
                                    880 	.globl _AX5043_FREQB1
                                    881 	.globl _AX5043_FREQB0
                                    882 	.globl _AX5043_FREQA3
                                    883 	.globl _AX5043_FREQA2
                                    884 	.globl _AX5043_FREQA1
                                    885 	.globl _AX5043_FREQA0
                                    886 	.globl _AX5043_FRAMING
                                    887 	.globl _AX5043_FIFOTHRESH1
                                    888 	.globl _AX5043_FIFOTHRESH0
                                    889 	.globl _AX5043_FIFOSTAT
                                    890 	.globl _AX5043_FIFOFREE1
                                    891 	.globl _AX5043_FIFOFREE0
                                    892 	.globl _AX5043_FIFODATA
                                    893 	.globl _AX5043_FIFOCOUNT1
                                    894 	.globl _AX5043_FIFOCOUNT0
                                    895 	.globl _AX5043_FECSYNC
                                    896 	.globl _AX5043_FECSTATUS
                                    897 	.globl _AX5043_FEC
                                    898 	.globl _AX5043_ENCODING
                                    899 	.globl _AX5043_DIVERSITY
                                    900 	.globl _AX5043_DECIMATION
                                    901 	.globl _AX5043_DACVALUE1
                                    902 	.globl _AX5043_DACVALUE0
                                    903 	.globl _AX5043_DACCONFIG
                                    904 	.globl _AX5043_CRCINIT3
                                    905 	.globl _AX5043_CRCINIT2
                                    906 	.globl _AX5043_CRCINIT1
                                    907 	.globl _AX5043_CRCINIT0
                                    908 	.globl _AX5043_BGNDRSSITHR
                                    909 	.globl _AX5043_BGNDRSSIGAIN
                                    910 	.globl _AX5043_BGNDRSSI
                                    911 	.globl _AX5043_BBTUNE
                                    912 	.globl _AX5043_BBOFFSCAP
                                    913 	.globl _AX5043_AMPLFILTER
                                    914 	.globl _AX5043_AGCCOUNTER
                                    915 	.globl _AX5043_AFSKSPACE1
                                    916 	.globl _AX5043_AFSKSPACE0
                                    917 	.globl _AX5043_AFSKMARK1
                                    918 	.globl _AX5043_AFSKMARK0
                                    919 	.globl _AX5043_AFSKCTRL
                                    920 	.globl _XTALREADY
                                    921 	.globl _XTALOSC
                                    922 	.globl _XTALAMPL
                                    923 	.globl _SILICONREV
                                    924 	.globl _SCRATCH3
                                    925 	.globl _SCRATCH2
                                    926 	.globl _SCRATCH1
                                    927 	.globl _SCRATCH0
                                    928 	.globl _RADIOMUX
                                    929 	.globl _RADIOFSTATADDR
                                    930 	.globl _RADIOFSTATADDR1
                                    931 	.globl _RADIOFSTATADDR0
                                    932 	.globl _RADIOFDATAADDR
                                    933 	.globl _RADIOFDATAADDR1
                                    934 	.globl _RADIOFDATAADDR0
                                    935 	.globl _OSCRUN
                                    936 	.globl _OSCREADY
                                    937 	.globl _OSCFORCERUN
                                    938 	.globl _OSCCALIB
                                    939 	.globl _MISCCTRL
                                    940 	.globl _LPXOSCGM
                                    941 	.globl _LPOSCREF
                                    942 	.globl _LPOSCREF1
                                    943 	.globl _LPOSCREF0
                                    944 	.globl _LPOSCPER
                                    945 	.globl _LPOSCPER1
                                    946 	.globl _LPOSCPER0
                                    947 	.globl _LPOSCKFILT
                                    948 	.globl _LPOSCKFILT1
                                    949 	.globl _LPOSCKFILT0
                                    950 	.globl _LPOSCFREQ
                                    951 	.globl _LPOSCFREQ1
                                    952 	.globl _LPOSCFREQ0
                                    953 	.globl _LPOSCCONFIG
                                    954 	.globl _PINSEL
                                    955 	.globl _PINCHGC
                                    956 	.globl _PINCHGB
                                    957 	.globl _PINCHGA
                                    958 	.globl _PALTRADIO
                                    959 	.globl _PALTC
                                    960 	.globl _PALTB
                                    961 	.globl _PALTA
                                    962 	.globl _INTCHGC
                                    963 	.globl _INTCHGB
                                    964 	.globl _INTCHGA
                                    965 	.globl _EXTIRQ
                                    966 	.globl _GPIOENABLE
                                    967 	.globl _ANALOGA
                                    968 	.globl _FRCOSCREF
                                    969 	.globl _FRCOSCREF1
                                    970 	.globl _FRCOSCREF0
                                    971 	.globl _FRCOSCPER
                                    972 	.globl _FRCOSCPER1
                                    973 	.globl _FRCOSCPER0
                                    974 	.globl _FRCOSCKFILT
                                    975 	.globl _FRCOSCKFILT1
                                    976 	.globl _FRCOSCKFILT0
                                    977 	.globl _FRCOSCFREQ
                                    978 	.globl _FRCOSCFREQ1
                                    979 	.globl _FRCOSCFREQ0
                                    980 	.globl _FRCOSCCTRL
                                    981 	.globl _FRCOSCCONFIG
                                    982 	.globl _DMA1CONFIG
                                    983 	.globl _DMA1ADDR
                                    984 	.globl _DMA1ADDR1
                                    985 	.globl _DMA1ADDR0
                                    986 	.globl _DMA0CONFIG
                                    987 	.globl _DMA0ADDR
                                    988 	.globl _DMA0ADDR1
                                    989 	.globl _DMA0ADDR0
                                    990 	.globl _ADCTUNE2
                                    991 	.globl _ADCTUNE1
                                    992 	.globl _ADCTUNE0
                                    993 	.globl _ADCCH3VAL
                                    994 	.globl _ADCCH3VAL1
                                    995 	.globl _ADCCH3VAL0
                                    996 	.globl _ADCCH2VAL
                                    997 	.globl _ADCCH2VAL1
                                    998 	.globl _ADCCH2VAL0
                                    999 	.globl _ADCCH1VAL
                                   1000 	.globl _ADCCH1VAL1
                                   1001 	.globl _ADCCH1VAL0
                                   1002 	.globl _ADCCH0VAL
                                   1003 	.globl _ADCCH0VAL1
                                   1004 	.globl _ADCCH0VAL0
                                   1005 	.globl _axradio_transmit_PARM_3
                                   1006 	.globl _axradio_transmit_PARM_2
                                   1007 	.globl _aligned_alloc_PARM_2
                                   1008 	.globl _axradio_trxstate
                                   1009 	.globl _axradio_mode
                                   1010 	.globl _axradio_conv_time_totimer0
                                   1011 	.globl _axradio_isr
                                   1012 	.globl _ax5043_receiver_on_continuous
                                   1013 	.globl _ax5043_receiver_on_wor
                                   1014 	.globl _ax5043_prepare_tx
                                   1015 	.globl _ax5043_off
                                   1016 	.globl _ax5043_off_xtal
                                   1017 	.globl _axradio_wait_for_xtal
                                   1018 	.globl _axradio_init
                                   1019 	.globl _axradio_cansleep
                                   1020 	.globl _axradio_set_mode
                                   1021 	.globl _axradio_get_mode
                                   1022 	.globl _axradio_set_channel
                                   1023 	.globl _axradio_get_channel
                                   1024 	.globl _axradio_get_pllrange
                                   1025 	.globl _axradio_get_pllvcoi
                                   1026 	.globl _axradio_set_freqoffset
                                   1027 	.globl _axradio_get_freqoffset
                                   1028 	.globl _axradio_set_local_address
                                   1029 	.globl _axradio_get_local_address
                                   1030 	.globl _axradio_set_default_remote_address
                                   1031 	.globl _axradio_get_default_remote_address
                                   1032 	.globl _axradio_transmit
                                   1033 	.globl _axradio_agc_freeze
                                   1034 	.globl _axradio_agc_thaw
                                   1035 	.globl _axradio_calibrate_lposc
                                   1036 	.globl _axradio_commsleepexit
                                   1037 	.globl _axradio_check_fourfsk_modulation
                                   1038 	.globl _axradio_get_transmitter_pa_type
                                   1039 ;--------------------------------------------------------
                                   1040 ; special function registers
                                   1041 ;--------------------------------------------------------
                                   1042 	.area RSEG    (ABS,DATA)
      000000                       1043 	.org 0x0000
                           0000E0  1044 G$ACC$0$0 == 0x00e0
                           0000E0  1045 _ACC	=	0x00e0
                           0000F0  1046 G$B$0$0 == 0x00f0
                           0000F0  1047 _B	=	0x00f0
                           000083  1048 G$DPH$0$0 == 0x0083
                           000083  1049 _DPH	=	0x0083
                           000085  1050 G$DPH1$0$0 == 0x0085
                           000085  1051 _DPH1	=	0x0085
                           000082  1052 G$DPL$0$0 == 0x0082
                           000082  1053 _DPL	=	0x0082
                           000084  1054 G$DPL1$0$0 == 0x0084
                           000084  1055 _DPL1	=	0x0084
                           008382  1056 G$DPTR0$0$0 == 0x8382
                           008382  1057 _DPTR0	=	0x8382
                           008584  1058 G$DPTR1$0$0 == 0x8584
                           008584  1059 _DPTR1	=	0x8584
                           000086  1060 G$DPS$0$0 == 0x0086
                           000086  1061 _DPS	=	0x0086
                           0000A0  1062 G$E2IE$0$0 == 0x00a0
                           0000A0  1063 _E2IE	=	0x00a0
                           0000C0  1064 G$E2IP$0$0 == 0x00c0
                           0000C0  1065 _E2IP	=	0x00c0
                           000098  1066 G$EIE$0$0 == 0x0098
                           000098  1067 _EIE	=	0x0098
                           0000B0  1068 G$EIP$0$0 == 0x00b0
                           0000B0  1069 _EIP	=	0x00b0
                           0000A8  1070 G$IE$0$0 == 0x00a8
                           0000A8  1071 _IE	=	0x00a8
                           0000B8  1072 G$IP$0$0 == 0x00b8
                           0000B8  1073 _IP	=	0x00b8
                           000087  1074 G$PCON$0$0 == 0x0087
                           000087  1075 _PCON	=	0x0087
                           0000D0  1076 G$PSW$0$0 == 0x00d0
                           0000D0  1077 _PSW	=	0x00d0
                           000081  1078 G$SP$0$0 == 0x0081
                           000081  1079 _SP	=	0x0081
                           0000D9  1080 G$XPAGE$0$0 == 0x00d9
                           0000D9  1081 _XPAGE	=	0x00d9
                           0000D9  1082 G$_XPAGE$0$0 == 0x00d9
                           0000D9  1083 __XPAGE	=	0x00d9
                           0000CA  1084 G$ADCCH0CONFIG$0$0 == 0x00ca
                           0000CA  1085 _ADCCH0CONFIG	=	0x00ca
                           0000CB  1086 G$ADCCH1CONFIG$0$0 == 0x00cb
                           0000CB  1087 _ADCCH1CONFIG	=	0x00cb
                           0000D2  1088 G$ADCCH2CONFIG$0$0 == 0x00d2
                           0000D2  1089 _ADCCH2CONFIG	=	0x00d2
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
                                   1599 	.area BIT_BANK	(REL,OVR,DATA)
      000021                       1600 bits:
      000021                       1601 	.ds 1
                           008000  1602 	b0 = bits[0]
                           008100  1603 	b1 = bits[1]
                           008200  1604 	b2 = bits[2]
                           008300  1605 	b3 = bits[3]
                           008400  1606 	b4 = bits[4]
                           008500  1607 	b5 = bits[5]
                           008600  1608 	b6 = bits[6]
                           008700  1609 	b7 = bits[7]
                                   1610 ;--------------------------------------------------------
                                   1611 ; internal ram data
                                   1612 ;--------------------------------------------------------
                                   1613 	.area DSEG    (DATA)
                           000000  1614 G$axradio_mode$0$0==.
      000008                       1615 _axradio_mode::
      000008                       1616 	.ds 1
                           000001  1617 G$axradio_trxstate$0$0==.
      000009                       1618 _axradio_trxstate::
      000009                       1619 	.ds 1
                           000002  1620 Leasyax5043.aligned_alloc$size$1$210==.
      00000A                       1621 _aligned_alloc_PARM_2:
      00000A                       1622 	.ds 2
                           000004  1623 Leasyax5043.axradio_init$i$1$657==.
      00000C                       1624 _axradio_init_i_1_657:
      00000C                       1625 	.ds 1
                           000005  1626 Leasyax5043.axradio_init$vcoisave$3$687==.
      00000D                       1627 _axradio_init_vcoisave_3_687:
      00000D                       1628 	.ds 1
                           000006  1629 Leasyax5043.axradio_init$j$3$687==.
      00000E                       1630 _axradio_init_j_3_687:
      00000E                       1631 	.ds 1
                           000007  1632 Leasyax5043.axradio_init$f$5$690==.
      00000F                       1633 _axradio_init_f_5_690:
      00000F                       1634 	.ds 4
                           00000B  1635 Leasyax5043.axradio_init$sloc0$1$0==.
      000013                       1636 _axradio_init_sloc0_1_0:
      000013                       1637 	.ds 2
                           00000D  1638 Leasyax5043.axradio_transmit$pkt$1$806==.
      000015                       1639 _axradio_transmit_PARM_2:
      000015                       1640 	.ds 3
                           000010  1641 Leasyax5043.axradio_transmit$pktlen$1$806==.
      000018                       1642 _axradio_transmit_PARM_3:
      000018                       1643 	.ds 2
                                   1644 ;--------------------------------------------------------
                                   1645 ; overlayable items in internal ram 
                                   1646 ;--------------------------------------------------------
                                   1647 	.area	OSEG    (OVR,DATA)
                                   1648 	.area	OSEG    (OVR,DATA)
                           000000  1649 Leasyax5043.axradio_set_channel$rng$1$766==.
      00002F                       1650 _axradio_set_channel_rng_1_766:
      00002F                       1651 	.ds 1
                                   1652 	.area	OSEG    (OVR,DATA)
                                   1653 	.area	OSEG    (OVR,DATA)
                                   1654 ;--------------------------------------------------------
                                   1655 ; indirectly addressable internal ram data
                                   1656 ;--------------------------------------------------------
                                   1657 	.area ISEG    (DATA)
                                   1658 ;--------------------------------------------------------
                                   1659 ; absolute internal ram data
                                   1660 ;--------------------------------------------------------
                                   1661 	.area IABS    (ABS,DATA)
                                   1662 	.area IABS    (ABS,DATA)
                                   1663 ;--------------------------------------------------------
                                   1664 ; bit data
                                   1665 ;--------------------------------------------------------
                                   1666 	.area BSEG    (BIT)
                           000000  1667 Leasyax5043.axradio_timer_callback$sloc0$1$0==.
      000000                       1668 _axradio_timer_callback_sloc0_1_0:
      000000                       1669 	.ds 1
                                   1670 ;--------------------------------------------------------
                                   1671 ; paged external ram data
                                   1672 ;--------------------------------------------------------
                                   1673 	.area PSEG    (PAG,XDATA)
                                   1674 ;--------------------------------------------------------
                                   1675 ; external ram data
                                   1676 ;--------------------------------------------------------
                                   1677 	.area XSEG    (XDATA)
                           007020  1678 G$ADCCH0VAL0$0$0 == 0x7020
                           007020  1679 _ADCCH0VAL0	=	0x7020
                           007021  1680 G$ADCCH0VAL1$0$0 == 0x7021
                           007021  1681 _ADCCH0VAL1	=	0x7021
                           007020  1682 G$ADCCH0VAL$0$0 == 0x7020
                           007020  1683 _ADCCH0VAL	=	0x7020
                           007022  1684 G$ADCCH1VAL0$0$0 == 0x7022
                           007022  1685 _ADCCH1VAL0	=	0x7022
                           007023  1686 G$ADCCH1VAL1$0$0 == 0x7023
                           007023  1687 _ADCCH1VAL1	=	0x7023
                           007022  1688 G$ADCCH1VAL$0$0 == 0x7022
                           007022  1689 _ADCCH1VAL	=	0x7022
                           007024  1690 G$ADCCH2VAL0$0$0 == 0x7024
                           007024  1691 _ADCCH2VAL0	=	0x7024
                           007025  1692 G$ADCCH2VAL1$0$0 == 0x7025
                           007025  1693 _ADCCH2VAL1	=	0x7025
                           007024  1694 G$ADCCH2VAL$0$0 == 0x7024
                           007024  1695 _ADCCH2VAL	=	0x7024
                           007026  1696 G$ADCCH3VAL0$0$0 == 0x7026
                           007026  1697 _ADCCH3VAL0	=	0x7026
                           007027  1698 G$ADCCH3VAL1$0$0 == 0x7027
                           007027  1699 _ADCCH3VAL1	=	0x7027
                           007026  1700 G$ADCCH3VAL$0$0 == 0x7026
                           007026  1701 _ADCCH3VAL	=	0x7026
                           007028  1702 G$ADCTUNE0$0$0 == 0x7028
                           007028  1703 _ADCTUNE0	=	0x7028
                           007029  1704 G$ADCTUNE1$0$0 == 0x7029
                           007029  1705 _ADCTUNE1	=	0x7029
                           00702A  1706 G$ADCTUNE2$0$0 == 0x702a
                           00702A  1707 _ADCTUNE2	=	0x702a
                           007010  1708 G$DMA0ADDR0$0$0 == 0x7010
                           007010  1709 _DMA0ADDR0	=	0x7010
                           007011  1710 G$DMA0ADDR1$0$0 == 0x7011
                           007011  1711 _DMA0ADDR1	=	0x7011
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
                           004100  1956 G$AX5043_IFFREQ1$0$0 == 0x4100
                           004100  1957 _AX5043_IFFREQ1	=	0x4100
                           00400B  1958 G$AX5043_IRQINVERSION0$0$0 == 0x400b
                           00400B  1959 _AX5043_IRQINVERSION0	=	0x400b
                           00400A  1960 G$AX5043_IRQINVERSION1$0$0 == 0x400a
                           00400A  1961 _AX5043_IRQINVERSION1	=	0x400a
                           004007  1962 G$AX5043_IRQMASK0$0$0 == 0x4007
                           004007  1963 _AX5043_IRQMASK0	=	0x4007
                           004006  1964 G$AX5043_IRQMASK1$0$0 == 0x4006
                           004006  1965 _AX5043_IRQMASK1	=	0x4006
                           00400D  1966 G$AX5043_IRQREQUEST0$0$0 == 0x400d
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
