oresat/oresat-c3-rf/block-diagrams/L-band-front-end-receiver-v3.0.pdf

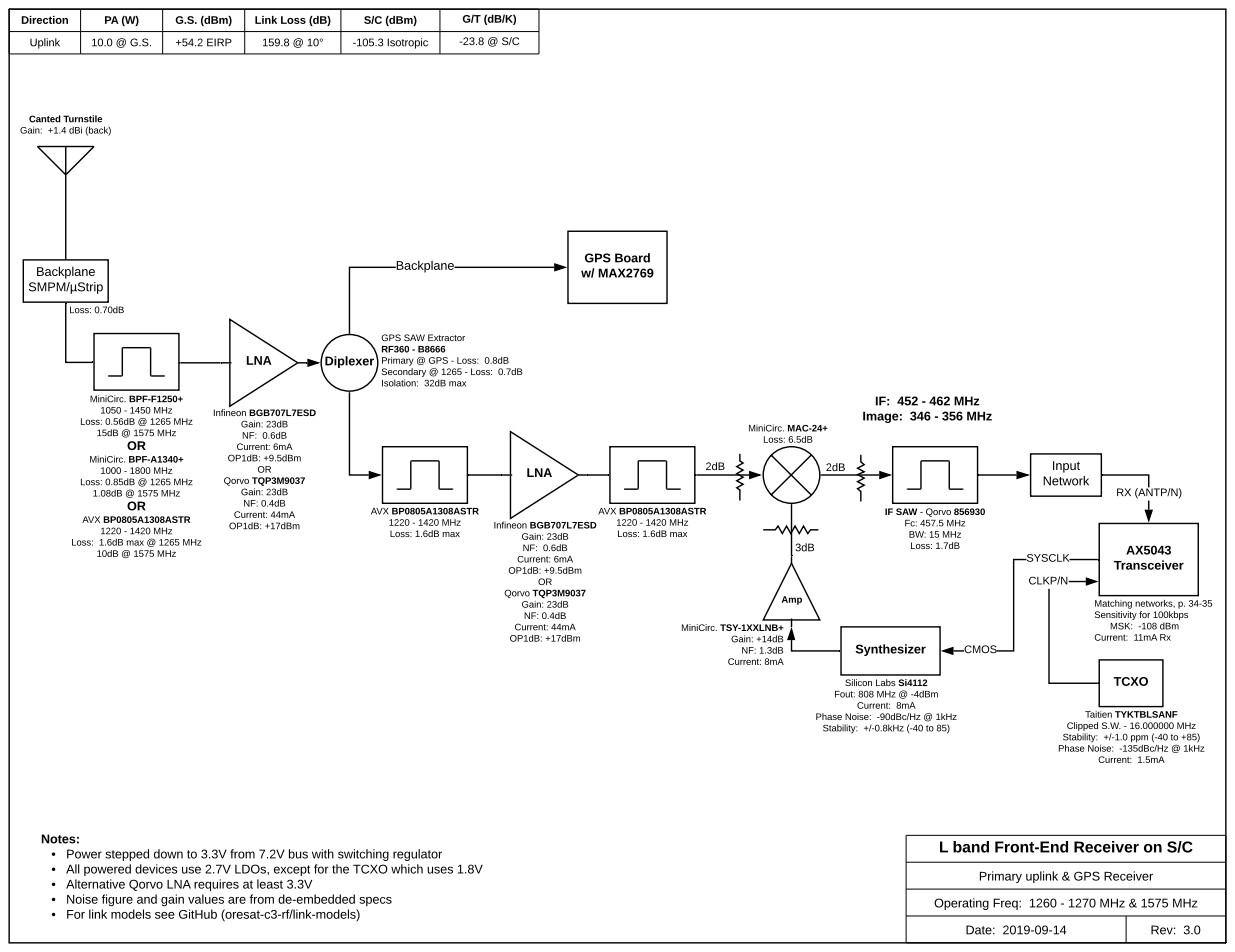
[picture p21: page 1]
Backplane; Synthesizer; Silicon Labs Si4112 Fout: 808 MHz @ -4dBm Current: 8mA; Diplexer; LNA; TCXO; RX (ANTP/N); Amp; MiniCirc. MAC-24+ Loss: 6.5dB; CLKP/N; CMOS; SYSCLK; GPS Board w/ MAX2769; AX5043 Transceiver; MiniCirc. BPF-F1250+ 1050 - 1450 MHz Loss: 0.56dB @ 1265 MHz 15dB @ 1575 MHz OR; MiniCirc. BPF-A1340+ 1000 - 1800 MHz Loss: 0.85dB @ 1265 MHz 1.08dB @ 1575 MHz OR; IF: 452 - 462 MHz Image: 346 - 356 MHz; AVX BP0805A1308ASTR 1220 - 1420 MHz Loss: 1.6dB max; Backplane SMPM/µStrip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

Canted Turnstile Gain: +1.4 dBi (back)

GPS SAW Extractor RF360 - B8666

Primary @ GPS - Loss: 0.8dB
Secondary @ 1265 - Loss: 0.7dB
Isolation: 32dB max

Infineon BGB707L7ESD Gain: 23dB NF: 0.6dB Current: 6mA OP1dB: +9.5dBm

OR Qorvo TQP3M9037 Gain: 23dB NF: 0.4dB Current: 44mA OP1dB: +17dBm

AVX BP0805A1308ASTR
1220 - 1420 MHz
Loss: 1.6dB max @ 1265 MHz
10dB @ 1575 MHz

IF SAW - Qorvo 856930
Fc: 457.5 MHz
BW: 15 MHz
Loss: 1.7dB

Matching networks, p. 34-35
Sensitivity for 100kbps MSK: -108 dBm

MiniCirc. TSY-1XXLNB+ Gain: +14dB NF: 1.3dB Current: 8mA

Phase Noise: -90dBc/Hz @ 1kHz
Stability: +/-0.8kHz (-40 to 85)

Taitien TYKTBLSANF Clipped S.W. - 16.000000 MHz

Stability: +/-1.0 ppm (-40 to +85)
Phase Noise: -135dBc/Hz @ 1kHz Current: 1.5mA

Notes:
- Power stepped down to 3.3V from 7.2V bus with switching regulator
- All powered devices use 2.7V LDOs, except for the TCXO which uses 1.8V
- Alternative Qorvo LNA requires at least 3.3V
- Noise figure and gain values are from de-embedded specs
- For link models see GitHub (oresat-c3-rf/link-models)

L band Front-End Receiver on S/C

Primary uplink & GPS Receiver
Operating Freq: 1260 - 1270 MHz & 1575 MHz
