oresat/oresat-c3-rf/block-diagrams/Archived/70cm-front-end-tranceiver-v2.2.pdf

## Log RF Detector

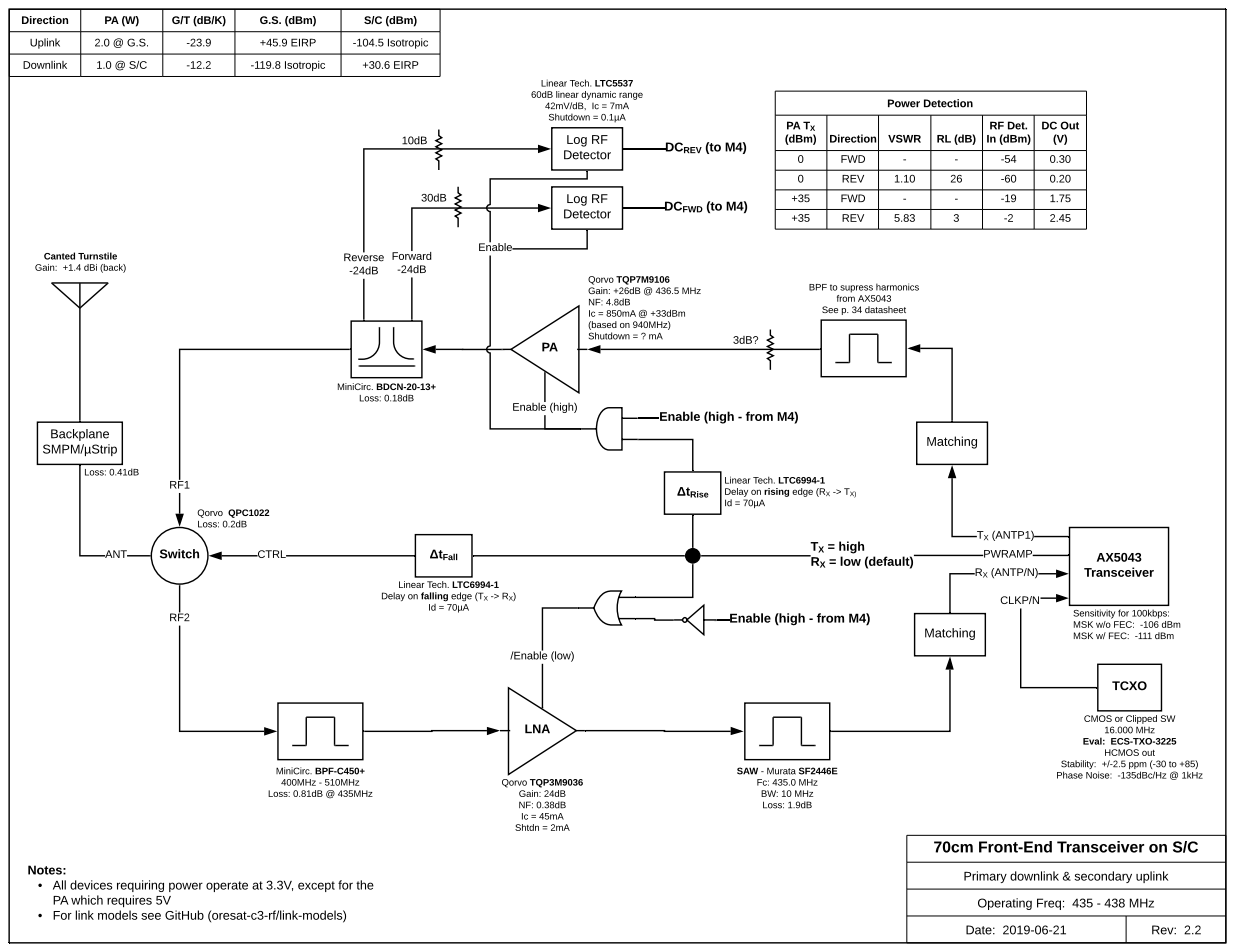
[picture p25: page 1]
ANT; RX (ANTP/N); TX (ANTP1); LNA; Ic = 45mA Shtdn = 2mA; Ic = 850mA @ +33dBm (based on 940MHz) Shutdown = ? mA; TCXO; MiniCirc. BDCN-20-13+ Loss: 0.18dB; Switch; Qorvo QPC1022 Loss: 0.2dB; AX5043 Transceiver; SAW - Murata SF2446E Fc: 435.0 MHz BW: 10 MHz Loss: 1.9dB; MiniCirc. BPF-C450+ 400MHz - 510MHz Loss: 0.81dB @ 435MHz; CLKP/N; Reverse -24dB; DCREV (to M4); ? tRise; CTRL; ? tFall; /Enable (low); Enable (high); Enable (high - from M4); TX = high; RX = low (default); PWRAMP; Log RF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

Direction | PA (W) | G/T (dB/K) | G.S. (dBm) | S/C (dBm)
Uplink | 2.0 @ G.S. | -23.9 | +45.9 EIRP | -104.5 Isotropic
Downlink | 1.0 @ S/C | -12.2 | -119.8 Isotropic | +30.6 EIRP

Linear Tech. LTC5537
60dB linear dynamic range
Shutdown = 0.1µA

0 | REV | 1.10 | 26 | -60 | 0.20
+35 | FWD | - | - | -19 | 1.75

Canted Turnstile Gain: +1.4 dBi (back)

Qorvo TQP7M9106 Gain: +26dB @ 436.5 MHz NF: 4.8dB

BPF to supress harmonics
from AX5043
See p. 34 datasheet

Linear Tech. LTC6994-1 Delay on rising edge (RX -> TX)

Linear Tech. LTC6994-1 Delay on falling edge (TX -> RX)

Enable (high - from M4)

Sensitivity for 100kbps: MSK w/o FEC: -106 dBm

MSK w/ FEC: -111 dBm

CMOS or Clipped SW
16.000 MHz
Eval: ECS-TXO-3225 HCMOS out

Stability: +/-2.5 ppm (-30 to +85)
Phase Noise: -135dBc/Hz @ 1kHz

Qorvo TQP3M9036 Gain: 24dB NF: 0.38dB

70cm Front-End Transceiver on S/C

Notes:
- All devices requiring power operate at 3.3V, except for the
PA which requires 5V
- For link models see GitHub (oresat-c3-rf/link-models)

Primary downlink & secondary uplink
Operating Freq: 435 - 438 MHz
