oresat/oresat-c3-rf/block-diagrams/Archived/70cm-front-end-tranceiver-v2.1.pdf

# 70cm Front-End Transceiver on Satellite

## 435 - 438 MHz (primary downlink & secondary uplink)

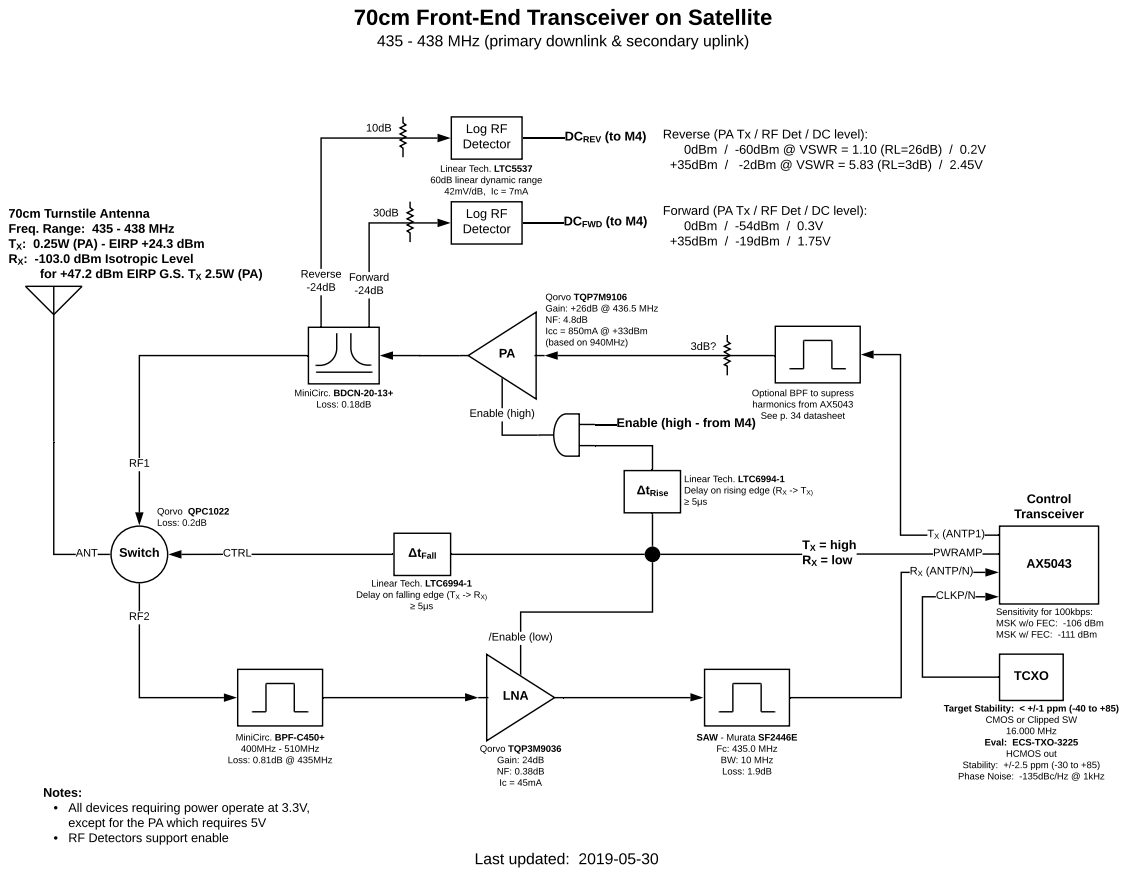
[picture p26: page 1]
ANT; RX (ANTP/N); TX (ANTP1); LNA; Icc = 850mA @ +33dBm (based on 940MHz); Log RF Detector; Last updated: 2019-05-30; TCXO; MiniCirc. BDCN-20-13+ Loss: 0.18dB; Switch; Qorvo QPC1022 Loss: 0.2dB; Control Transceiver; SAW - Murata SF2446E Fc: 435.0 MHz BW: 10 MHz Loss: 1.9dB; MiniCirc. BPF-C450+ 400MHz - 510MHz Loss: 0.81dB @ 435MHz; CLKP/N; Reverse -24dB; DCREV (to M4); ? tRise; CTRL; ? tFall; /Enable (low); Enable (high); Enable (high - from M4); TX = high RX = low; PWRAMP; Detector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

Reverse (PA Tx / RF Det / DC level):
0dBm / -60dBm @ VSWR = 1.10 (RL=26dB) / 0.2V
+35dBm / -2dBm @ VSWR = 5.83 (RL=3dB) / 2.45V

Linear Tech. LTC5537
60dB linear dynamic range
Log RF

70cm Turnstile Antenna
Freq. Range: 435 - 438 MHz
TX: 0.25W (PA) - EIRP +24.3 dBm
RX: -103.0 dBm Isotropic Level
for +47.2 dBm EIRP G.S. TX 2.5W (PA)

Forward (PA Tx / RF Det / DC level):
0dBm / -54dBm / 0.3V
+35dBm / -19dBm / 1.75V

Qorvo TQP7M9106 Gain: +26dB @ 436.5 MHz NF: 4.8dB

Optional BPF to supress
harmonics from AX5043
See p. 34 datasheet

Linear Tech. LTC6994-1 Delay on rising edge (RX -> TX)

Linear Tech. LTC6994-1 Delay on falling edge (TX -> RX)

Sensitivity for 100kbps: MSK w/o FEC: -106 dBm

MSK w/ FEC: -111 dBm

Target Stability: < +/-1 ppm (-40 to +85)

CMOS or Clipped SW
16.000 MHz
Eval: ECS-TXO-3225 HCMOS out

Qorvo TQP3M9036 Gain: 24dB NF: 0.38dB

Stability: +/-2.5 ppm (-30 to +85)
Phase Noise: -135dBc/Hz @ 1kHz

Notes:
- All devices requiring power operate at 3.3V,
except for the PA which requires 5V
- RF Detectors support enable
