oresat/oresat-c3-rf/block-diagrams/Archived/L-band-front-end-receiver-v2.0.pdf

# L Band Front-End Receiver

## 1260 - 1270 MHz (uplink) & 1575 MHz (GPS)

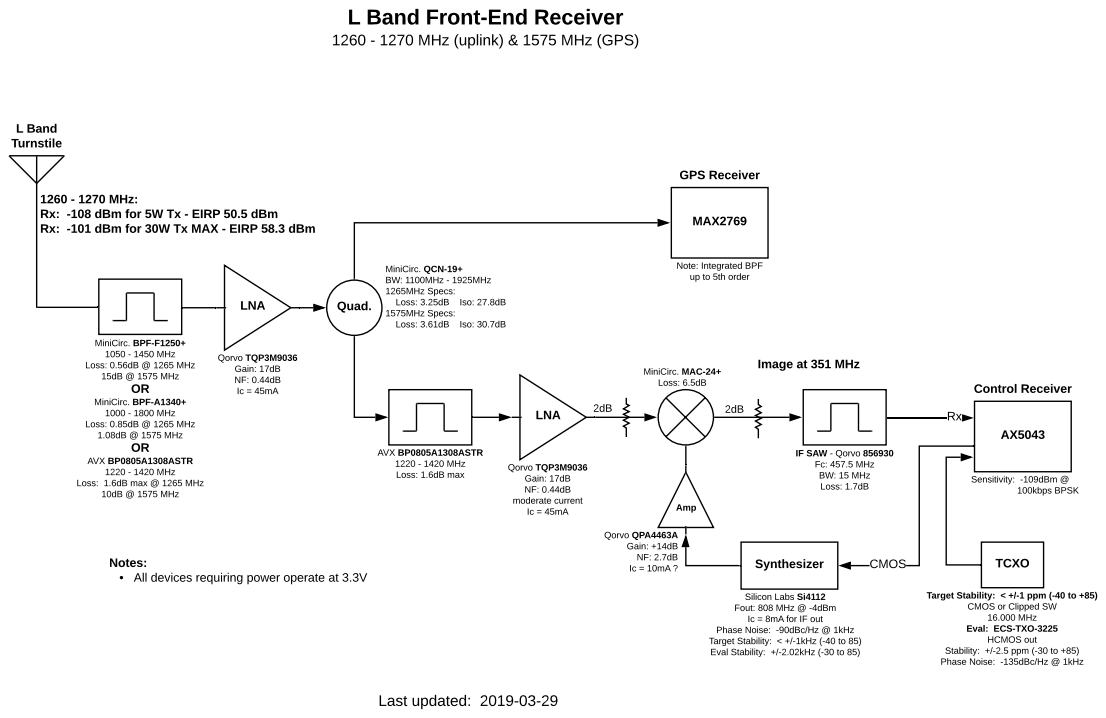
[picture p27: page 1]
Synthesizer; Quad.; MiniCirc. QCN-19+ BW: 1100MHz - 1925MHz 1265MHz Specs: Loss: 3.25dB Iso: 27.8dB 1575MHz Specs: Loss: 3.61dB Iso: 30.7dB; LNA; Qorvo TQP3M9036 Gain: 17dB NF: 0.44dB Ic = 45mA; TCXO; Qorvo QPA4463A Gain: +14dB NF: 2.7dB Ic = 10mA ?; Amp; L Band Turnstile; MiniCirc. MAC-24+ Loss: 6.5dB; Last updated: 2019-03-29; CMOS; MAX2769; GPS Receiver; Control Receiver; Sensitivity: -109dBm @ 100kbps BPSK; MiniCirc. BPF-F1250+ 1050 - 1450 MHz Loss: 0.56dB @ 1265 MHz 15dB @ 1575 MHz OR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

1260 - 1270 MHz:
Rx: -108 dBm for 5W Tx - EIRP 50.5 dBm
Rx: -101 dBm for 30W Tx MAX - EIRP 58.3 dBm

Note: Integrated BPF
up to 5th order

Image at 351 MHz

IF SAW - Qorvo 856930
Fc: 457.5 MHz
BW: 15 MHz
Loss: 1.7dB

AVX BP0805A1308ASTR
1220 - 1420 MHz
Loss: 1.6dB max @ 1265 MHz
10dB @ 1575 MHz

Qorvo TQP3M9036
Gain: 17dB
NF: 0.44dB moderate current

Notes:
- All devices requiring power operate at 3.3V

Silicon Labs Si4112
Fout: 808 MHz @ -4dBm
Ic = 8mA for IF out
Phase Noise: -90dBc/Hz @ 1kHz
Target Stability: < +/-1kHz (-40 to 85)
Eval Stability: +/-2.02kHz (-30 to 85)

Target Stability: < +/-1 ppm (-40 to +85)

CMOS or Clipped SW
16.000 MHz
Eval: ECS-TXO-3225
HCMOS out

Stability: +/-2.5 ppm (-30 to +85)
Phase Noise: -135dBc/Hz @ 1kHz
