oresat/oresat-c3-rf/block-diagrams/Archived/70cm-front-end-tranceiver-v1.0.pdf

# 70cm Front-End Transceiver

## 436.5 MHz (downlink & backup uplink)

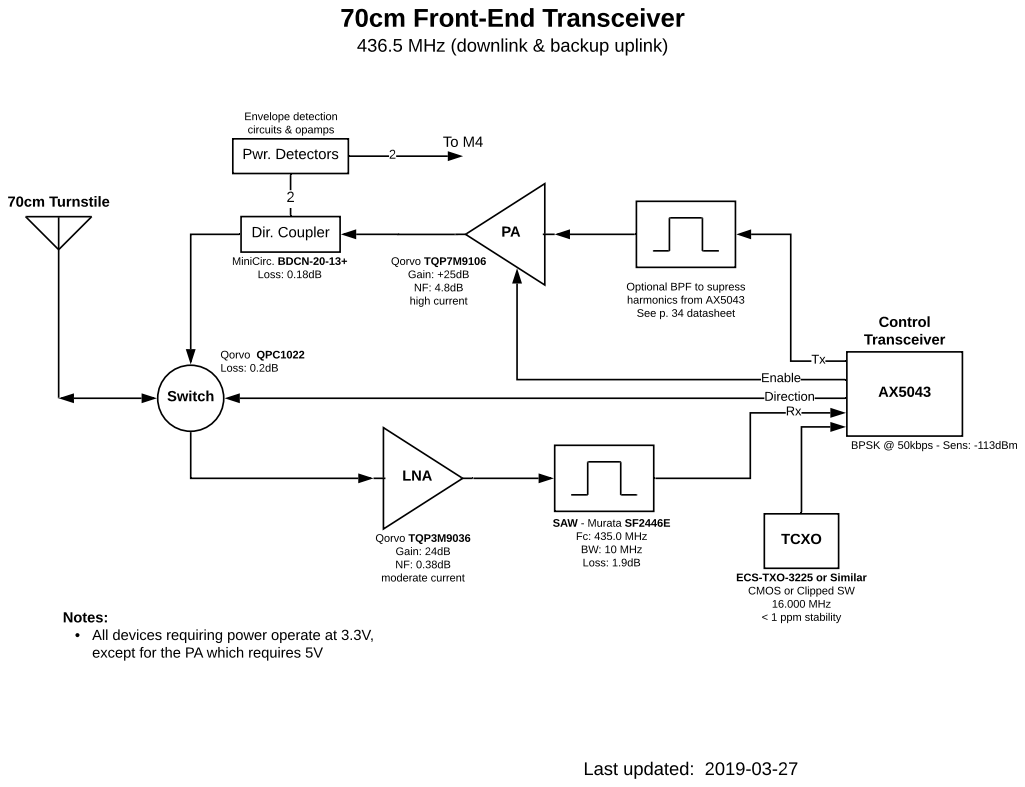
[picture p28: page 1]
70cm Turnstile; Direction; LNA; Qorvo TQP3M9036 Gain: 24dB NF: 0.38dB moderate current; Qorvo TQP7M9106 Gain: +25dB NF: 4.8dB high current; Pwr. Detectors; Envelope detection circuits & opamps; Last updated: 2019-03-27; TCXO; Dir. Coupler; MiniCirc. BDCN-20-13+ Loss: 0.18dB; Switch; Qorvo QPC1022 Loss: 0.2dB; Control Transceiver; BPSK @ 50kbps - Sens: -113dBm; SAW - Murata SF2446E Fc: 435.0 MHz BW: 10 MHz Loss: 1.9dB; Enable

Optional BPF to supress
harmonics from AX5043
See p. 34 datasheet

ECS-TXO-3225 or Similar
CMOS or Clipped SW
16.000 MHz
< 1 ppm stability

Notes:
- All devices requiring power operate at 3.3V,
except for the PA which requires 5V
