oresat/oresat-c3-rf/block-diagrams/Archived/L-band-front-end-receiver-v1.0.pdf

# L Band Front-End Receiver

## 1265 MHz (uplink) & 1575 MHz (GPS)

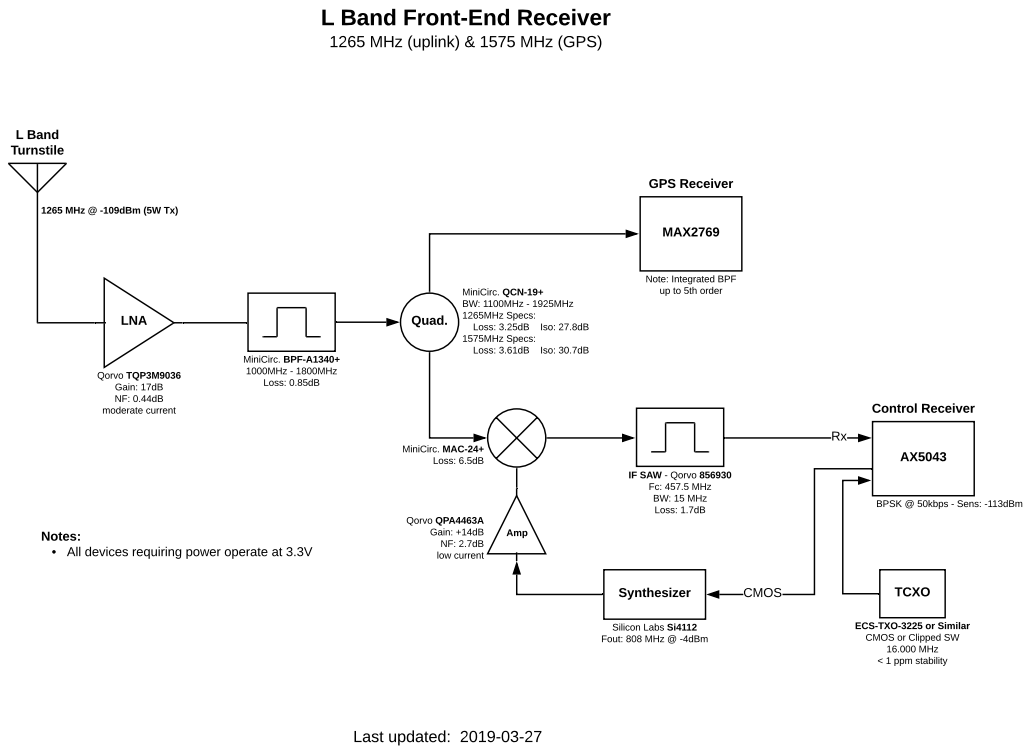
[picture p29: page 1]
MiniCirc. BPF-A1340+ 1000MHz - 1800MHz Loss: 0.85dB; Synthesizer; Silicon Labs Si4112 Fout: 808 MHz @ -4dBm; Quad.; MiniCirc. QCN-19+ BW: 1100MHz - 1925MHz 1265MHz Specs: Loss: 3.25dB Iso: 27.8dB 1575MHz Specs: Loss: 3.61dB Iso: 30.7dB; LNA; Qorvo TQP3M9036 Gain: 17dB NF: 0.44dB moderate current; TCXO; Qorvo QPA4463A Gain: +14dB NF: 2.7dB low current; Amp; L Band Turnstile; 1265 MHz @-109dBm (5W Tx); MiniCirc. MAC-24+ Loss: 6.5dB; Last updated: 2019-03-27; CMOS; MAX2769; GPS Receiver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

Note: Integrated BPF
up to 5th order

IF SAW - Qorvo 856930
Fc: 457.5 MHz
BW: 15 MHz
Loss: 1.7dB

Notes:
- All devices requiring power operate at 3.3V

ECS-TXO-3225 or Similar
CMOS or Clipped SW
16.000 MHz
< 1 ppm stability
