oresat/oresat-c3-rf/eagle/synthesizer-IF-Si4112.brd

## EAGLE design eagle/synthesizer-IF-Si4112.brd (2019-10-08)

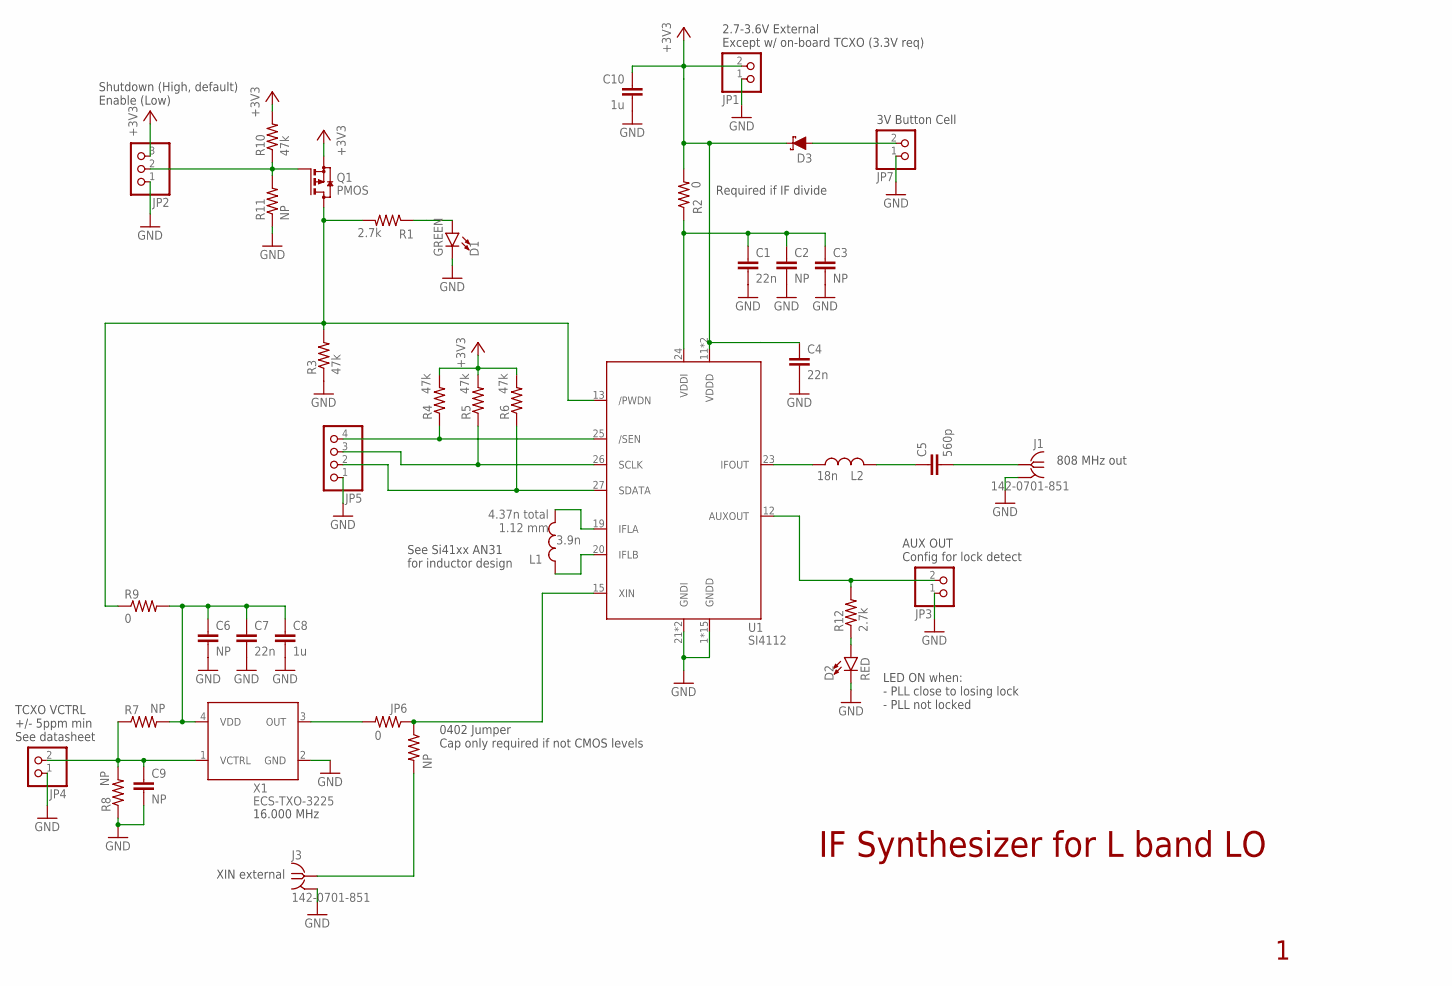
[picture p56: schematic synthesizer-IF-Si4112.sch]

Parts:
C1, C4, C7: 22n; .0603-B-NOSILK
C2, C3, C6, C9: NP; .0603-B-NOSILK
C5: 560p; .0402-B-NOSILK
C8, C10: 1u; .0603-B-NOSILK
D1: GREEN; LED-0603
D2: RED; LED-0603
D3: 120mA/40V/370mV; SOD-523
J1, J3: 142-0701-851
JP1, JP3, JP4, JP7: PINHD-1X2; 1X02
JP2: PINHD-1X3; 1X03
JP5: PINHD-1X4; 1X04
JP6: 0; .0402-B-NOSILK
L1: 3.9n; .0402-C-NOSILK
L2: 18n; .0402-B-NOSILK
Q1: PMOS; SOT23
R1, R12: 2.7k; .0603-B-NOSILK
R2, R9: 0; .0603-B-NOSILK
R3, R4, R5, R6, R10: 47k; .0402-B-NOSILK
R7, R8: NP; .0603-B-NOSILK
R11, R99: NP; .0402-B-NOSILK
U1: SI4112; QFN28-5X5-WITH-CENTER-PAD
X1: ECS-TXO-3225; 3.2X2.5

Connections:
+3V3: C4.1, C10.1, D3.C, JP1.2, JP2.3, Q1.2 (S), R2.2, R4.2, R5.2, R6.2, R10.2, U1.11 (VDDD), U1.17 (VDDD)
/SEN: JP5.4, R4.1, U1.25 (/SEN)
AUX: JP3.2, R12.2, U1.12 (AUXOUT)
GND: C1.2, C2.2, C3.2, C4.2, C6.2, C7.2, C8.2, C9.2, C10.2, D1.C, D2.C, J1.GND1 (GND), J1.GND2 (GND), J1.GND3 (GND), J1.GND4 (GND), J3.GND1 (GND), J3.GND2 (GND), J3.GND3 (GND), J3.GND4 (GND), JP1.1, JP2.1, JP3.1, JP4.1, JP5.1, JP7.1, R3.1, R8.1, R11.1, U1.1 (GNDD), U1.2 (GNDD), U1.3 (GNDD), U1.4 (GNDD), U1.5 (GNDD), U1.6 (GNDD), U1.7 (GNDD), U1.8 (GNDD), U1.9 (GNDD), U1.10 (GNDD), U1.14 (GNDD), U1.16 (GNDD), U1.18 (GNDD), U1.21 (GNDI), U1.22 (GNDI), U1.28 (GNDD), U1.PAD (GNDD), X1.2 (GND)
IF_OUT: C5.2, J1.RF1 (RF)
unnamed: D3.A, JP7.2
unnamed: L1.2, U1.19 (IFLA)
unnamed: L1.1, U1.20 (IFLB)
unnamed: JP2.2, Q1.1 (G), R10.1, R11.2
unnamed: Q1.3 (D), R1.2, R3.2, R9.1, U1.13 (/PWDN)
unnamed: JP6.2, X1.3 (OUT)
unnamed: C6.1, C7.1, C8.1, R7.2, R9.2, X1.4 (VDD)
unnamed: C5.1, L2.2
unnamed: D1.A, R1.1
unnamed: D2.A, R12.1
unnamed: L2.1, U1.23 (IFOUT)
unnamed: C1.1, C2.1, C3.1, R2.1, U1.24 (VDDI)
REF_IN: J3.RF1 (RF), R99.2
SCLK: JP5.3, R5.1, U1.26 (SCLK)
SDATA: JP5.2, R6.1, U1.27 (SDATA)
VCTRL: C9.1, JP4.2, R7.1, R8.2, X1.1 (VCTRL)
XIN: JP6.1, R99.1, U1.15 (XIN)

Notes on the sheet:
IF Synthesizer for L band LO
4.37n total 1.12 mm
Required if IF divide
808 MHz out
XIN external
2.7-3.6V External Except w/ on-board TCXO (3.3V req)
16.000 MHz
0402 Jumper Cap only required if not CMOS levels
Shutdown (High, default) Enable (Low)
TCXO VCTRL +/- 5ppm min See datasheet
AUX OUT Config for lock detect
LED ON when: - PLL close to losing lock - PLL not locked
3V Button Cell
See Si41xx AN31 for inductor design

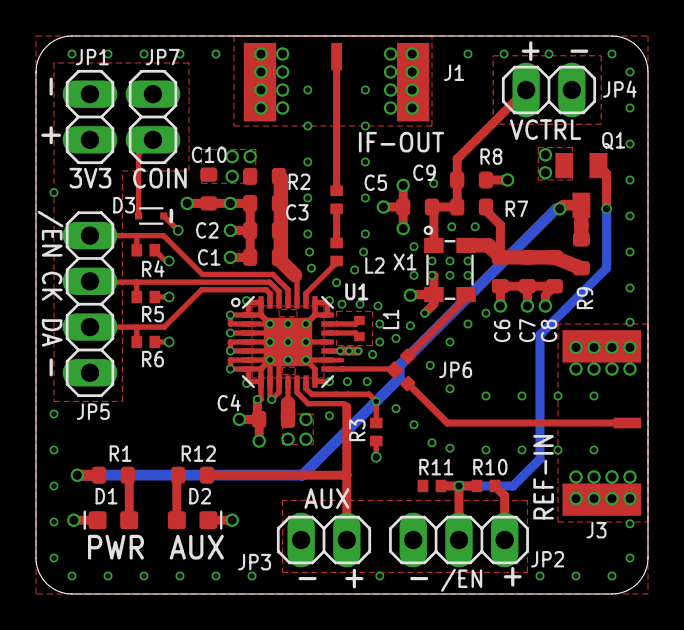
[picture p57: board synthesizer-IF-Si4112.brd from above]

Board: 4 copper layers, 34.0 x 31.0 mm, 40 parts (0 on the bottom side), 22 nets.
