oresat/oresat-c3-rf/eagle/power-switching-TPS6211x.brd

## EAGLE design eagle/power-switching-TPS6211x.brd (2019-09-29)

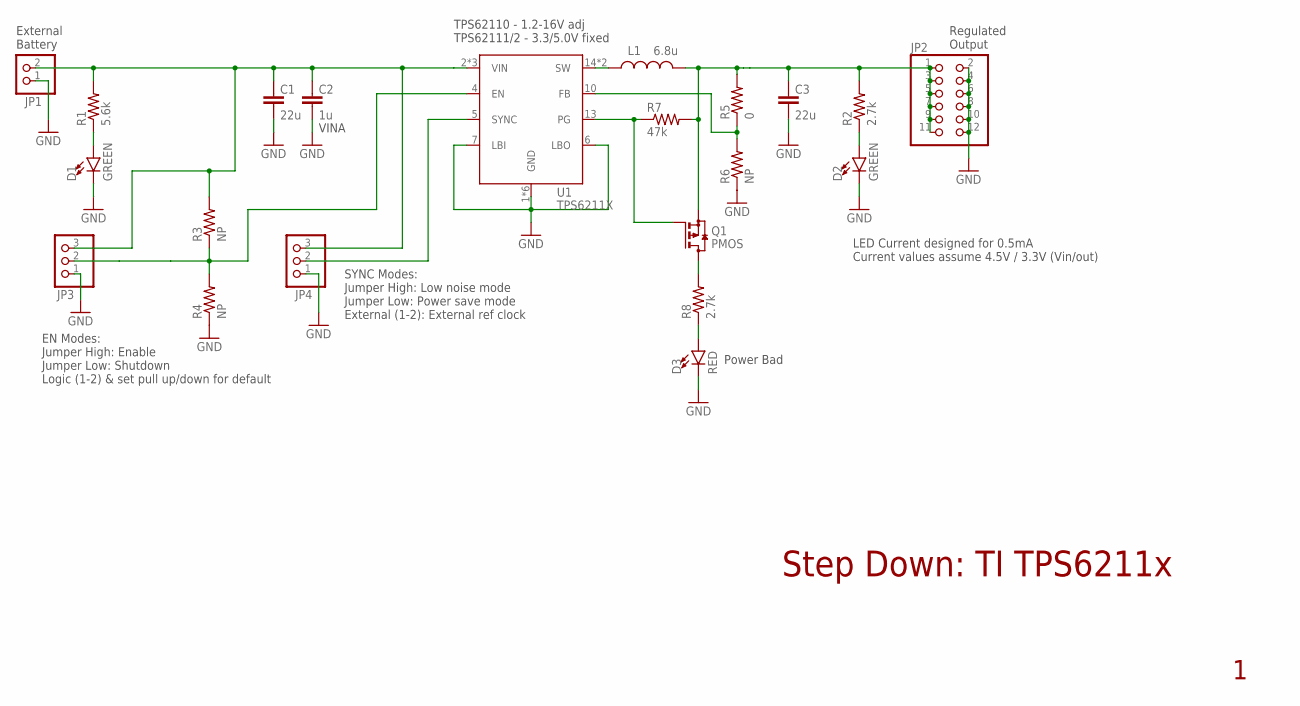
[picture p58: schematic power-switching-TPS6211x.sch]

Parts:
C1, C3: 22u; 1206-B
C2: 1u; .0603-B-NOSILK
D1, D2: GREEN; LED-0603
D3: RED; LED-0603
JP1: PINHD-1X2; 1X02
JP2: PINHD-2X6; 2X06
JP3, JP4: PINHD-1X3; 1X03
L1: 6.8u; ECS-MPI4040; MPN ECS-MPI4040R4-6R8-R
Q1: PMOS; SOT23
R1: 5.6k; .0603-B-NOSILK
R2, R8: 2.7k; .0603-B-NOSILK
R3, R4, R6: NP; .0402-B-NOSILK
R5: 0; .0402-B-NOSILK
R7: 47k; .0402-B-NOSILK
U1: TPS6211X; S-PVQFN-16

Connections:
+VIN: C1.1, C2.1, JP1.2, JP3.3, JP4.3, R1.2, R3.2, U1.2 (VIN), U1.3 (VIN), U1.8 (VIN)
+VOUT: C3.1, JP2.1, JP2.3, JP2.5, JP2.7, JP2.9, JP2.11, L1.2, Q1.2 (S), R2.2, R5.2, R7.2
+VOUT1: Q1.3 (D), R8.2
EN: JP3.2, R3.1, R4.2, U1.4 (EN)
FB: R5.1, R6.2, U1.10 (FB)
GND: C1.2, C2.2, C3.2, D1.C, D2.C, D3.C, JP1.1, JP2.2, JP2.4, JP2.6, JP2.8, JP2.10, JP2.12, JP3.1, JP4.1, R4.1, R6.1, U1.1 (GND), U1.6 (LBO), U1.7 (LBI), U1.9 (GND), U1.11 (GND), U1.12 (GND), U1.16 (GND), U1.PAD (GND)
unnamed: D3.A, R8.1
unnamed: D1.A, R1.1
unnamed: D2.A, R2.1
PG: Q1.1 (G), R7.1, U1.13 (PG)
SW: L1.1, U1.14 (SW), U1.15 (SW)
SYNC: JP4.2, U1.5 (SYNC)

Notes on the sheet:
Step Down: TI TPS6211x
Regulated Output
External Battery
SYNC Modes: Jumper High: Low noise mode Jumper Low: Power save mode External (1-2): External ref clock
EN Modes: Jumper High: Enable Jumper Low: Shutdown Logic (1-2) & set pull up/down for default
Power Bad
LED Current designed for 0.5mA Current values assume 4.5V / 3.3V (Vin/out)
VINA
TPS62110 - 1.2-16V adj TPS62111/2 - 3.3/5.0V fixed

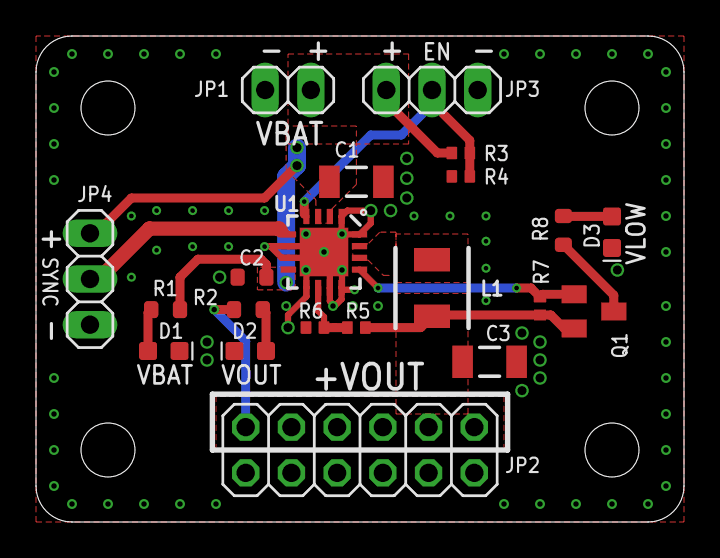
[picture p59: board power-switching-TPS6211x.brd from above]

Board: 2 copper layers, 36.0 x 27.0 mm, 21 parts (0 on the bottom side), 12 nets.
