oresat/oresat-c3-rf/eagle/bpf-L-band-BPF-A1340+.brd

## EAGLE design eagle/bpf-L-band-BPF-A1340+.brd (2019-09-29)

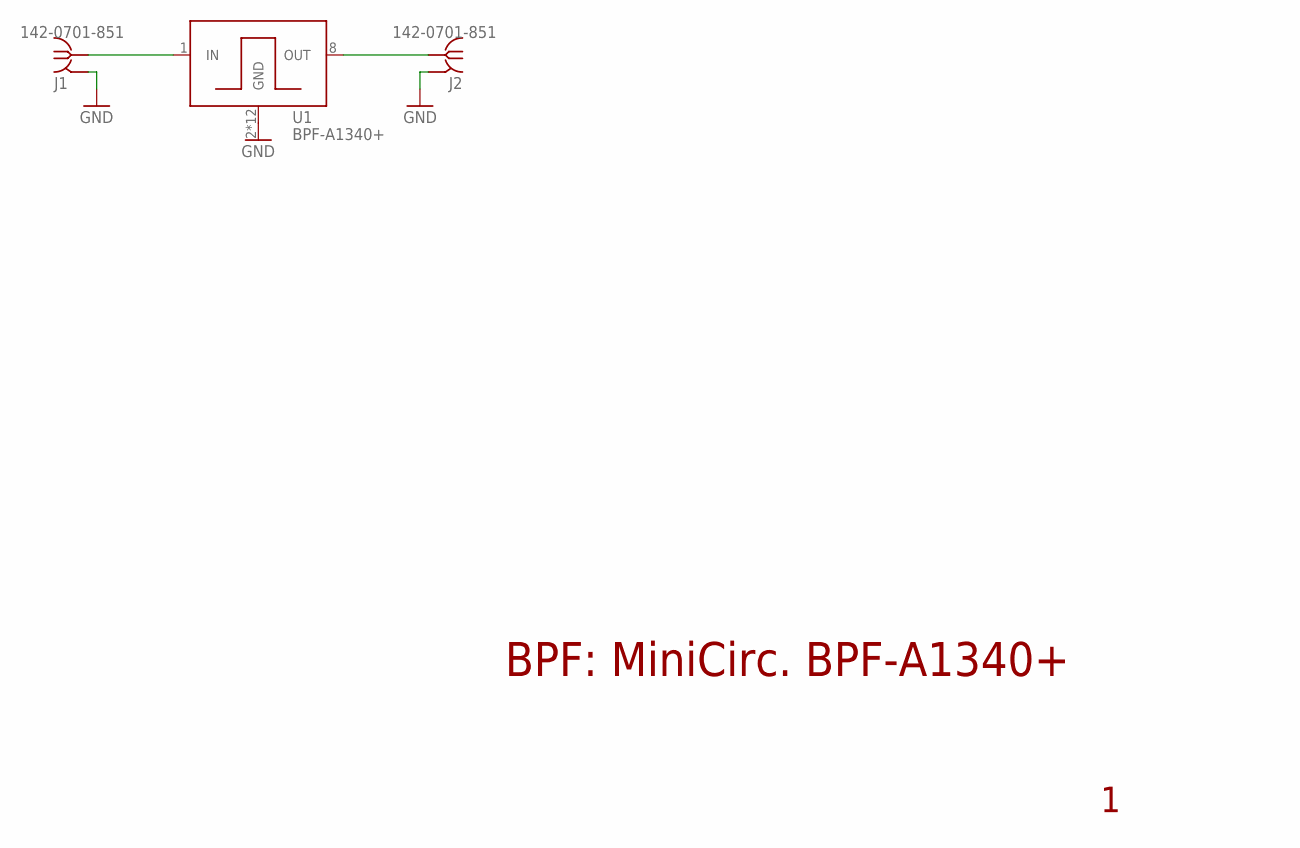
[picture p62: schematic bpf-L-band-BPF-A1340+.sch]

Parts:
J1, J2: 142-0701-851
U1: BPF-A1340+

Connections:
GND: J1.GND1 (GND), J1.GND2 (GND), J1.GND3 (GND), J1.GND4 (GND), J2.GND1 (GND), J2.GND2 (GND), J2.GND3 (GND), J2.GND4 (GND), U1.2 (GND), U1.3 (GND), U1.4 (GND), U1.5 (GND), U1.6 (GND), U1.7 (GND), U1.9 (GND), U1.10 (GND), U1.11 (GND), U1.12 (GND), U1.13 (GND), U1.14 (GND)
RF-IN: J1.RF1 (RF), U1.1 (IN)
RF-OUT: J2.RF1 (RF), U1.8 (OUT)

Notes on the sheet:
BPF: MiniCirc. BPF-A1340+

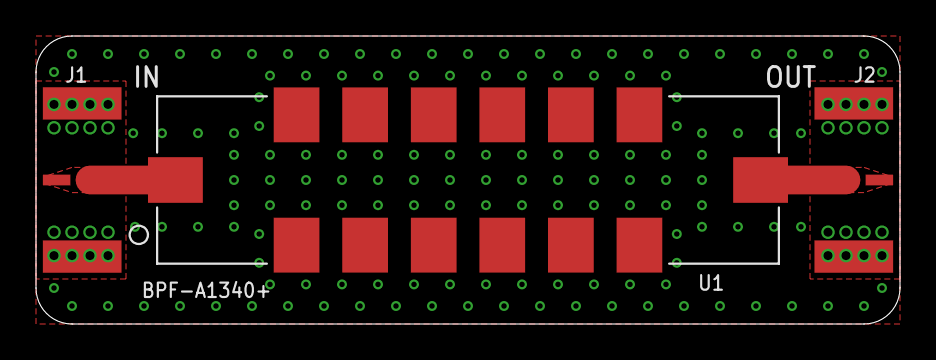
[picture p63: board bpf-L-band-BPF-A1340+.brd from above]

Board: 2 copper layers, 48.0 x 16.0 mm, 3 parts (0 on the bottom side), 3 nets.
