oresat/oresat-c3-rf/eagle/bpf-L-band-BP0805.brd

## EAGLE design eagle/bpf-L-band-BP0805.brd (2019-09-25)

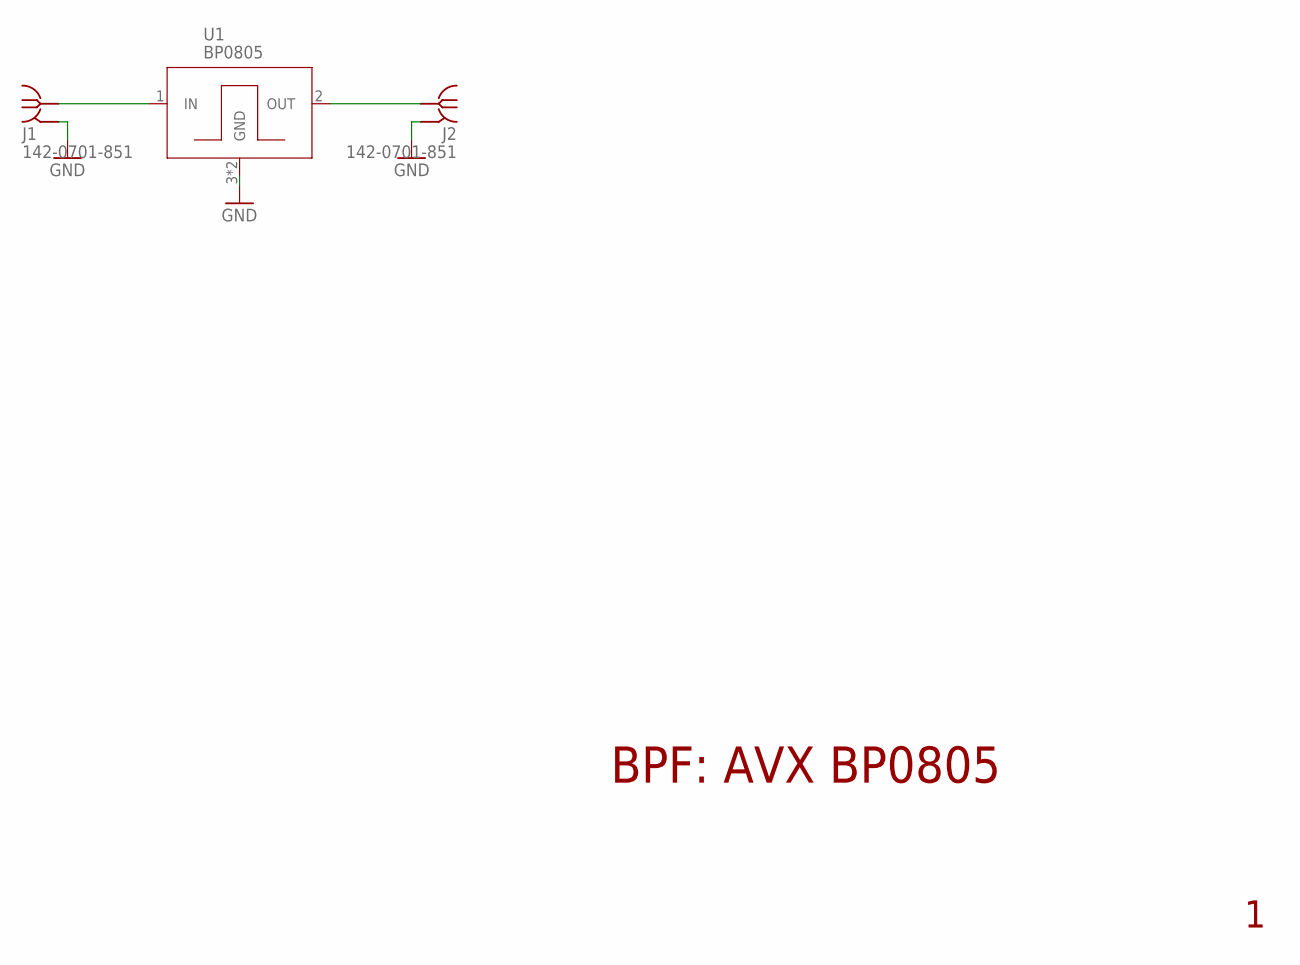
[picture p64: schematic bpf-L-band-BP0805.sch]

Parts:
J1, J2: 142-0701-851
U1: BP0805

Connections:
GND: J1.GND1 (GND), J1.GND2 (GND), J1.GND3 (GND), J1.GND4 (GND), J2.GND1 (GND), J2.GND2 (GND), J2.GND3 (GND), J2.GND4 (GND), U1.3 (GND), U1.4 (GND)
RF-IN: J1.RF1 (RF), U1.1 (IN)
RF-OUT: J2.RF1 (RF), U1.2 (OUT)

Notes on the sheet:
BPF: AVX BP0805

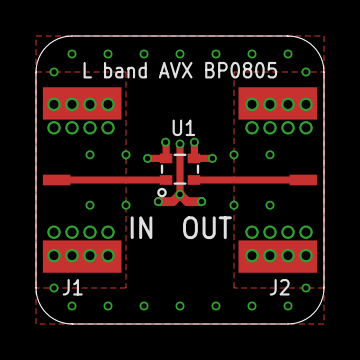
[picture p65: board bpf-L-band-BP0805.brd from above]

Board: 4 copper layers, 16.0 x 16.0 mm, 3 parts (0 on the bottom side), 3 nets.
