oresat/oresat-c3-rf/eagle/diplexer-GPS-RF360-B8666.brd

## EAGLE design eagle/diplexer-GPS-RF360-B8666.brd (2019-09-21)

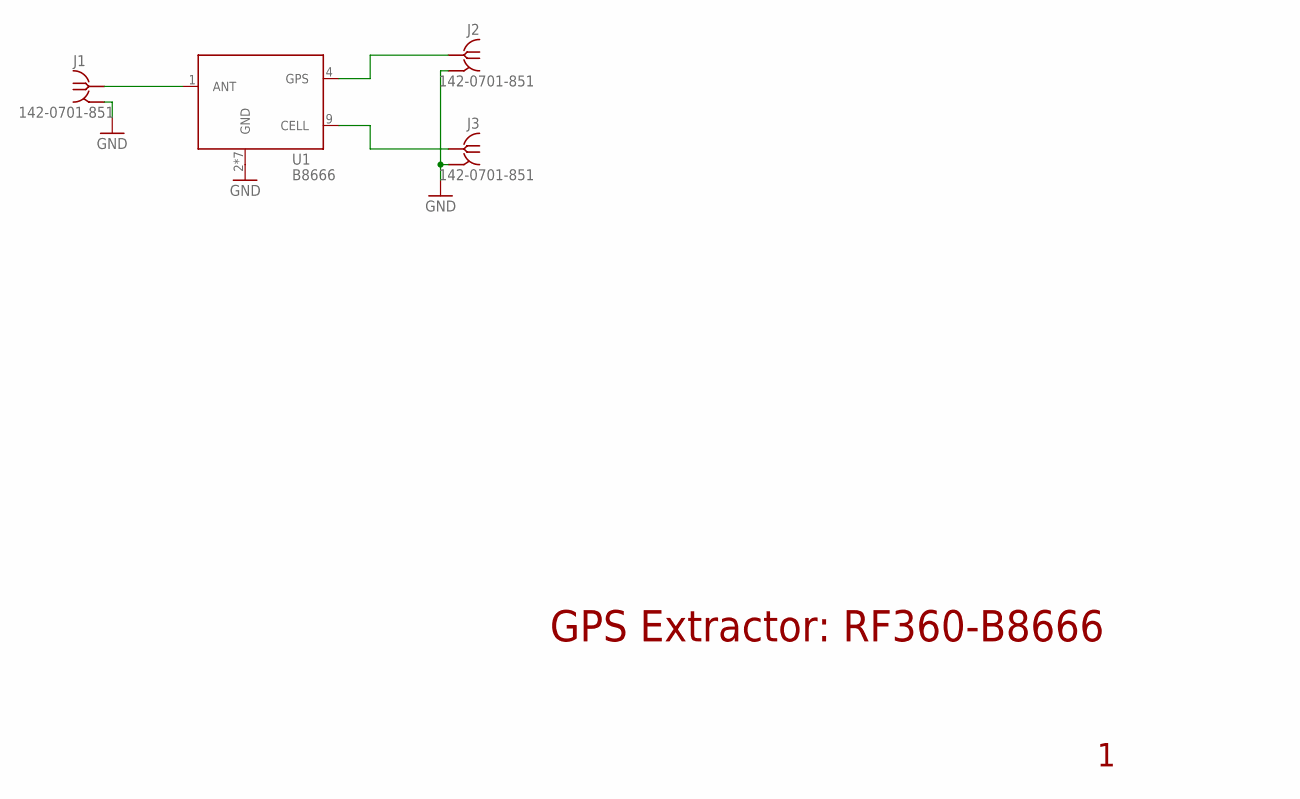
[picture p66: schematic diplexer-GPS-RF360-B8666.sch]

Parts:
J1, J2, J3: 142-0701-851
U1: B8666; 1.7X1.3

Connections:
GND: J1.GND1 (GND), J1.GND2 (GND), J1.GND3 (GND), J1.GND4 (GND), J2.GND1 (GND), J2.GND2 (GND), J2.GND3 (GND), J2.GND4 (GND), J3.GND1 (GND), J3.GND2 (GND), J3.GND3 (GND), J3.GND4 (GND), U1.2 (GND), U1.3 (GND), U1.5 (GND), U1.6 (GND), U1.7 (GND), U1.8 (GND), U1.10 (GND)
GPS: J2.RF1 (RF), U1.4 (GPS)
RF-IN: J1.RF1 (RF), U1.1 (ANT)
RF-OUT: J3.RF1 (RF), U1.9 (CELL)

Notes on the sheet:
GPS Extractor: RF360-B8666

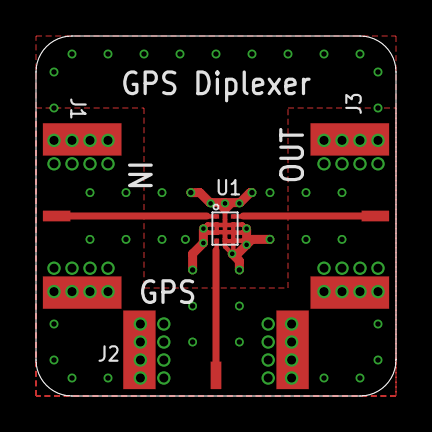
[picture p67: board diplexer-GPS-RF360-B8666.brd from above]

Board: 4 copper layers, 20.0 x 20.0 mm, 4 parts (0 on the bottom side), 4 nets.
