oresat/oresat-c3-rf/eagle/power-linear-LP38692.brd

## EAGLE design eagle/power-linear-LP38692.brd (2019-09-14)

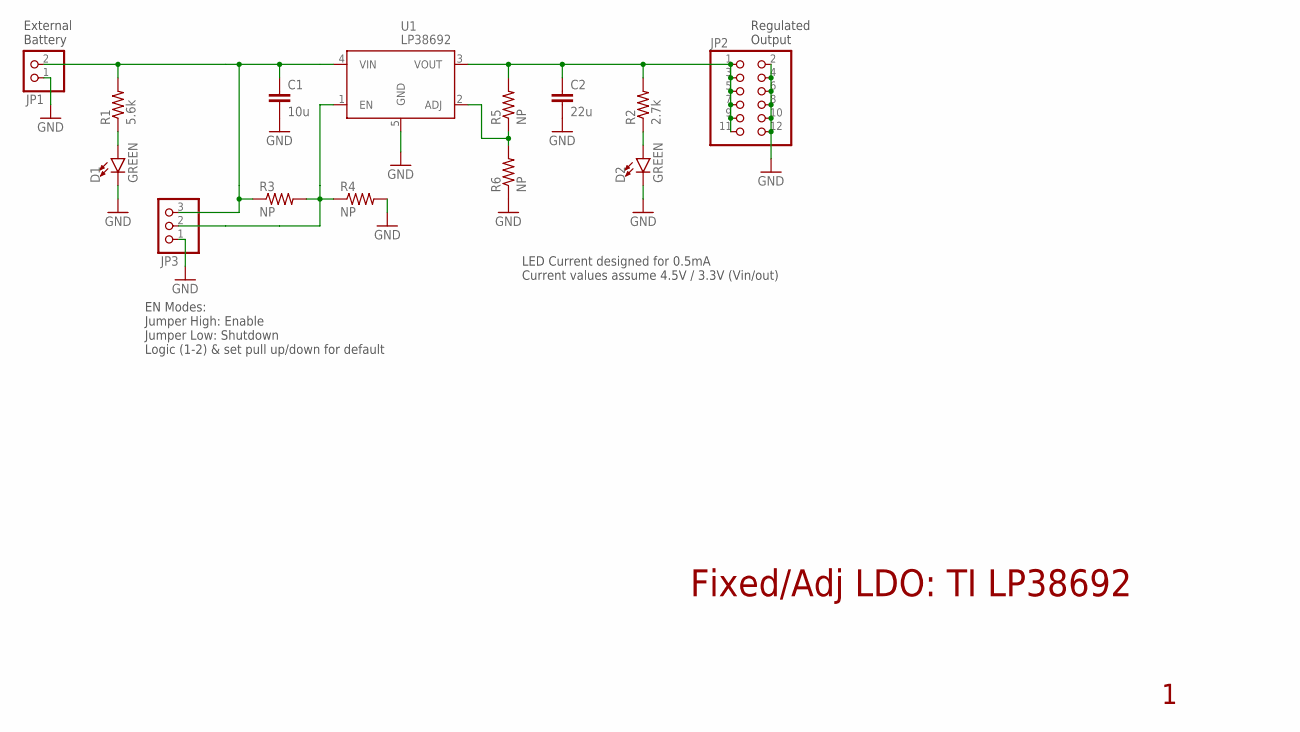
[picture p68: schematic power-linear-LP38692.sch]

Parts:
C1: 10u; .0805-B-NOSILK
C2: 22u; 1206-B
D1, D2: GREEN; LED-0603
JP1: PINHD-1X2; 1X02
JP2: PINHD-2X6; 2X06
JP3: PINHD-1X3; 1X03
R1: 5.6k; .0603-B-NOSILK
R2: 2.7k; .0603-B-NOSILK
R3, R4, R5, R6: NP; .0402-B-NOSILK
U1: LP38692; SOT223-5

Connections:
+VBAT: C1.1, JP1.2, JP3.3, R1.2, R3.1, U1.4 (VIN)
+VOUT: C2.1, JP2.1, JP2.3, JP2.5, JP2.7, JP2.9, JP2.11, R2.2, R5.2, U1.3 (VOUT)
GND: C1.2, C2.2, D1.C, D2.C, JP1.1, JP2.2, JP2.4, JP2.6, JP2.8, JP2.10, JP2.12, JP3.1, R4.2, R6.1, U1.5 (GND)
unnamed: R5.1, R6.2, U1.2 (ADJ)
unnamed: JP3.2, R3.2, R4.1, U1.1 (EN)
unnamed: D1.A, R1.1
unnamed: D2.A, R2.1

Notes on the sheet:
Fixed/Adj LDO: TI LP38692
External Battery
Regulated Output
EN Modes: Jumper High: Enable Jumper Low: Shutdown Logic (1-2) & set pull up/down for default
LED Current designed for 0.5mA Current values assume 4.5V / 3.3V (Vin/out)

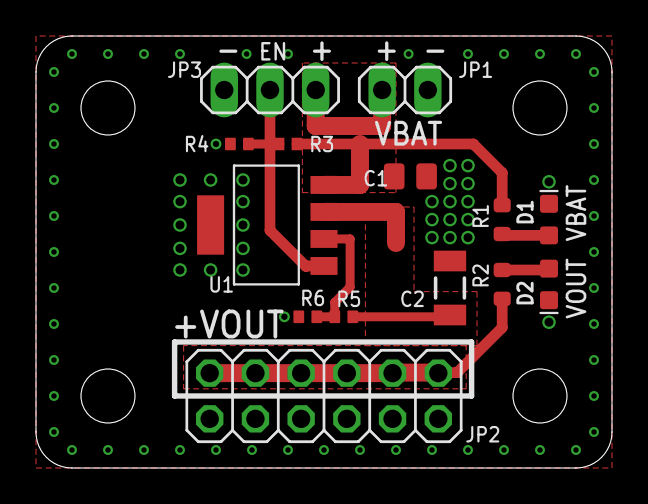
[picture p69: board power-linear-LP38692.brd from above]

Board: 2 copper layers, 32.0 x 24.0 mm, 14 parts (0 on the bottom side), 7 nets.
