oresat/oresat-c3-rf/eagle/bpf-IF-SAW-856930.brd

## EAGLE design eagle/bpf-IF-SAW-856930.brd (2019-09-12)

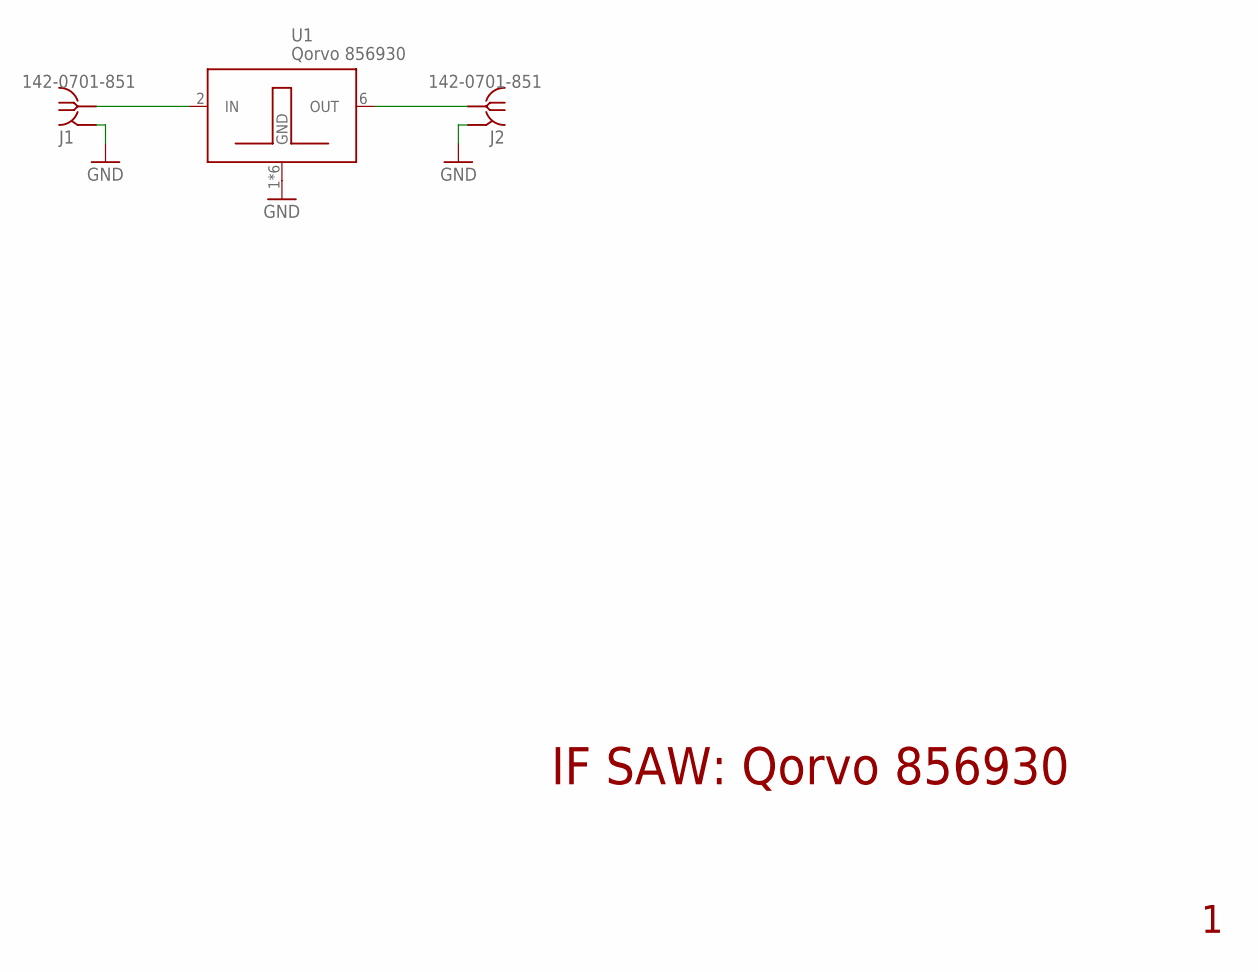
[picture p70: schematic bpf-IF-SAW-856930.sch]

Parts:
J1, J2: 142-0701-851
U1: Qorvo 856930; 3.8X3.8

Connections:
GND: J1.GND1 (GND), J1.GND2 (GND), J1.GND3 (GND), J1.GND4 (GND), J2.GND1 (GND), J2.GND2 (GND), J2.GND3 (GND), J2.GND4 (GND), U1.1 (GND), U1.3 (GND), U1.4 (GND), U1.5 (GND), U1.7 (GND), U1.8 (GND)
unnamed: J1.RF1 (RF), U1.2 (IN)
unnamed: J2.RF1 (RF), U1.6 (OUT)

Notes on the sheet:
IF SAW: Qorvo 856930

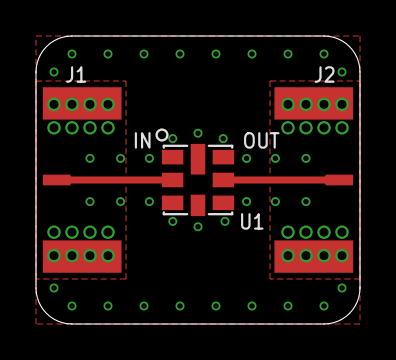
[picture p71: board bpf-IF-SAW-856930.brd from above]

Board: 4 copper layers, 18.0 x 16.0 mm, 3 parts (0 on the bottom side), 3 nets.
