oresat/oresat-c3-rf/eagle/synthesizer-RF-Si4123.brd

## EAGLE design eagle/synthesizer-RF-Si4123.brd (2019-09-12)

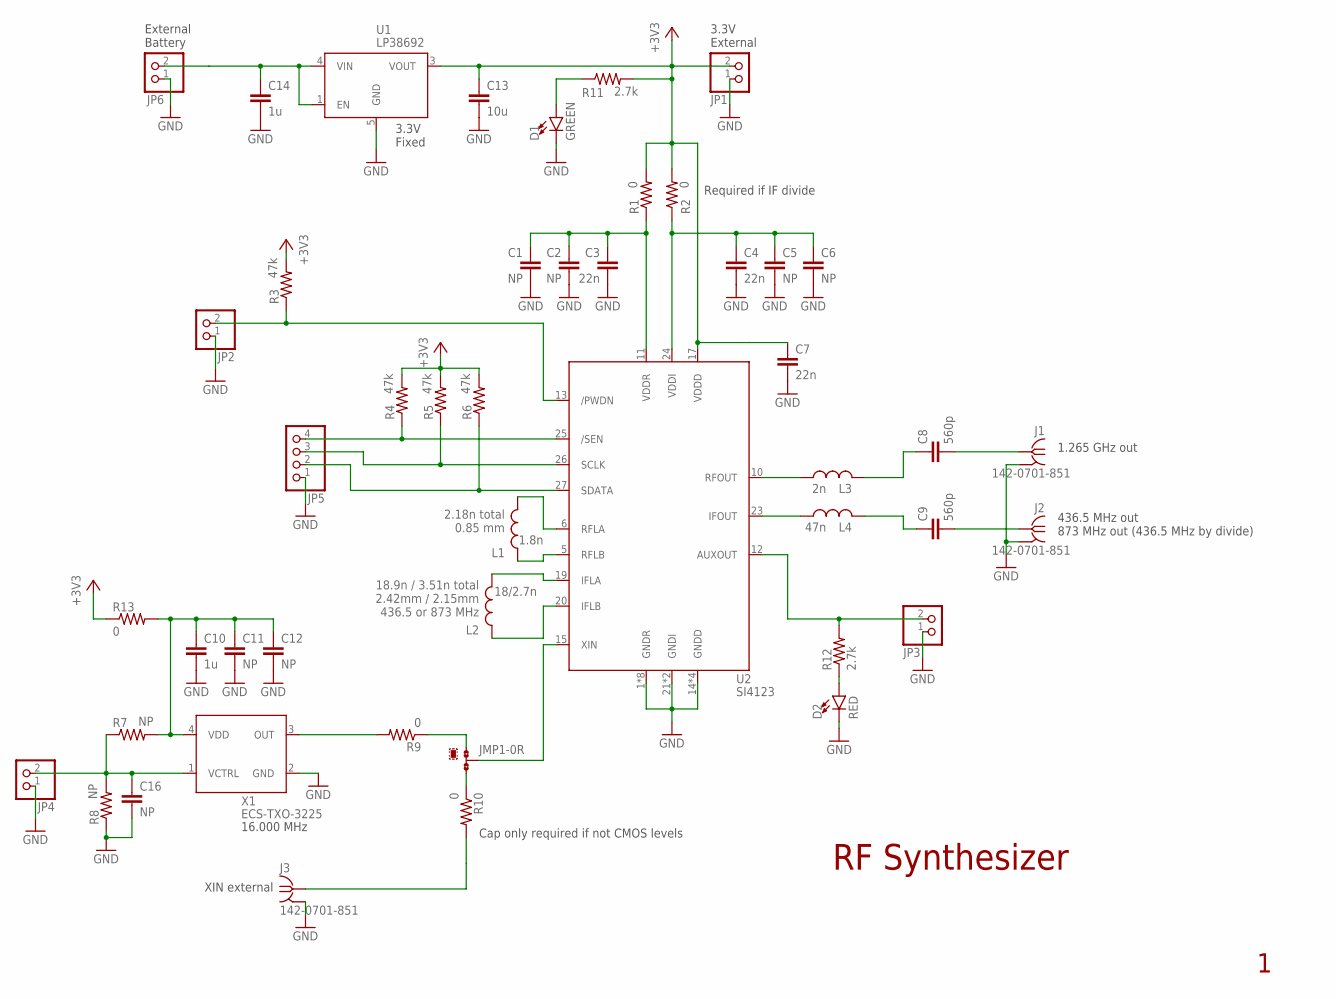
[picture p72: schematic synthesizer-RF-Si4123.sch]

Parts:
C1, C2, C5, C6, C11, C12, C16: NP; .0603-B-NOSILK
C3, C4, C7: 22n; .0603-B-NOSILK
C8, C9: 560p; .0402-B-NOSILK
C10, C14: 1u; .0603-B-NOSILK
C13: 10u; .0805-B-NOSILK
D1: GREEN; LED-0603
D2: RED; LED-0603
J1, J2, J3: 142-0701-851
JMP1: 0R-JUMPA; A0R-JMP
JP1, JP2, JP3, JP4, JP6: PINHD-1X2; 1X02
JP5: PINHD-1X4; 1X04
L1: 1.8n; .0402-C-NOSILK
L2: 18/2.7n; .0402-C-NOSILK
L3: 2n; .0402-B-NOSILK
L4: 47n; .0402-B-NOSILK
R1, R2, R13: 0; .0603-B-NOSILK
R3, R4, R5, R6: 47k; .0402-B-NOSILK
R7, R8: NP; .0603-B-NOSILK
R9, R10: 0; .0402-B-NOSILK
R11, R12: 2.7k; .0603-B-NOSILK
U1: LP38692; SOT223-5
U2: SI4123; QFN28-5X5-WITH-CENTER-PAD
X1: ECS-TXO-3225; 3.2X2.5

Connections:
+3V3: C7.1, C13.1, JP1.2, R1.2, R2.2, R3.2, R4.2, R5.2, R6.2, R11.2, R13.1, U1.3 (VOUT), U2.17 (VDDD)
+BAT: C14.1, JP6.2, U1.1 (EN), U1.4 (VIN)
GND: C1.2, C2.2, C3.2, C4.2, C5.2, C6.2, C7.2, C10.2, C11.2, C12.2, C13.2, C14.2, C16.2, D1.C, D2.C, J1.GND1 (GND), J1.GND2 (GND), J1.GND3 (GND), J1.GND4 (GND), J2.GND1 (GND), J2.GND2 (GND), J2.GND3 (GND), J2.GND4 (GND), J3.GND1 (GND), J3.GND2 (GND), J3.GND3 (GND), J3.GND4 (GND), JP1.1, JP2.1, JP3.1, JP4.1, JP5.1, JP6.1, R8.1, U1.5 (GND), U2.1 (GNDR), U2.2 (GNDR), U2.3 (GNDR), U2.4 (GNDR), U2.7 (GNDR), U2.8 (GNDR), U2.9 (GNDR), U2.14 (GNDD), U2.16 (GNDD), U2.18 (GNDD), U2.21 (GNDI), U2.22 (GNDI), U2.28 (GNDR), U2.PAD (GNDD), X1.2 (GND)
IF_OUT: C9.2, J2.RF1 (RF)
unnamed: JMP1.3, R10.1
unnamed: L1.2, U2.6 (RFLA)
unnamed: L1.1, U2.5 (RFLB)
unnamed: JP2.2, R3.1, U2.13 (/PWDN)
unnamed: JP5.4, R4.1, U2.25 (/SEN)
unnamed: JP5.3, R5.1, U2.26 (SCLK)
unnamed: JP5.2, R6.1, U2.27 (SDATA)
unnamed: JP3.2, R12.2, U2.12 (AUXOUT)
unnamed: JMP1.1, R9.1
unnamed: C10.1, C11.1, C12.1, R7.2, R13.2, X1.4 (VDD)
unnamed: C9.1, L4.2
unnamed: L4.1, U2.23 (IFOUT)
unnamed: C8.1, L3.2
unnamed: C1.1, C2.1, C3.1, R1.1, U2.11 (VDDR)
unnamed: JMP1.2, U2.15 (XIN)
unnamed: C16.1, JP4.2, R7.1, R8.2, X1.1 (VCTRL)
unnamed: R9.2, X1.3 (OUT)
unnamed: D1.A, R11.1
unnamed: D2.A, R12.1
unnamed: L2.2, U2.19 (IFLA)
unnamed: L2.1, U2.20 (IFLB)
unnamed: L3.1, U2.10 (RFOUT)
unnamed: C4.1, C5.1, C6.1, R2.1, U2.24 (VDDI)
REF_IN: J3.RF1 (RF), R10.2
RF_OUT: C8.2, J1.RF1 (RF)

Notes on the sheet:
RF Synthesizer
2.18n total 0.85 mm
Required if IF divide
Cap only required if not CMOS levels
1.265 GHz out
436.5 MHz out 873 MHz out (436.5 MHz by divide)
XIN external
3.3V External
16.000 MHz
External Battery
3.3V Fixed
18.9n / 3.51n total 2.42mm / 2.15mm 436.5 or 873 MHz

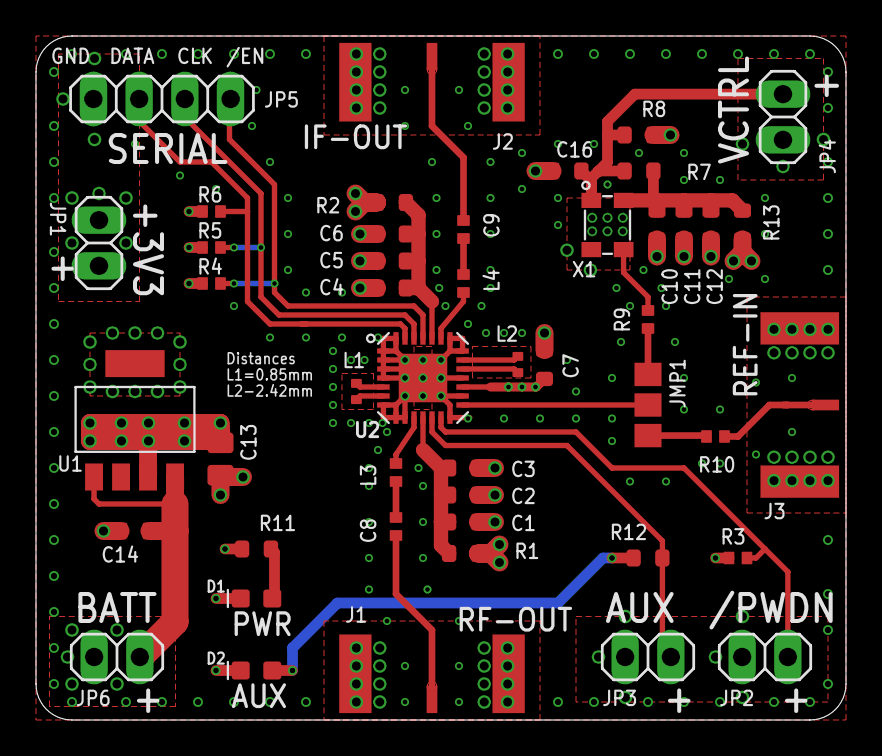
[picture p73: board synthesizer-RF-Si4123.brd from above]

Board: 4 copper layers, 45.0 x 38.0 mm, 47 parts (0 on the bottom side), 29 nets.
