oresat/oresat-c3-rf/eagle/ax5032-module-breakout/DVK2C-breakout.brd

## EAGLE design eagle/ax5032-module-breakout/DVK2C-breakout.brd (2019-08-08)

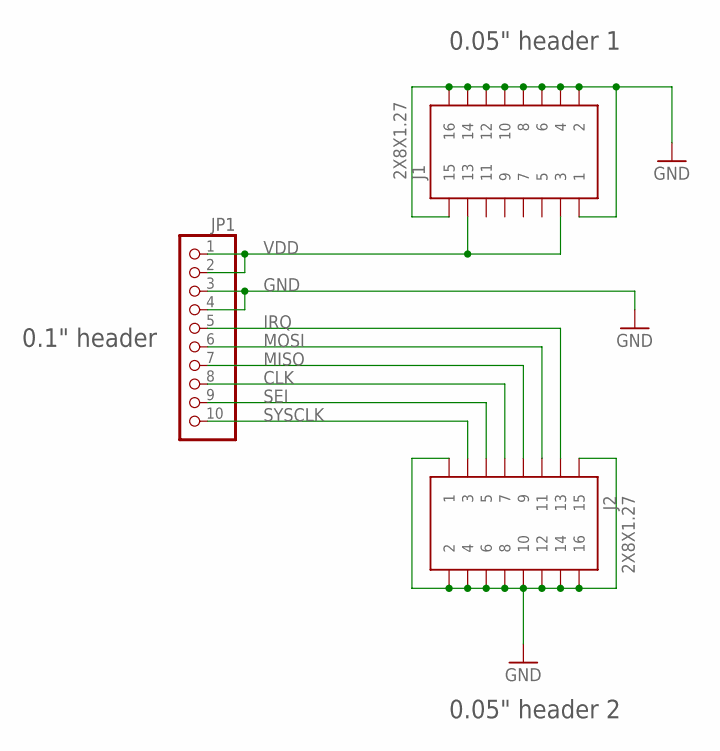
[picture p74: schematic DVK2C-breakout.sch]

Parts:
J1, J2: 2X8X1.27
JP1: PINHD-1X10; 1X10

Connections:
CLK: J2.7, JP1.8
GND: J1.1, J1.2, J1.4, J1.6, J1.8, J1.10, J1.12, J1.14, J1.15, J1.16, J2.1, J2.2, J2.4, J2.6, J2.8, J2.10, J2.12, J2.14, J2.15, J2.16, JP1.3, JP1.4
IRQ: J2.13, JP1.5
MISO: J2.9, JP1.7
MOSI: J2.11, JP1.6
SEI: J2.5, JP1.9
SYSCLK: J2.3, JP1.10
VDD: J1.3, J1.13, JP1.1, JP1.2

Notes on the sheet:
0.1" header
0.05" header 1
0.05" header 2

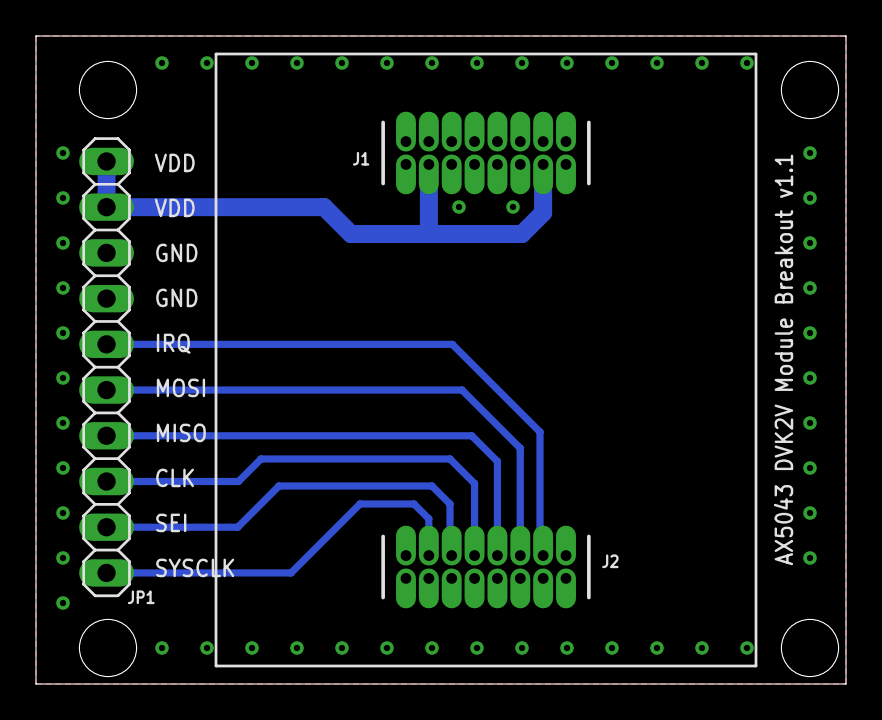
[picture p75: board DVK2C-breakout.brd from above]

Board: 2 copper layers, 45.0 x 36.0 mm, 3 parts (0 on the bottom side), 8 nets.
