oresat/oresat-c3-rf/AxSem_Profiles/AX_C3_L_RX/COMMON/easyax5043.h

/**
*******************************************************************************************************
* @file easyax5043.h
* @brief Definition for Radio communication states
* @internal
* @author   Thomas Sailer, Janani Chellappan, Srinivasan Tamilarasan, Pradeep Kumar GR
* $Rev: $
* $Date: $
********************************************************************************************************
* Copyright 2016 Semiconductor Components Industries LLC (d/b/a “ON Semiconductor”).
* All rights reserved.  This software and/or documentation is licensed by ON Semiconductor
* under limited terms and conditions.  The terms and conditions pertaining to the software
* and/or documentation are available at http://www.onsemi.com/site/pdf/ONSEMI_T&C.pdf
* (“ON Semiconductor Standard Terms and Conditions of Sale, Section 8 Software”) and
* if applicable the software license agreement.  Do not use this software and/or
* documentation unless you have carefully read and you agree to the limited terms and
* conditions.  By using this software and/or documentation, you agree to the limited
* terms and conditions.
*
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
* @ingroup TEMPLATE_FIRMWARE_5043
*
* @details
*/

#ifndef EASYAX5043_H
#define EASYAX5043_H

#include "axradio.h"

#if defined __ARMEL__ || defined __ARMEB__
#include <stdbool.h>
#ifdef __AXM0
#include <axm0f143.h>
#elif defined __AXM0F2
#include <axm0f243.h>
#endif
#else
#include <ax8052f143.h>
#endif
#include <libmftypes.h>

//#define DBGPKT
//#define FREQ_FULL_ADJUST

#define PKTDATA_BUFLEN 260

// typedefs
typedef enum {
	trxstate_off,
	trxstate_rx,
	trxstate_rxwor,
	trxstate_wait_xtal,
	trxstate_xtal_ready,
	trxstate_pll_ranging,
	trxstate_pll_ranging_done,
	trxstate_pll_settling,
	trxstate_pll_settled,
	trxstate_tx_xtalwait,
	trxstate_tx_longpreamble,
	trxstate_tx_shortpreamble,
	trxstate_tx_packet,
	trxstate_tx_waitdone,
	trxstate_txcw_xtalwait,
	trxstate_txstream_xtalwait,
	trxstate_txstream
} axradio_trxstate_t;

#define AXRADIO_ERR_PACKETDONE               0xf0

// declaration of global variables
//hardware
volatile extern axradio_trxstate_t __data axradio_trxstate;

extern uint8_t __data EASY_RADIO_ax5043_powermode_after_send_packet; //used by EASY_RADIO_send_packet() default is powerdown
extern uint8_t __data EASY_RADIO_ax5043_powermode_after_rx_packet; // used by EASY_RADIO_radio_isr() upon FIFO not empty, default is powerdown

//packet
extern volatile uint8_t __data EASY_RADIO_saved_radiostate;
#if defined(__ARMEL__) || defined(__ARMEB__)
extern const bool txondemand_mode;
extern const bool AxM0_Mini_Kit;
#endif //#if defined(__ARMEL__) || defined(__ARMEB__)

// additional AX5043 registers & definitions

/**#define AX5043_REG_0xF00                    0xf00
#define AX5043_REG_0xF0C                    0xf0c
#define AX5043_REG_0xF10                    0xf10
#define AX5043_REG_0xF11                    0xf11
#define AX5043_REG_0xF18                    0xf18
#define AX5043_REG_0xF1C                    0xf1c
#define AX5043_REG_0xF21                    0xf21
#define AX5043_REG_0xF22                    0xf22
#define AX5043_REG_0xF23                    0xf23
#define AX5043_REG_0xF26                    0xf26
#define AX5043_REG_0xF30                    0xf30
#define AX5043_REG_0xF31                    0xf31
#define AX5043_REG_0xF32                    0xf32
#define AX5043_REG_0xF33                    0xf33
#define AX5043_REG_0xF34                    0xf34
#define AX5043_REG_0xF35                    0xf35
#define AX5043_REG_0xF44                    0xf44

#define AX5043_REG_REF                      0xf0d
#define AX5043_REG_POWCTRL1                 0xf08
#define AX5043_REG_MODCFGP                  0xf5f
#define AX5043_REG_XTALOSC                  0xf10
#define AX5043_REG_XTALAMPL                 0xf11 **/

// power states
#define AX5043_PWRSTATE_POWERDOWN           0x0
#define AX5043_PWRSTATE_DEEPSLEEP           0x1
#define AX5043_PWRSTATE_REGS_ON             0x4
#define AX5043_PWRSTATE_XTAL_ON             0x5
#define AX5043_PWRSTATE_FIFO_ON             0x7
#define AX5043_PWRSTATE_SYNTH_RX            0x8
#define AX5043_PWRSTATE_FULL_RX             0x9
#define AX5043_PWRSTATE_WOR_RX              0xb
#define AX5043_PWRSTATE_SYNTH_TX            0xc
#define AX5043_PWRSTATE_FULL_TX             0xd

//fifo commands
#define AX5043_FIFOCMD_NOP                  0x00
#define AX5043_FIFOCMD_DATA                 0x01
#define AX5043_FIFOCMD_REPEATDATA           0x02
#define AX5043_FIFOCMD_TIMER                0x10
#define AX5043_FIFOCMD_RSSI                 0x11
#define AX5043_FIFOCMD_FREQOFFS             0x12
#define AX5043_FIFOCMD_RFFREQOFFS           0x13
#define AX5043_FIFOCMD_DATARATE             0x14
#define AX5043_FIFOCMD_ANTRSSI              0x15
#define AX5043_FIFOCMD_TXCTRL               0x1C
#define AX5043_FIFOCMD_TXPWR                0x1D


void axradio_wait_for_xtal(void);

__reentrantb void ax5043_receiver_on_continuous(void) __reentrant;
__reentrantb void ax5043_receiver_on_wor(void) __reentrant;
__reentrantb void ax5043_off(void) __reentrant;
__reentrantb void ax5043_off_xtal(void) __reentrant;
__reentrantb void ax5043_prepare_tx(void) __reentrant;

// funtions implemented in AX_Radio_output/config.c
__reentrantb int32_t axradio_conv_freq_fromreg(int32_t f) __reentrant;
__reentrantb void ax5043_set_registers(void) __reentrant;
__reentrantb void ax5043_set_registers_tx(void) __reentrant;
__reentrantb void ax5043_set_registers_rx(void) __reentrant;
__reentrantb void ax5043_set_registers_rxwor(void) __reentrant;
__reentrantb void ax5043_set_registers_rxcont(void) __reentrant;
__reentrantb void ax5043_set_registers_rxcont_singleparamset(void) __reentrant;
__reentrantb uint16_t axradio_framing_check_crc(uint8_t __xdata *pkt, uint16_t cnt) __reentrant;
__reentrantb uint16_t axradio_framing_append_crc(uint8_t __xdata *pkt, uint16_t cnt) __reentrant;


// physical layer
extern const uint8_t __code axradio_phy_pn9;
extern const uint8_t __code axradio_phy_nrchannels;
extern const uint32_t __code axradio_phy_chanfreq[];
extern const uint16_t __code axradio_phy_chanpllrnginit[];
extern const uint8_t __code axradio_phy_chanvcoiinit[];
extern uint16_t __xdata axradio_phy_chanpllrng[];
extern uint8_t __xdata axradio_phy_chanvcoi[];
extern const uint8_t __code axradio_phy_vcocalib;
extern const uint8_t __code axradio_phy_innerfreqloop;
extern const int32_t __code axradio_phy_maxfreqoffset;
extern const int8_t __code axradio_phy_rssioffset;
extern const int8_t __code axradio_phy_rssireference;
extern const int8_t __code axradio_phy_channelbusy;
extern const uint8_t __code axradio_phy_cs_enabled;
extern const uint16_t __code axradio_phy_cs_period;
extern const uint8_t __code axradio_phy_lbt_retries;
extern const uint8_t __code axradio_phy_lbt_forcetx;


extern const uint16_t __code axradio_phy_preamble_wor_longlen;
extern const uint16_t __code axradio_phy_preamble_longlen;
extern const uint16_t __code axradio_phy_preamble_wor_len;
extern const uint16_t __code axradio_phy_preamble_len;
extern const uint8_t __code axradio_phy_preamble_byte;
extern const uint8_t __code axradio_phy_preamble_flags;
extern const uint8_t __code axradio_phy_preamble_appendbits;
extern const uint8_t __code axradio_phy_preamble_appendpattern;

// framing
extern const uint8_t __code axradio_framing_lenpos;
extern const uint8_t __code axradio_framing_lenoffs;
extern const uint8_t __code axradio_framing_lenmask;
extern const uint8_t __code axradio_framing_destaddrpos;
extern const uint8_t __code axradio_framing_sourceaddrpos;

extern const uint8_t __code axradio_framing_synclen;
extern const uint8_t __code axradio_framing_syncword[];
extern const uint8_t __code axradio_framing_syncflags;
extern const uint8_t __code axradio_framing_enable_sfdcallback;
extern const uint8_t __code axradio_framing_swcrclen;


extern const uint32_t __code axradio_framing_ack_timeout;
extern const uint32_t __code axradio_framing_ack_delay;
extern const uint8_t __code axradio_framing_ack_retransmissions;
extern const uint8_t __code axradio_framing_ack_seqnrpos;

extern const uint8_t __code axradio_framing_minpayloadlen;

//WOR
extern const uint16_t __code axradio_wor_period;

// synchronous mode
extern const uint32_t __code axradio_sync_period;
extern const uint32_t __code axradio_sync_xoscstartup;

extern const uint32_t __code axradio_sync_slave_syncwindow;
extern const uint32_t __code axradio_sync_slave_initialsyncwindow;
extern const uint32_t __code axradio_sync_slave_syncpause;
extern const int16_t __code axradio_sync_slave_maxperiod;
extern const uint8_t __code axradio_sync_slave_resyncloss;
extern const uint8_t __code axradio_sync_slave_nrrx;
extern const uint32_t __code axradio_sync_slave_rxadvance[];
extern const uint32_t __code axradio_sync_slave_rxwindow[];
extern const uint32_t __code axradio_sync_slave_rxtimeout;

// LPOSC Oscillator
extern const uint16_t __code axradio_lposckfiltmax;

// XTAL Oscillator
extern const uint32_t __code axradio_fxtal;

#endif /* EASYAX5043_H */
